hardboiledfrog/smt-zvs-driver/images/P1020684.JPG

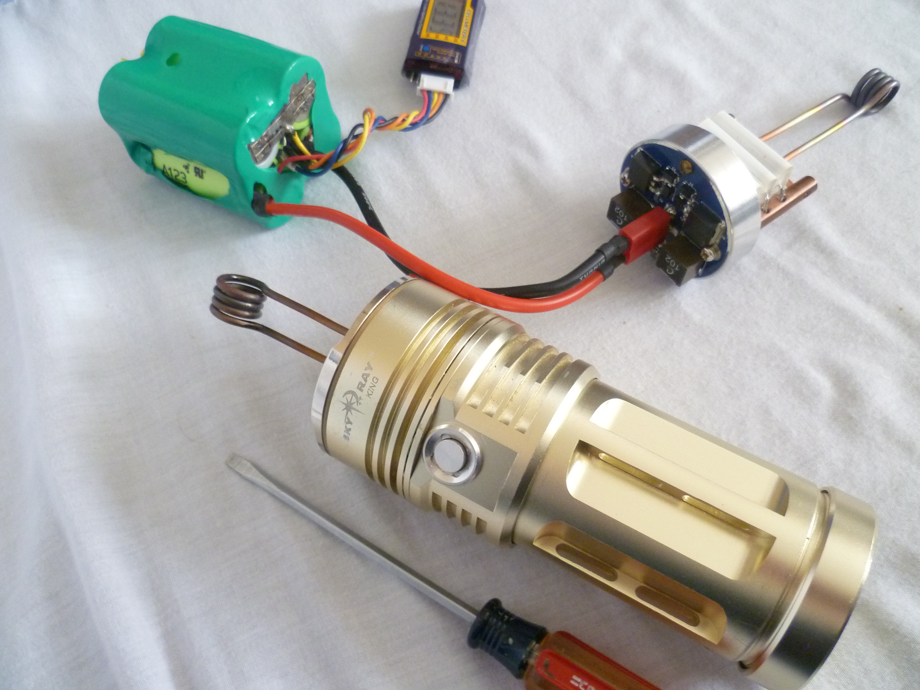
images/P1020684.JPG
