hardboiledfrog/smt-zvs-driver/images/IMG_20150707_065902.jpg

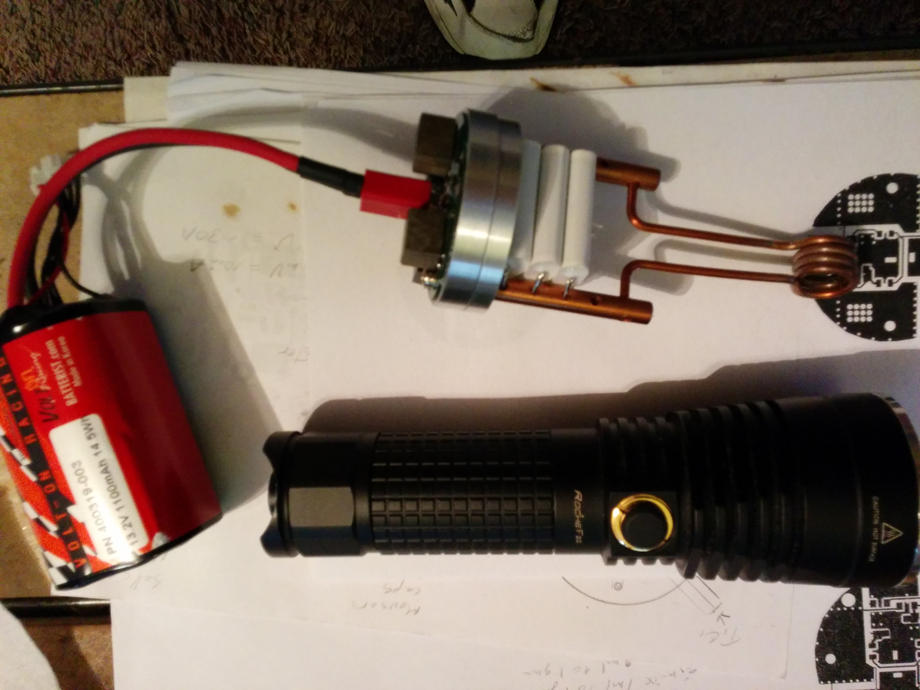
images/IMG_20150707_065902.jpg
