hardboiledfrog/smt-zvs-driver/images/ih-VA.png

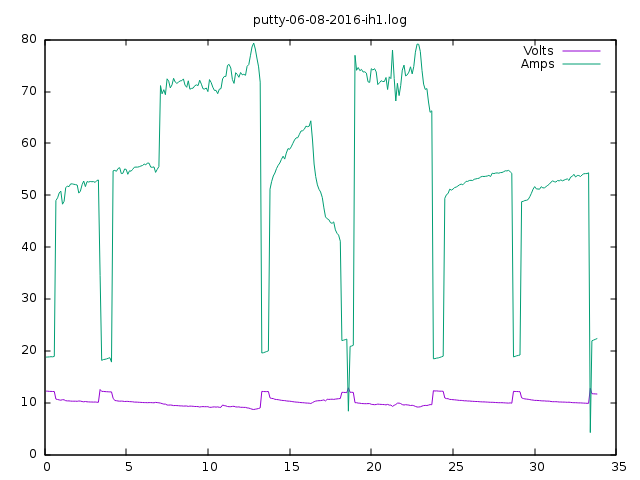
images/ih-VA.png
