hardboiledfrog/smt-zvs-driver/images/ih-VAW.png

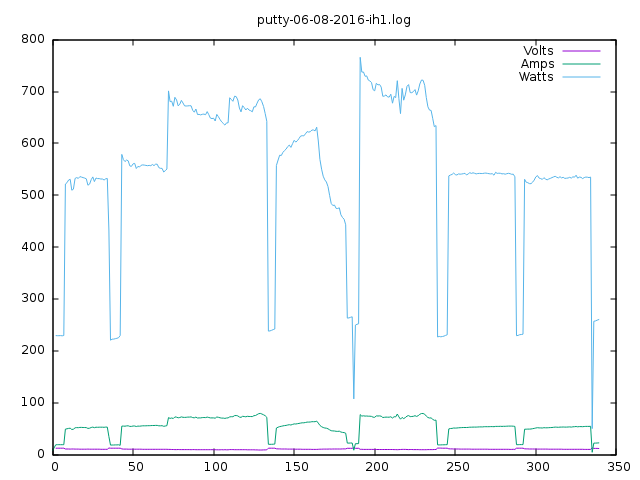
images/ih-VAW.png
