hardboiledfrog/smt-zvs-driver/images/IMG_20150707_065633.jpg

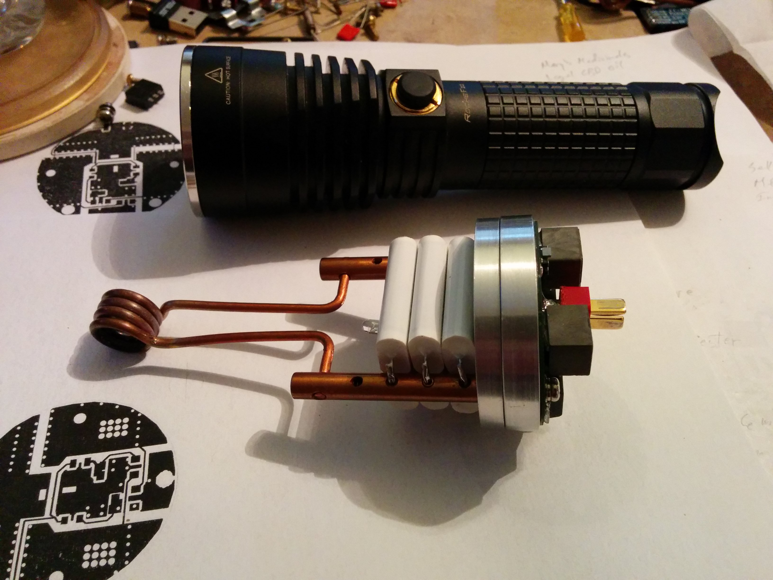
images/IMG_20150707_065633.jpg
