hardboiledfrog/smt-zvs-driver/images/IMG_20150707_065652.jpg

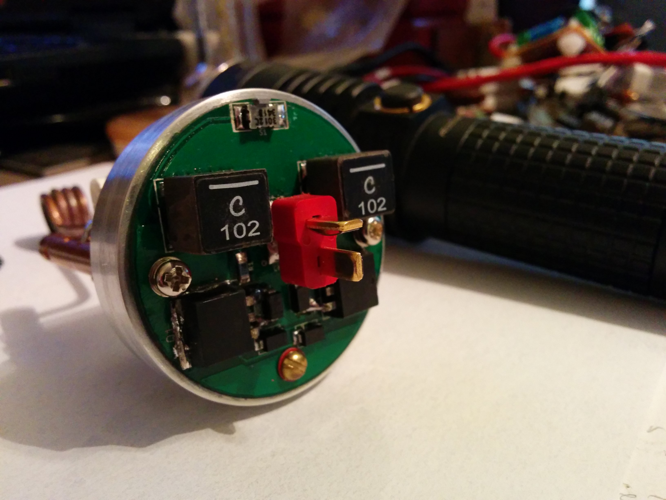
images/IMG_20150707_065652.jpg
