hardboiledfrog/smt-zvs-driver/images/IMG_20150707_065724.jpg

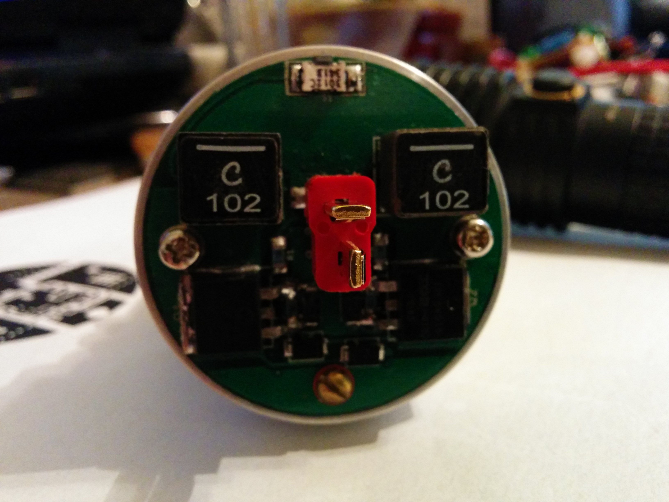
images/IMG_20150707_065724.jpg
