hardboiledfrog/smt-zvs-driver/images/IMG_20160604_112423.jpg

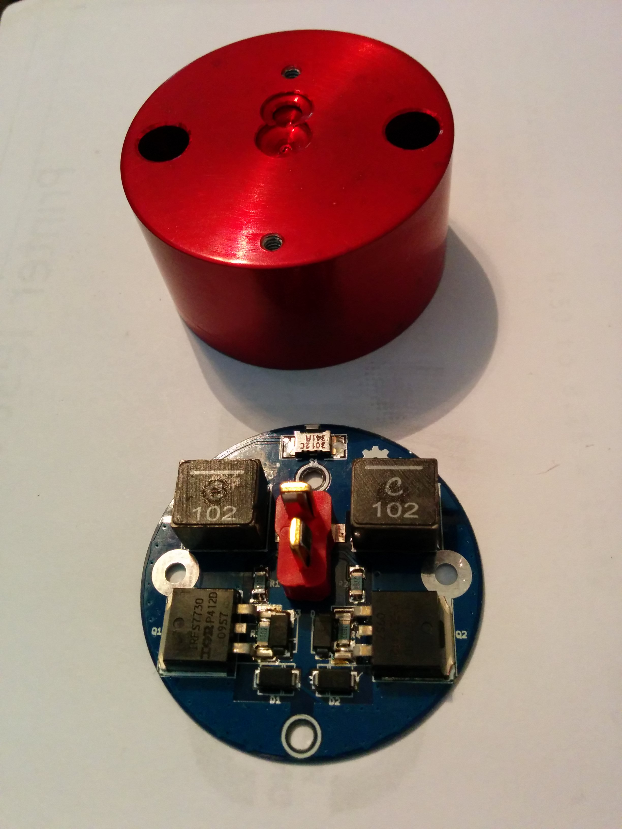
images/IMG_20160604_112423.jpg
