hardboiledfrog/smt-zvs-driver/images/IMG_20160604_112811.jpg

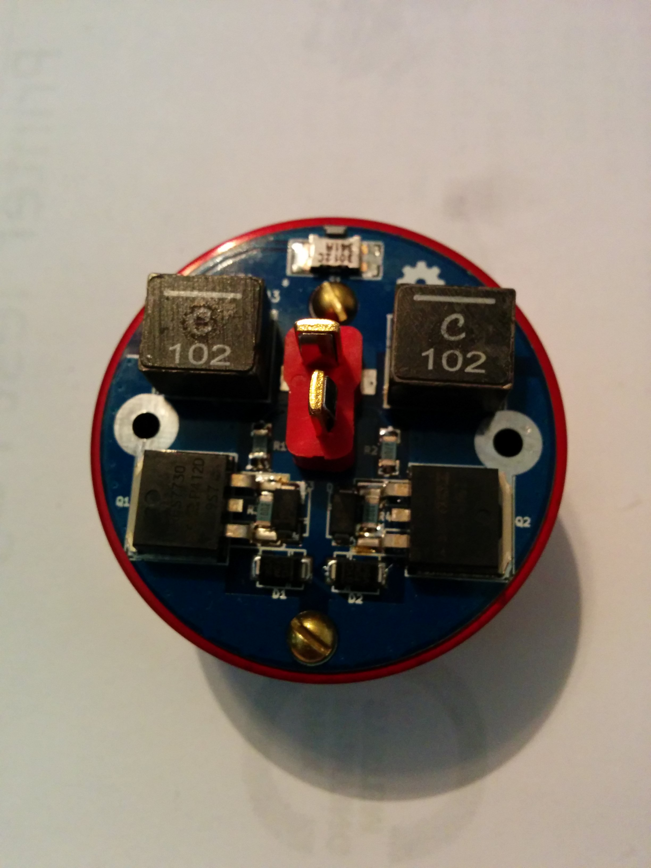
images/IMG_20160604_112811.jpg
