hardboiledfrog/smt-zvs-driver/images/IMG_20160604_112840.jpg

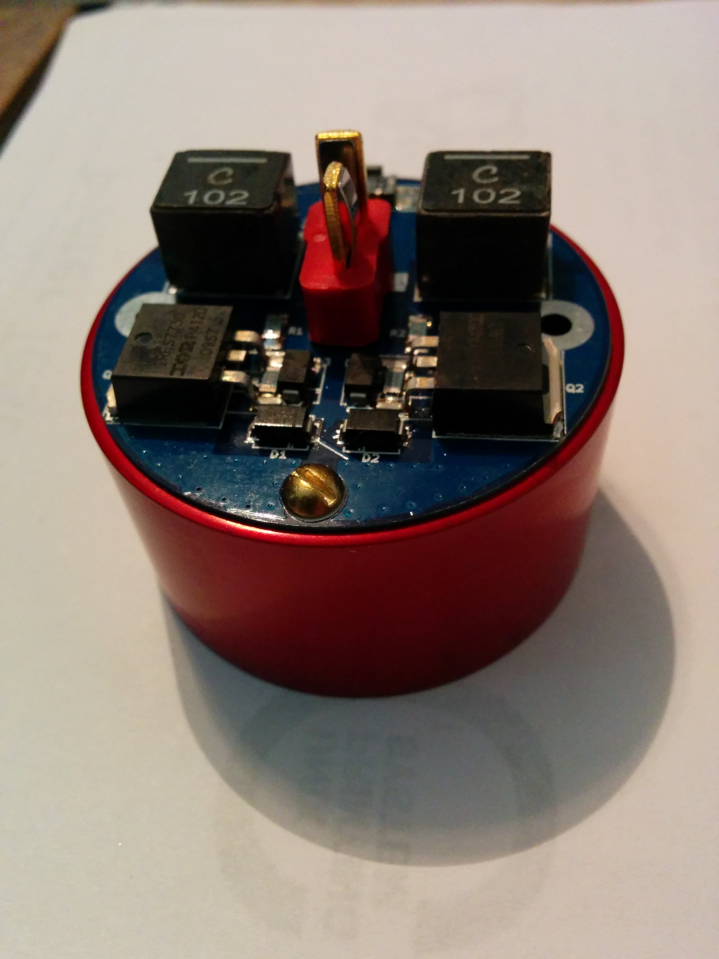
images/IMG_20160604_112840.jpg
