hardboiledfrog/smt-zvs-driver/images/IMG_20160604_114358.jpg

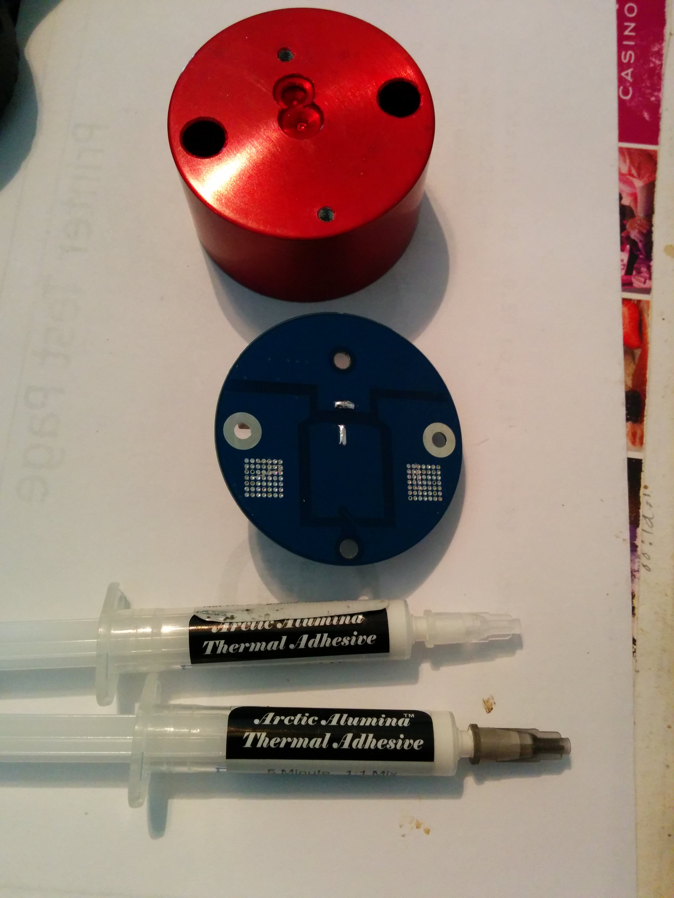
images/IMG_20160604_114358.jpg
