hardboiledfrog/smt-zvs-driver/images/IMG_20160604_115838.jpg

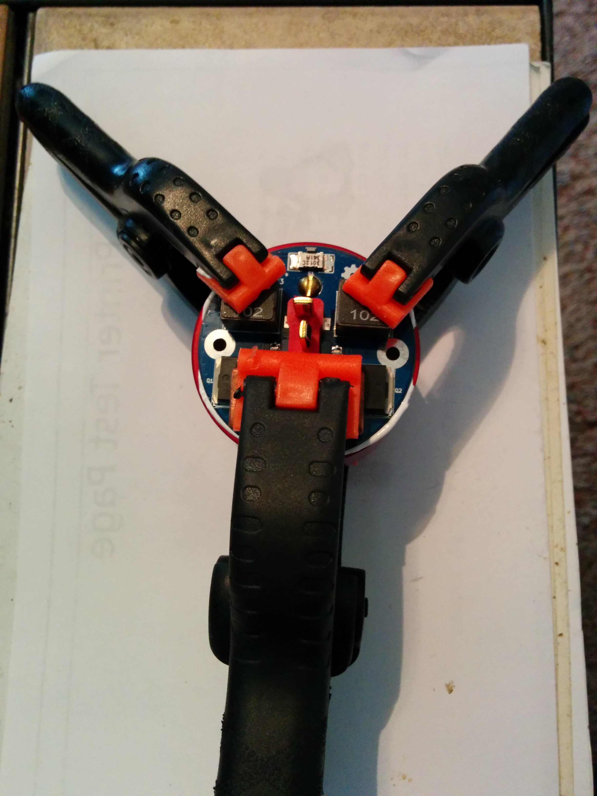
images/IMG_20160604_115838.jpg
