hardboiledfrog/smt-zvs-driver/images/IMG_20160604_115855.jpg

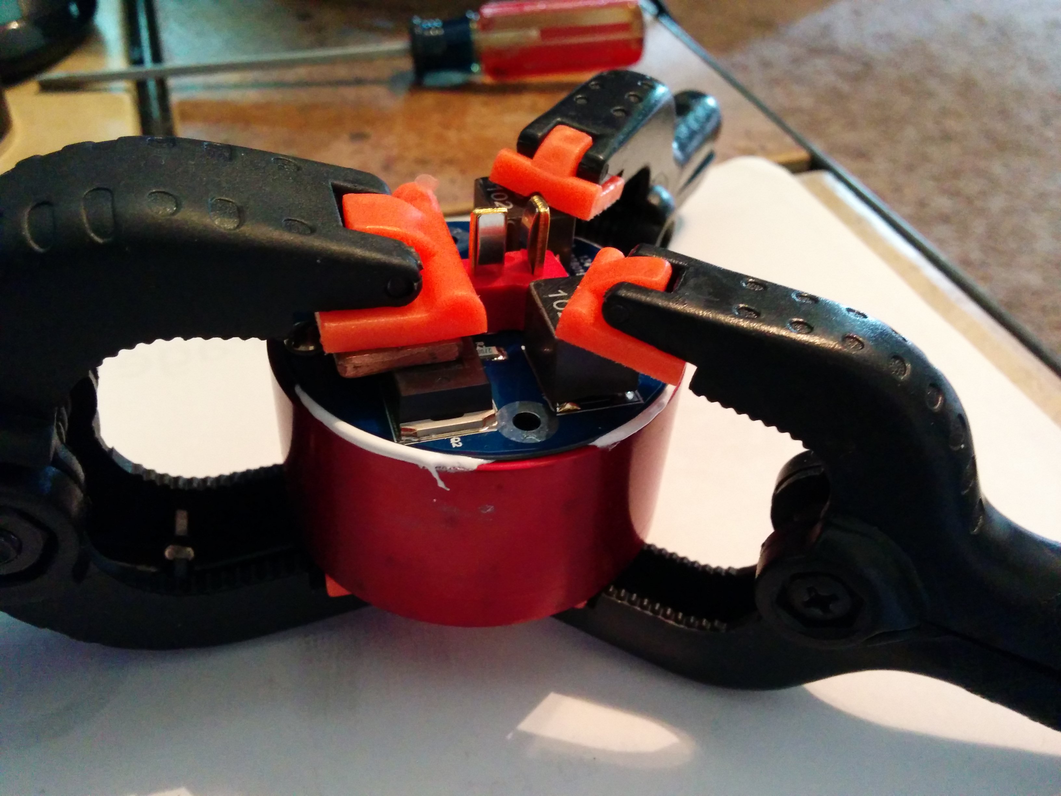
images/IMG_20160604_115855.jpg
