hardboiledfrog/smt-zvs-driver/images/IMG_20160604_143417.jpg

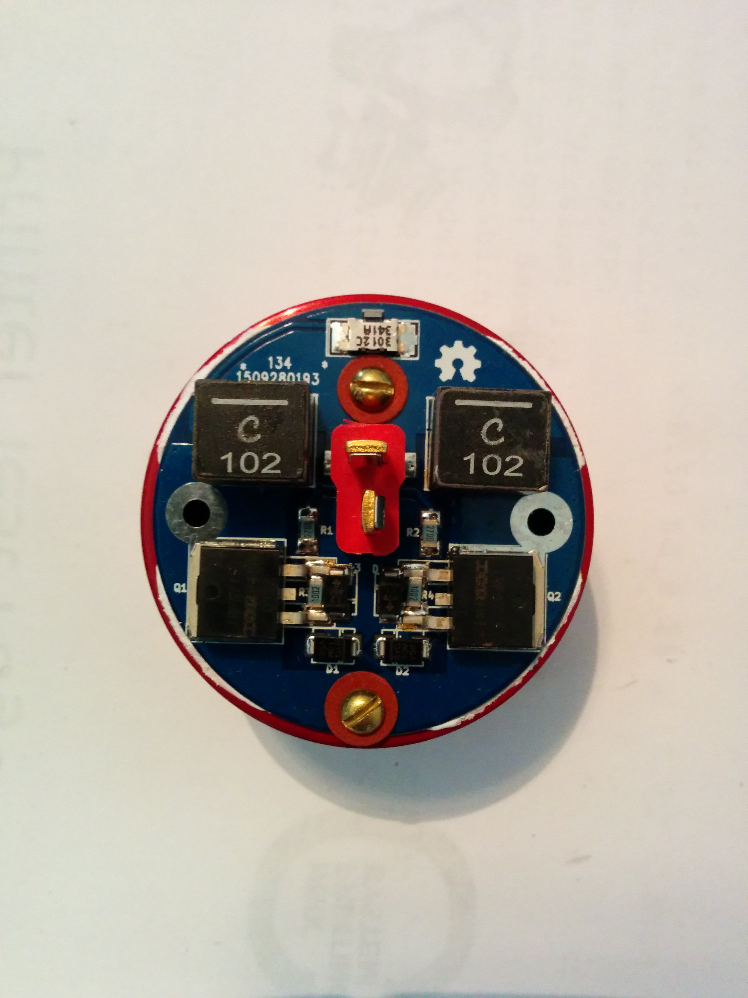
images/IMG_20160604_143417.jpg
