hardboiledfrog/smt-zvs-driver/images/IMG_20160604_143437.jpg

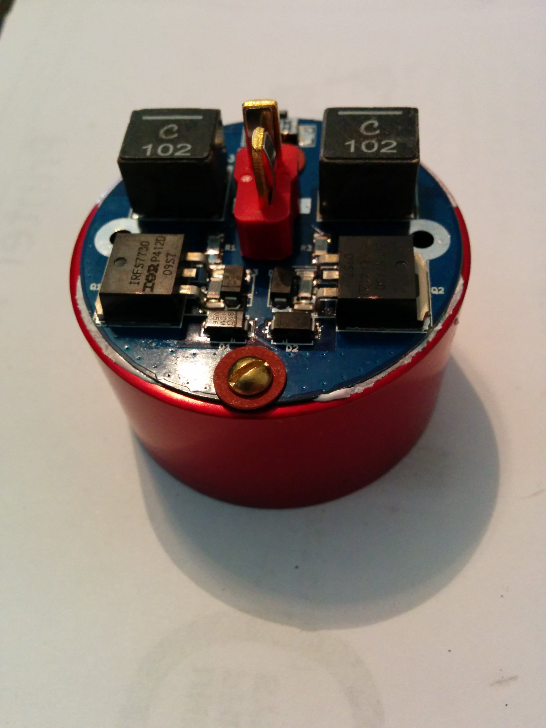
images/IMG_20160604_143437.jpg
