hardboiledfrog/smt-zvs-driver/images/IMG_20160604_143456.jpg

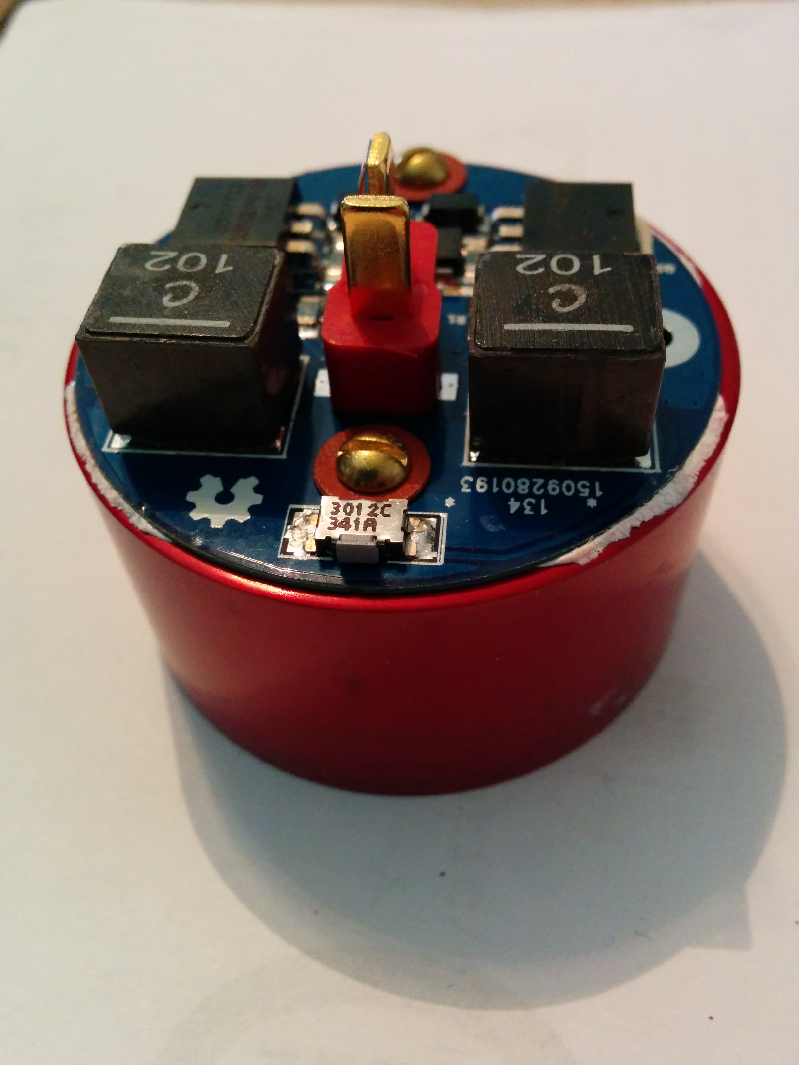
images/IMG_20160604_143456.jpg
