hardboiledfrog/smt-zvs-driver/images/IMG_20160604_174850.jpg

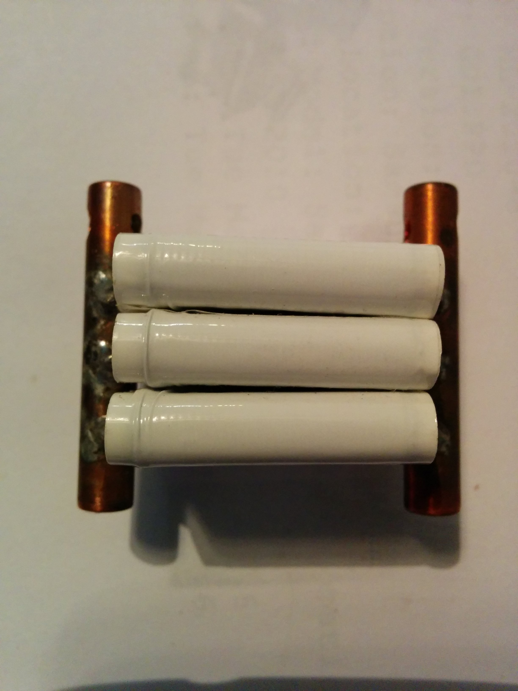
images/IMG_20160604_174850.jpg
