hardboiledfrog/smt-zvs-driver/images/IMG_20160604_174921.jpg

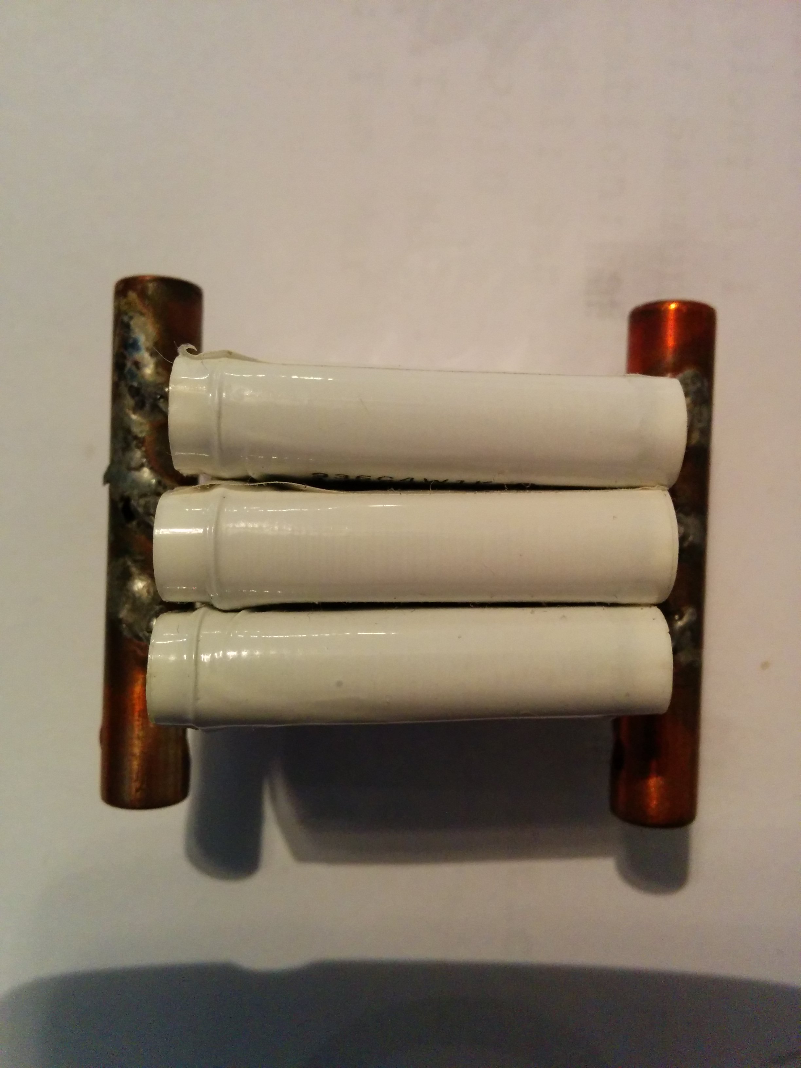
images/IMG_20160604_174921.jpg
