hardboiledfrog/smt-zvs-driver/images/IMG_20160604_174946.jpg

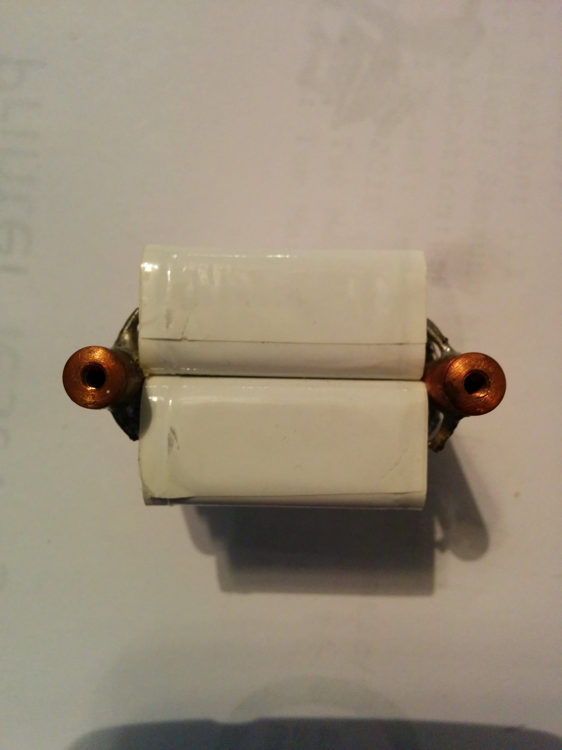
images/IMG_20160604_174946.jpg
