hardboiledfrog/smt-zvs-driver/images/IMG_20160604_175032.jpg

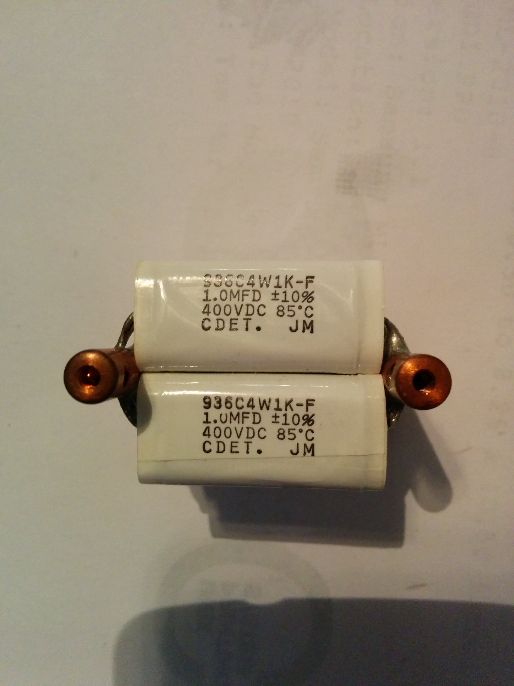
images/IMG_20160604_175032.jpg
