hardboiledfrog/smt-zvs-driver/images/IMG_20160608_041023.jpg

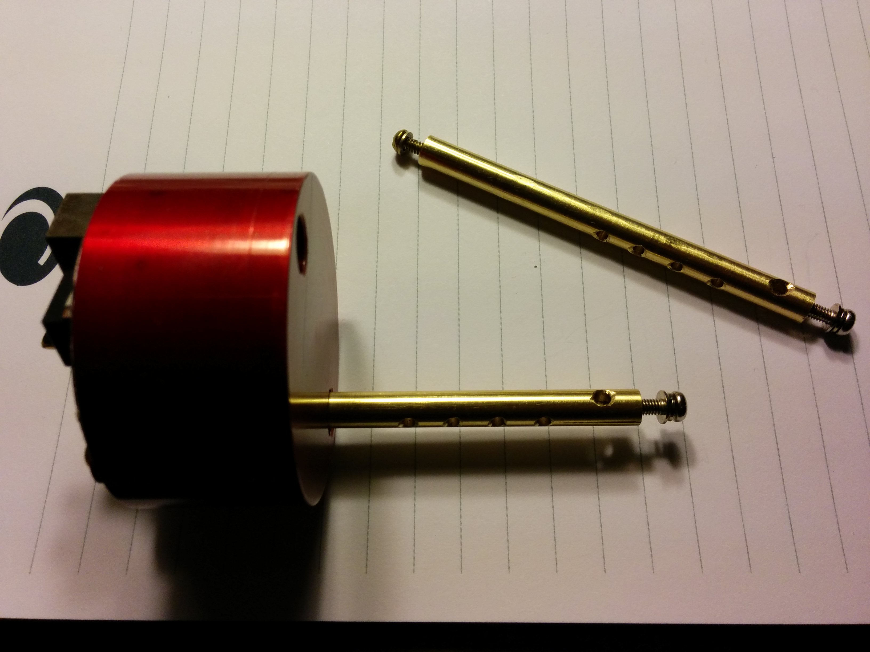
images/IMG_20160608_041023.jpg
