hardboiledfrog/smt-zvs-driver/images/IMG_20160608_041058.jpg

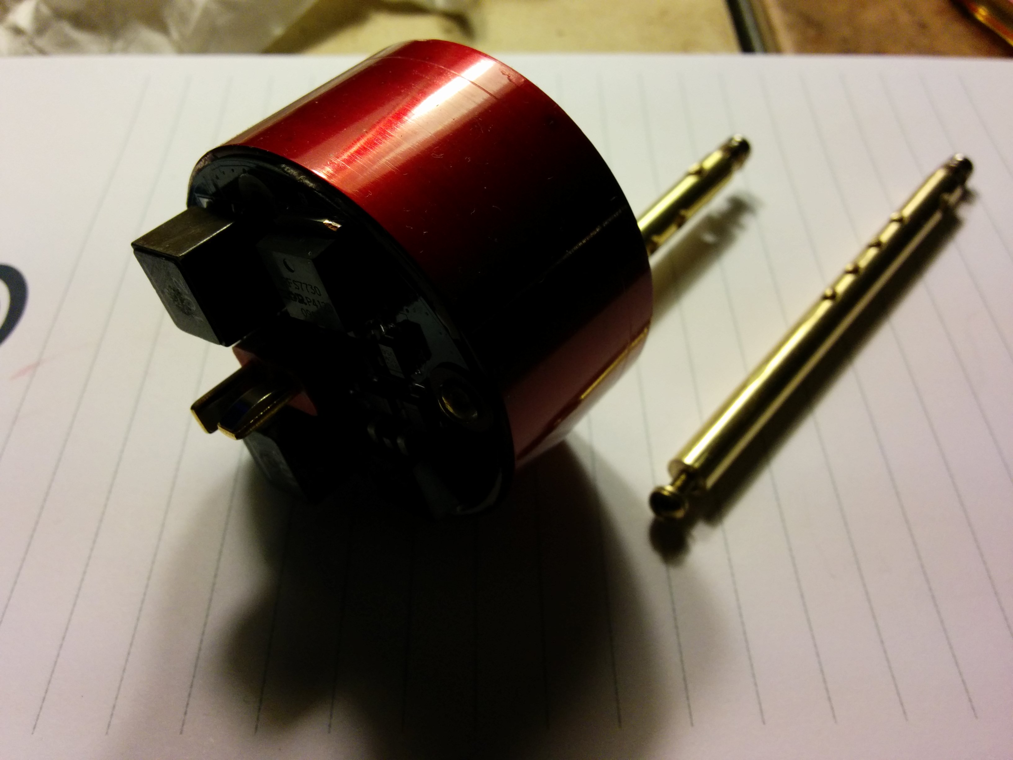
images/IMG_20160608_041058.jpg
