hardboiledfrog/smt-zvs-driver/images/IMG_20160608_041148.jpg

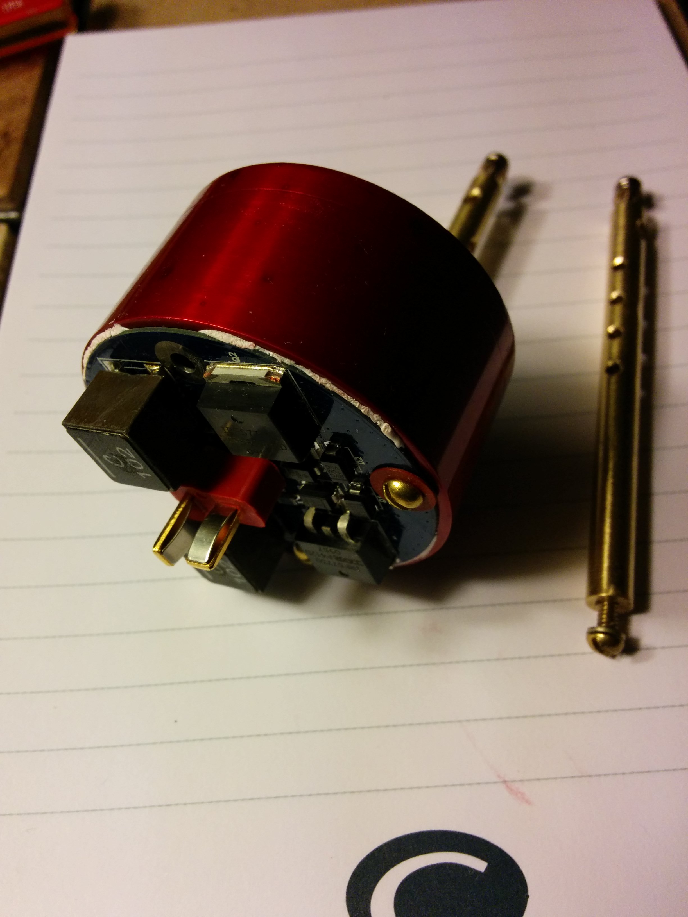
images/IMG_20160608_041148.jpg
