hardboiledfrog/smt-zvs-driver/images/IMG_20160608_041308.jpg

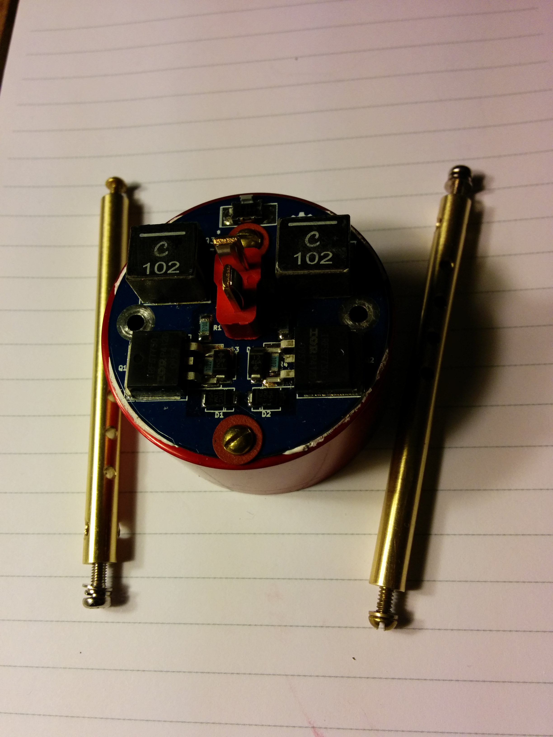
images/IMG_20160608_041308.jpg
