hardboiledfrog/smt-zvs-driver/images/IMG_20160608_041708.jpg

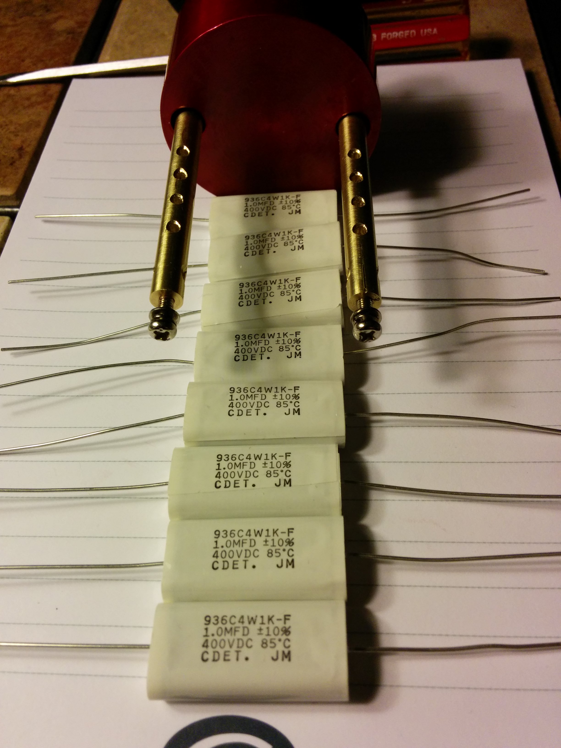
images/IMG_20160608_041708.jpg
