hardboiledfrog/smt-zvs-driver/images/IMG_20160608_041847.jpg

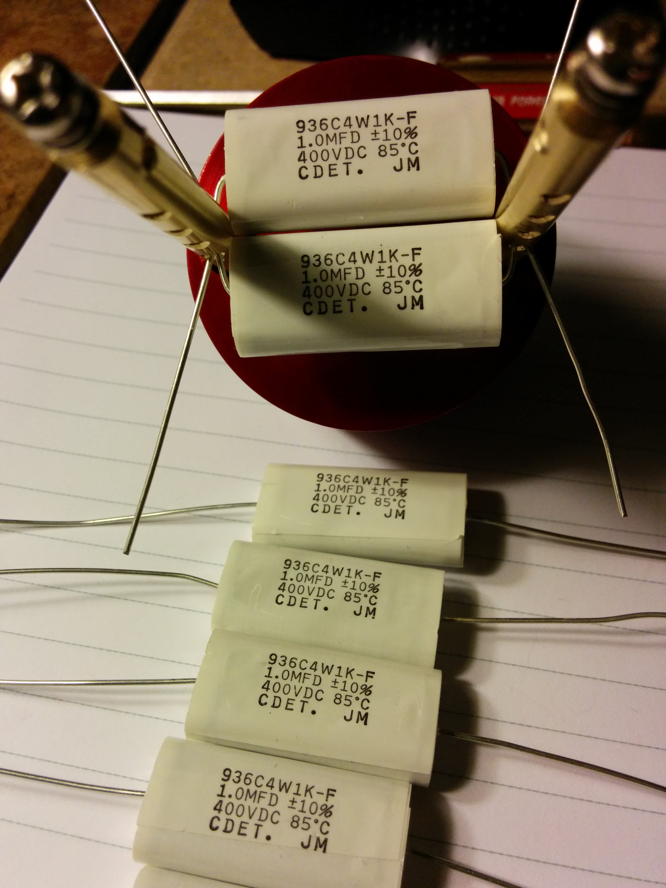
images/IMG_20160608_041847.jpg
