hardboiledfrog/smt-zvs-driver/images/IMG_20160608_041959.jpg

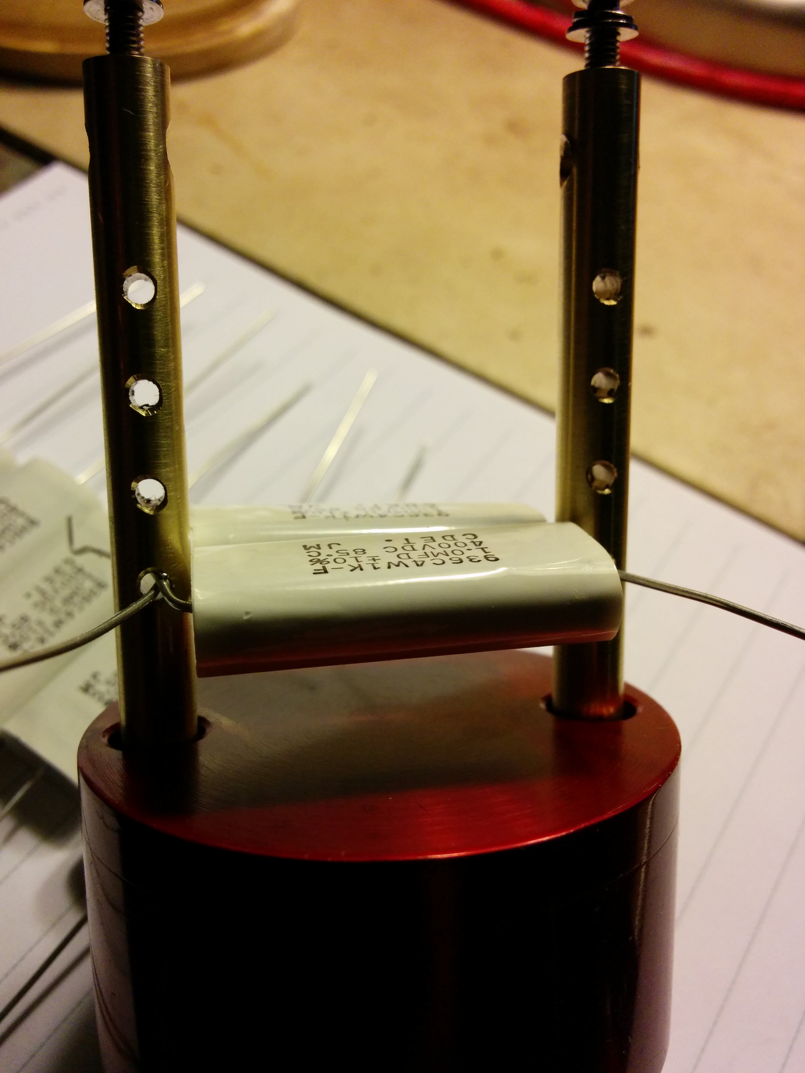
images/IMG_20160608_041959.jpg
