hardboiledfrog/smt-zvs-driver/images/IMG_20160608_042007.jpg

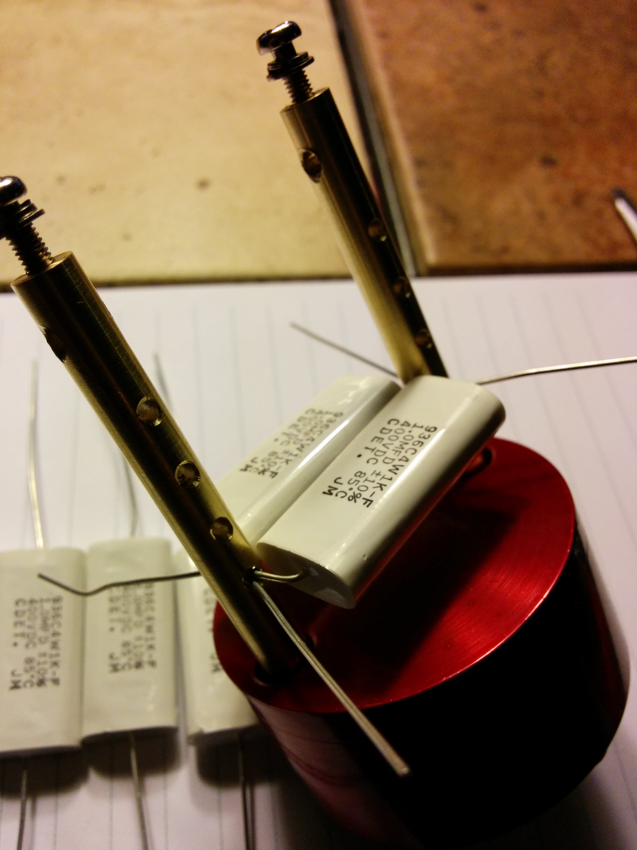
images/IMG_20160608_042007.jpg
