hardboiledfrog/smt-zvs-driver/images/IMG_20160608_043600.jpg

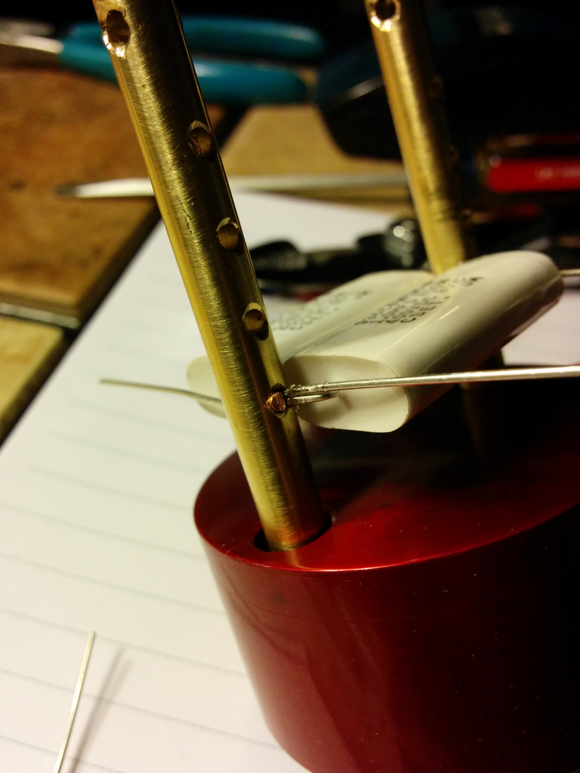
images/IMG_20160608_043600.jpg
