hardboiledfrog/smt-zvs-driver/images/IMG_20160608_043638.jpg

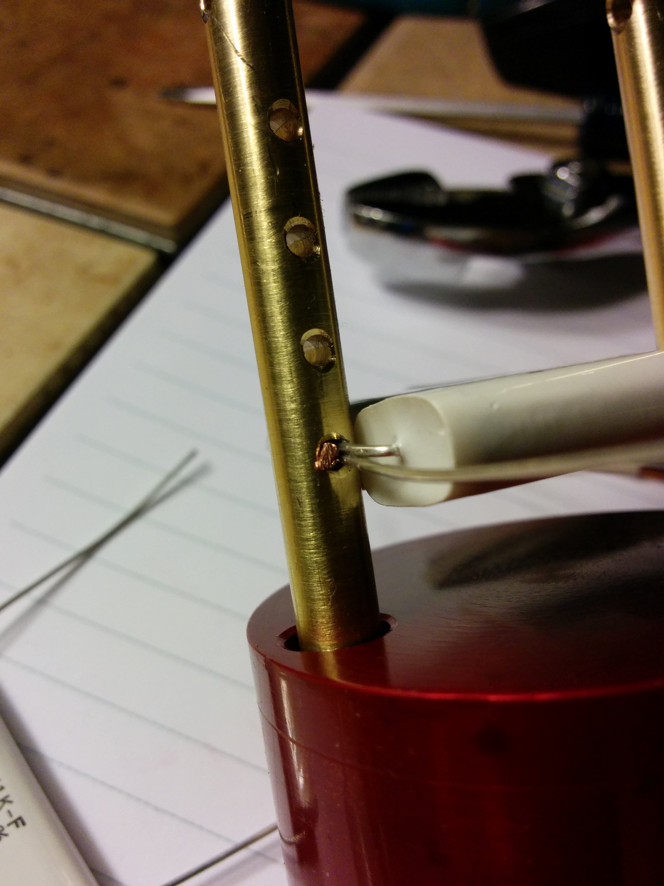
images/IMG_20160608_043638.jpg
