hardboiledfrog/smt-zvs-driver/images/IMG_20160608_043737.jpg

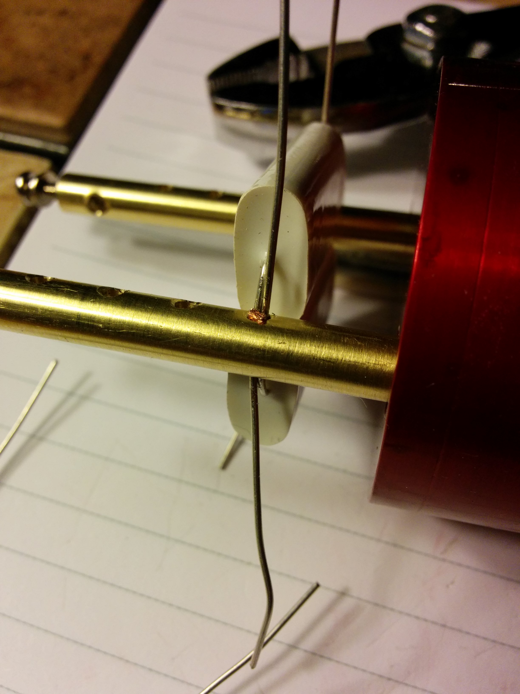
images/IMG_20160608_043737.jpg
