hardboiledfrog/smt-zvs-driver/images/IMG_20160608_044013.jpg

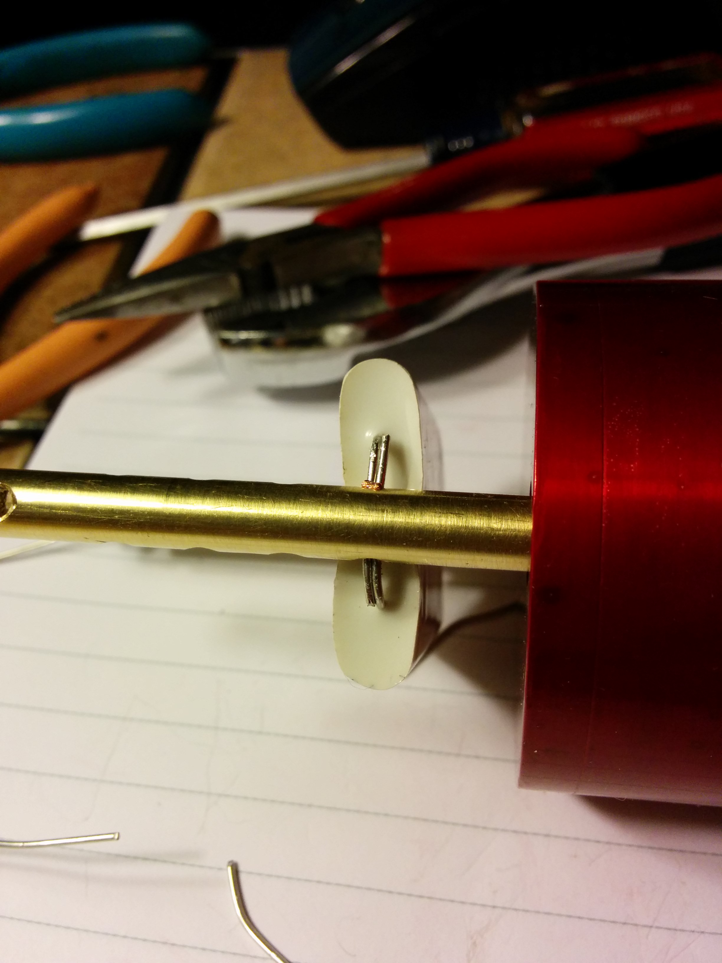
images/IMG_20160608_044013.jpg
