hardboiledfrog/smt-zvs-driver/images/IMG_20160608_044214.jpg

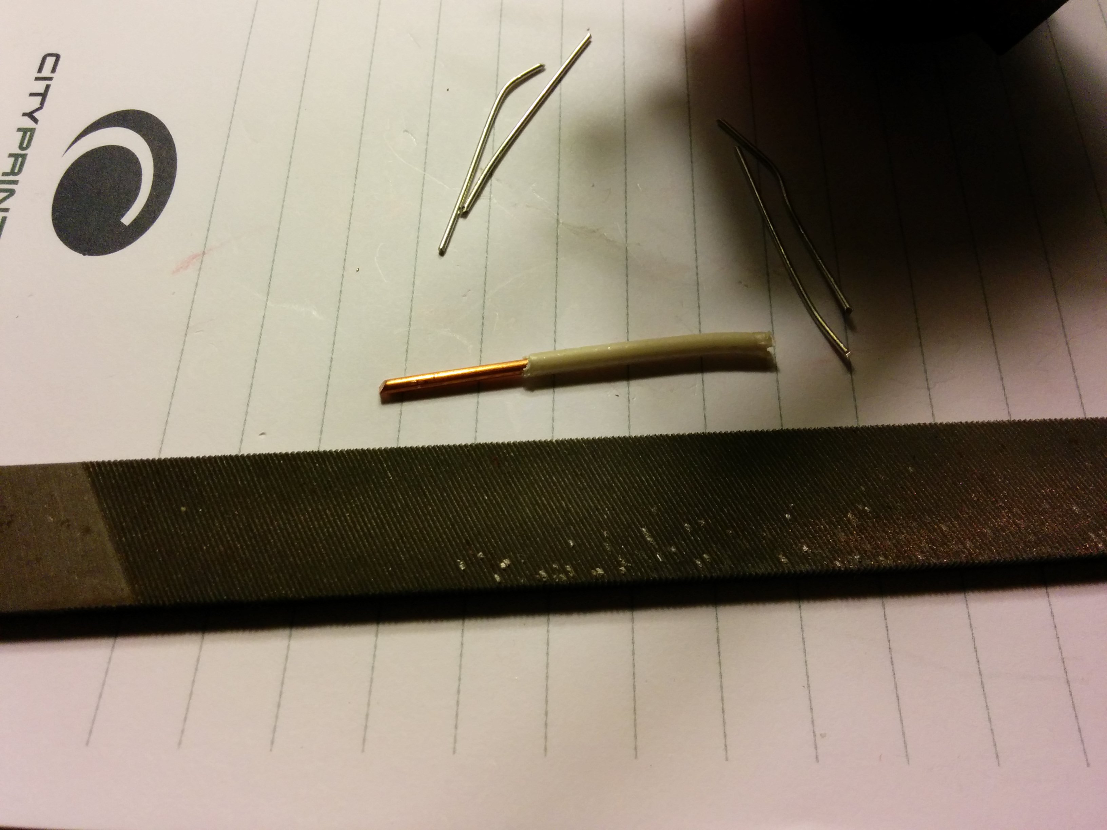
images/IMG_20160608_044214.jpg
