hardboiledfrog/smt-zvs-driver/images/IMG_20160608_044324.jpg

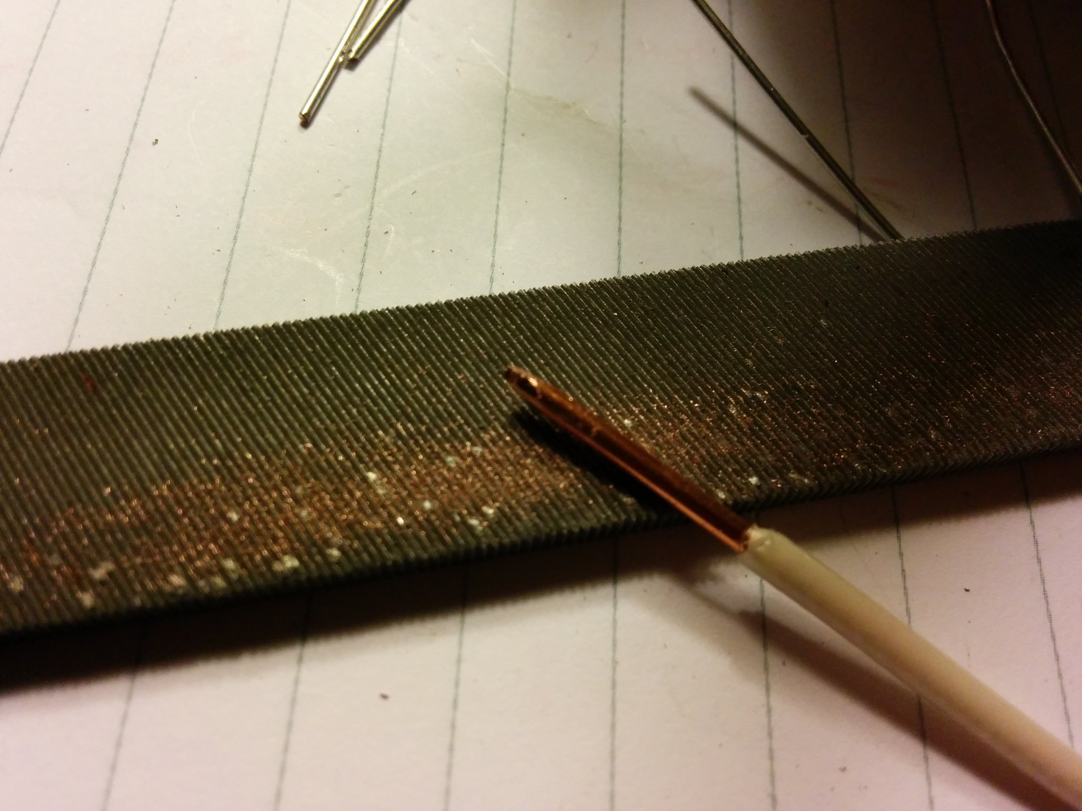
images/IMG_20160608_044324.jpg
