hardboiledfrog/smt-zvs-driver/images/IMG_20160608_044334.jpg

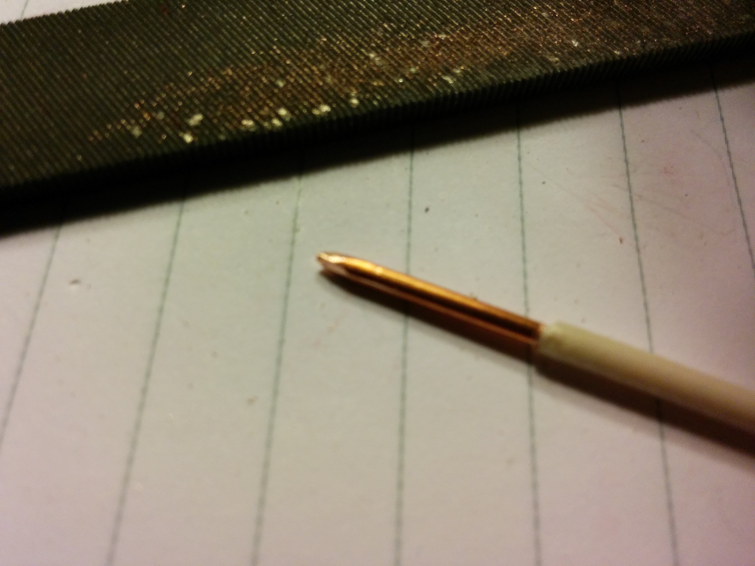
images/IMG_20160608_044334.jpg
