hardboiledfrog/smt-zvs-driver/images/IMG_20160608_044416.jpg

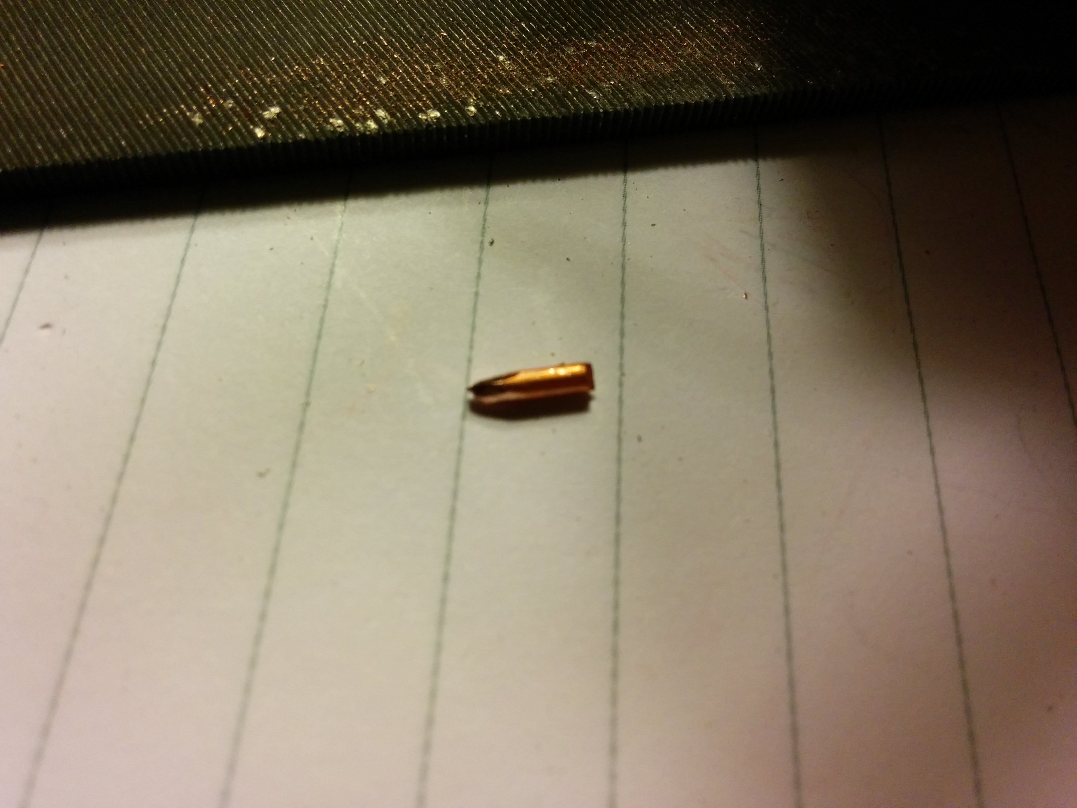
images/IMG_20160608_044416.jpg
