hardboiledfrog/smt-zvs-driver/images/IMG_20160608_044534.jpg

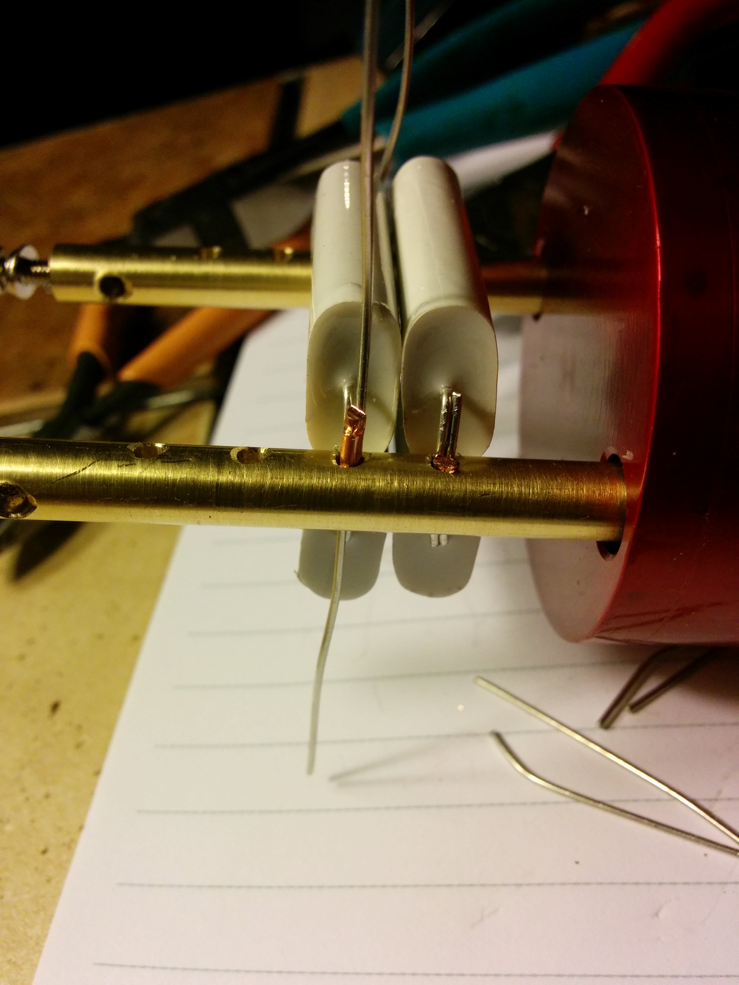
images/IMG_20160608_044534.jpg
