hardboiledfrog/smt-zvs-driver/images/IMG_20160608_044605.jpg

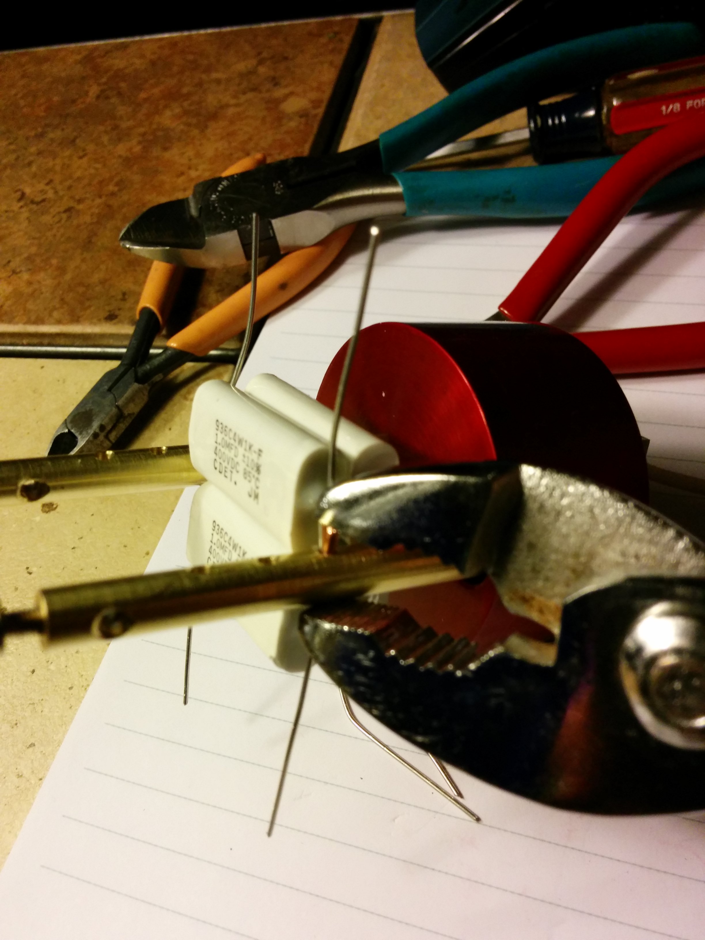
images/IMG_20160608_044605.jpg
