hardboiledfrog/smt-zvs-driver/images/IMG_20160608_044642.jpg

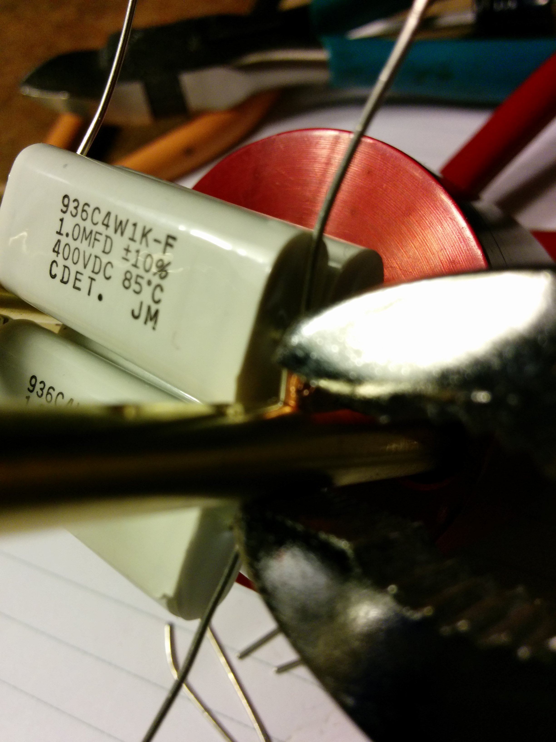
images/IMG_20160608_044642.jpg
