hardboiledfrog/smt-zvs-driver/images/IMG_20160608_044652.jpg

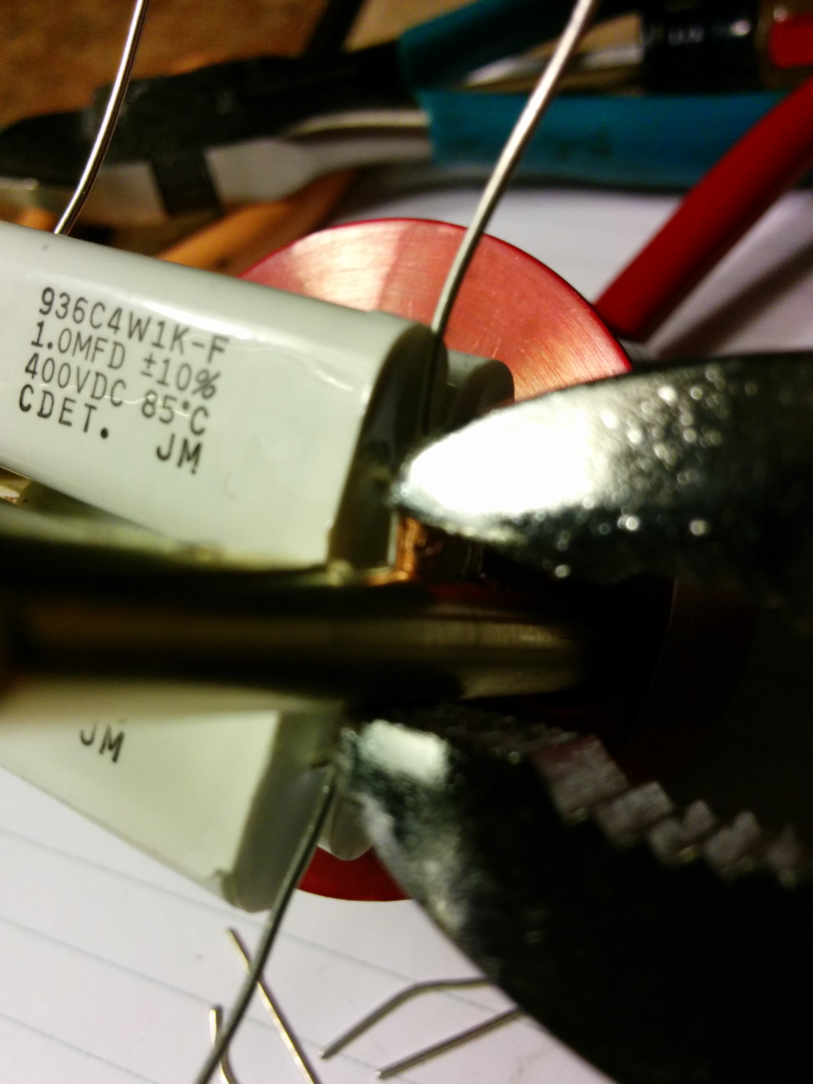
images/IMG_20160608_044652.jpg
