hardboiledfrog/smt-zvs-driver/images/IMG_20160608_044722.jpg

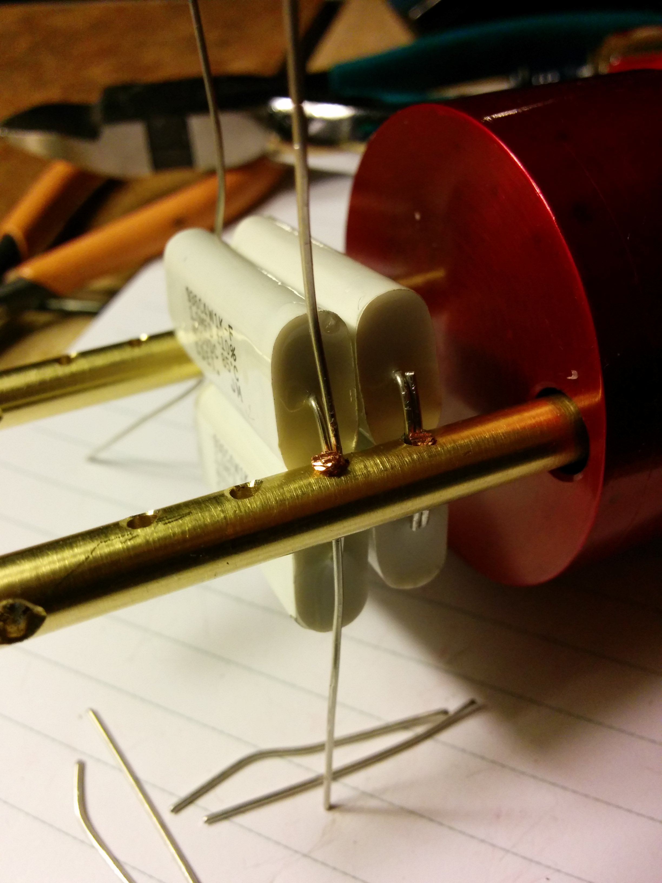
images/IMG_20160608_044722.jpg
