hardboiledfrog/smt-zvs-driver/images/IMG_20160608_044838.jpg

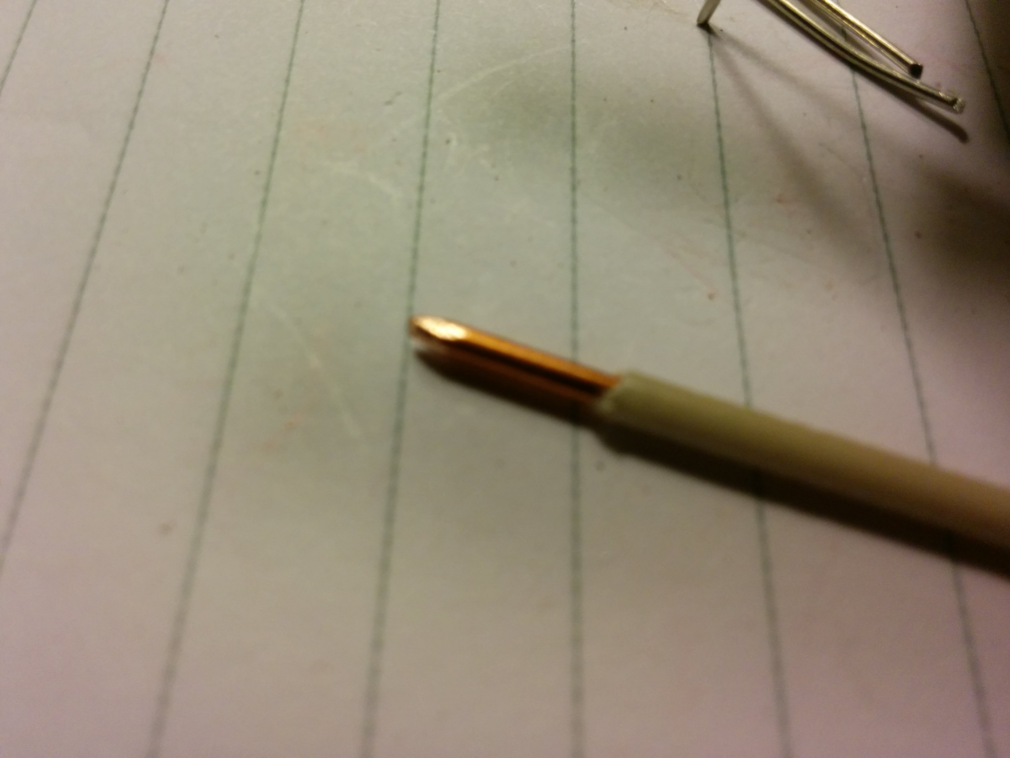
images/IMG_20160608_044838.jpg
