hardboiledfrog/smt-zvs-driver/images/IMG_20160608_044942.jpg

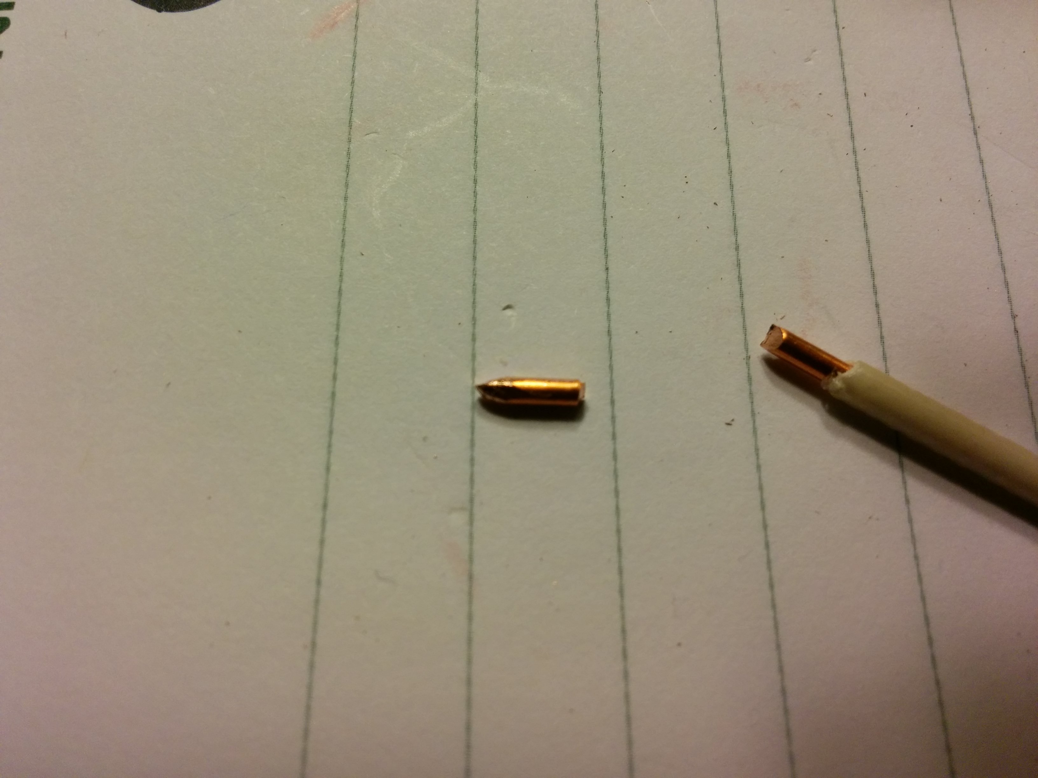
images/IMG_20160608_044942.jpg
