hardboiledfrog/smt-zvs-driver/images/IMG_20160608_045026.jpg

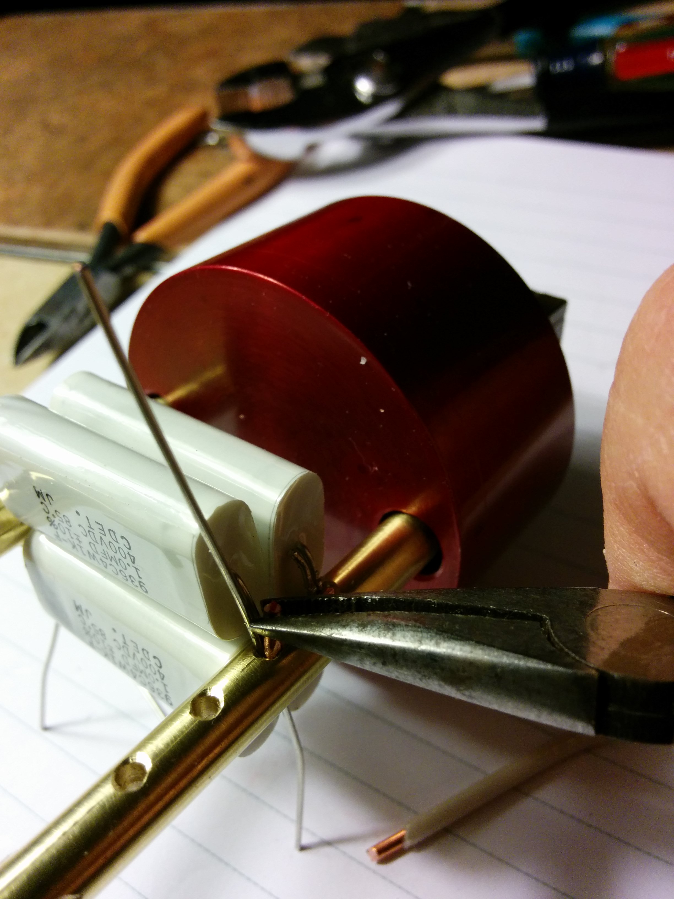
images/IMG_20160608_045026.jpg
