hardboiledfrog/smt-zvs-driver/images/IMG_20160608_045140.jpg

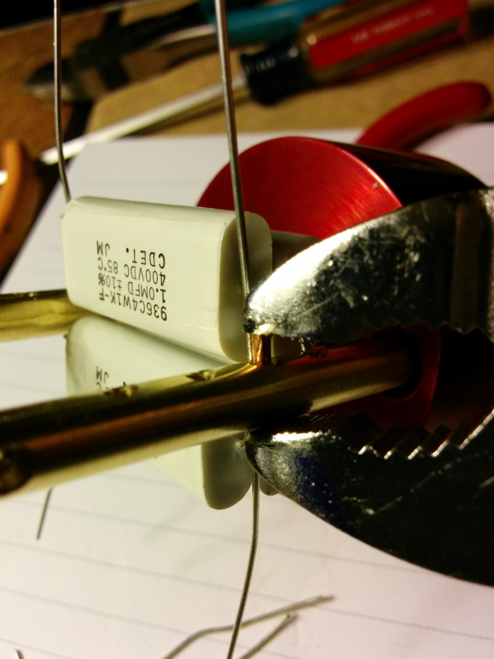
images/IMG_20160608_045140.jpg
