hardboiledfrog/smt-zvs-driver/images/IMG_20160608_045707.jpg

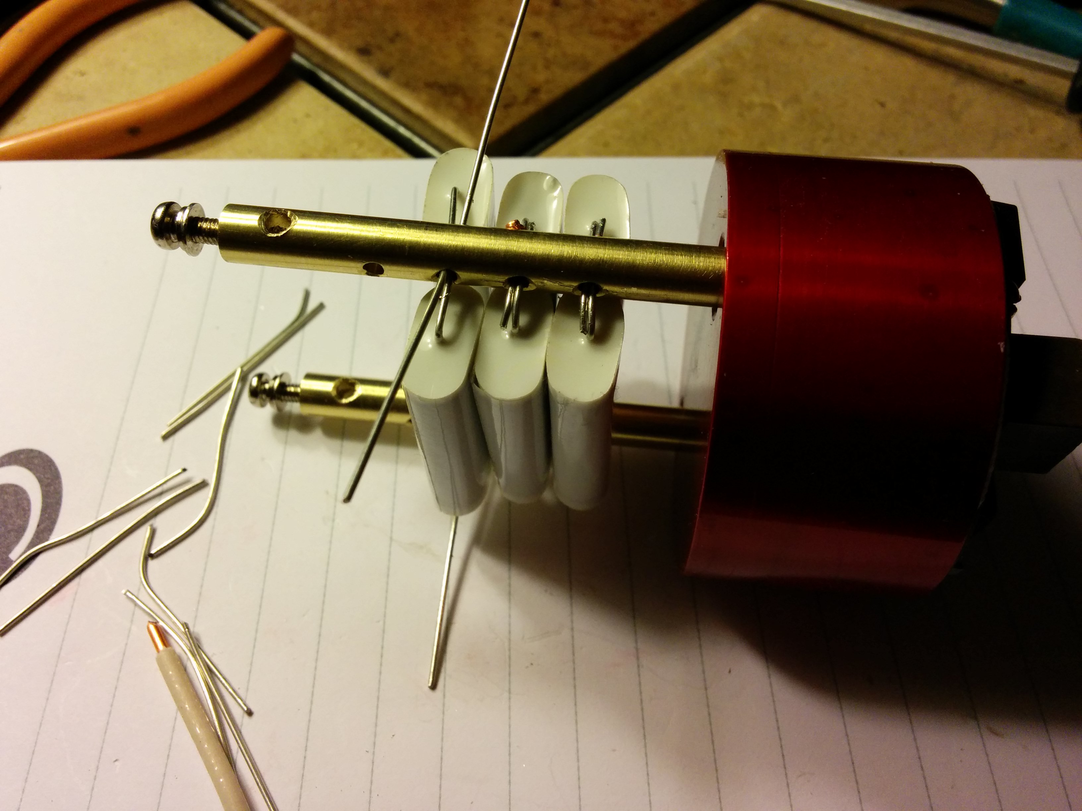
images/IMG_20160608_045707.jpg
