hardboiledfrog/smt-zvs-driver/images/IMG_20160608_053028.jpg

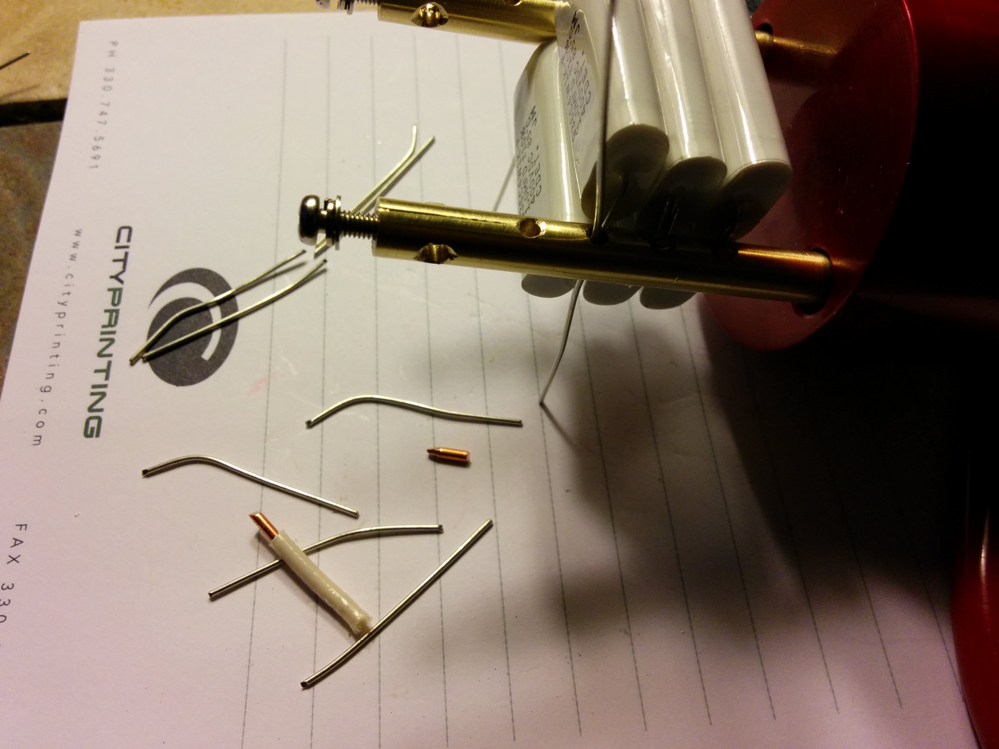
images/IMG_20160608_053028.jpg
