hardboiledfrog/smt-zvs-driver/images/IMG_20160608_054439.jpg

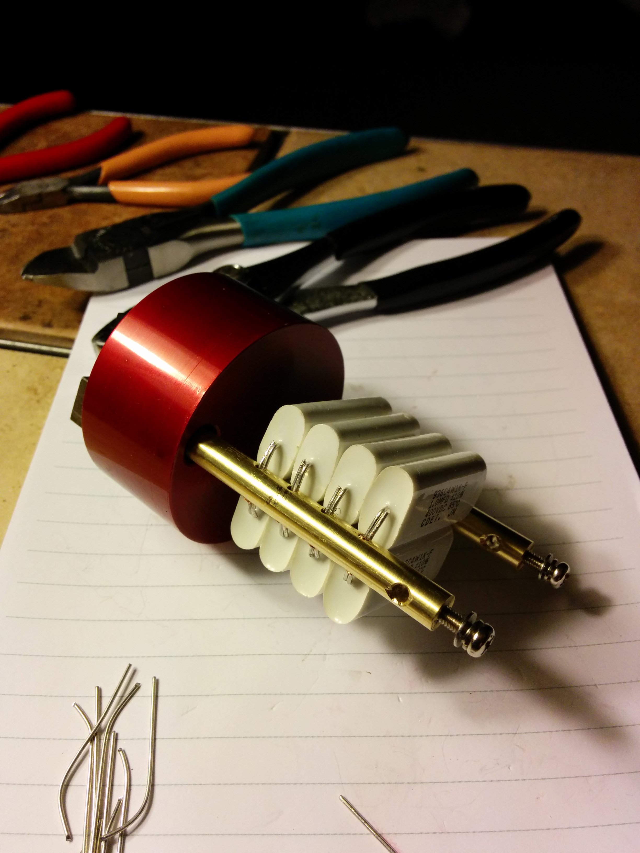
images/IMG_20160608_054439.jpg
