hardboiledfrog/smt-zvs-driver/images/IMG_20160608_054636.jpg

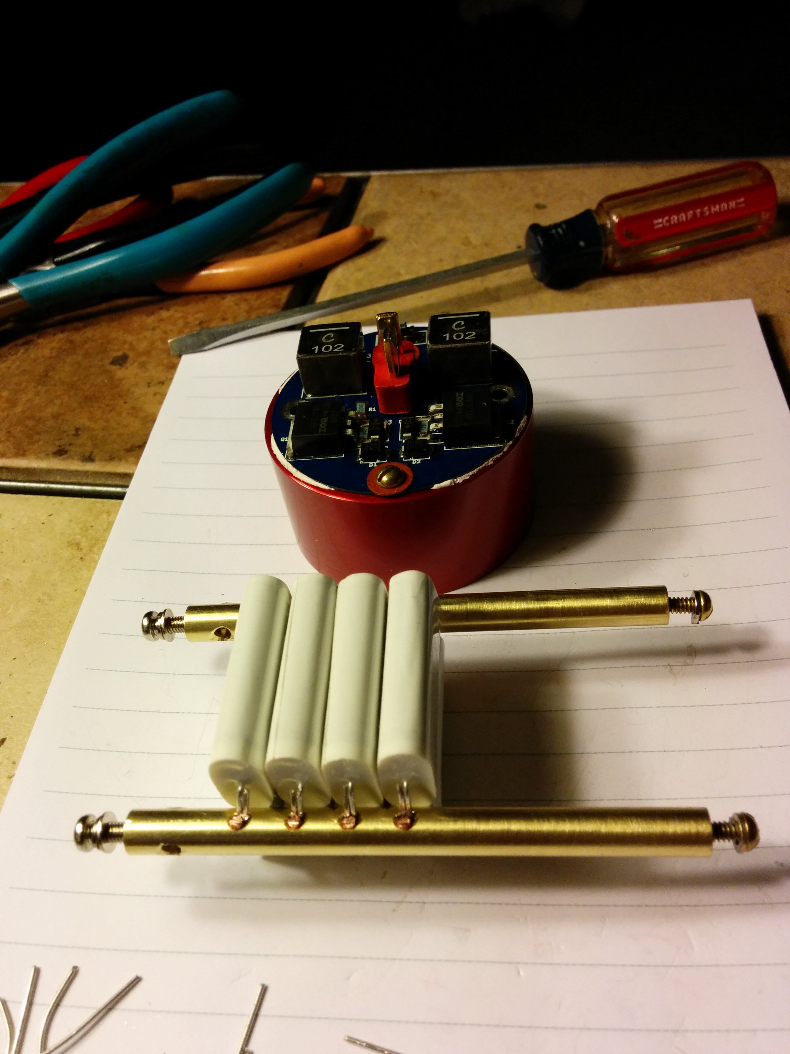
images/IMG_20160608_054636.jpg
