hardboiledfrog/smt-zvs-driver/images/IMG_20160608_054732.jpg

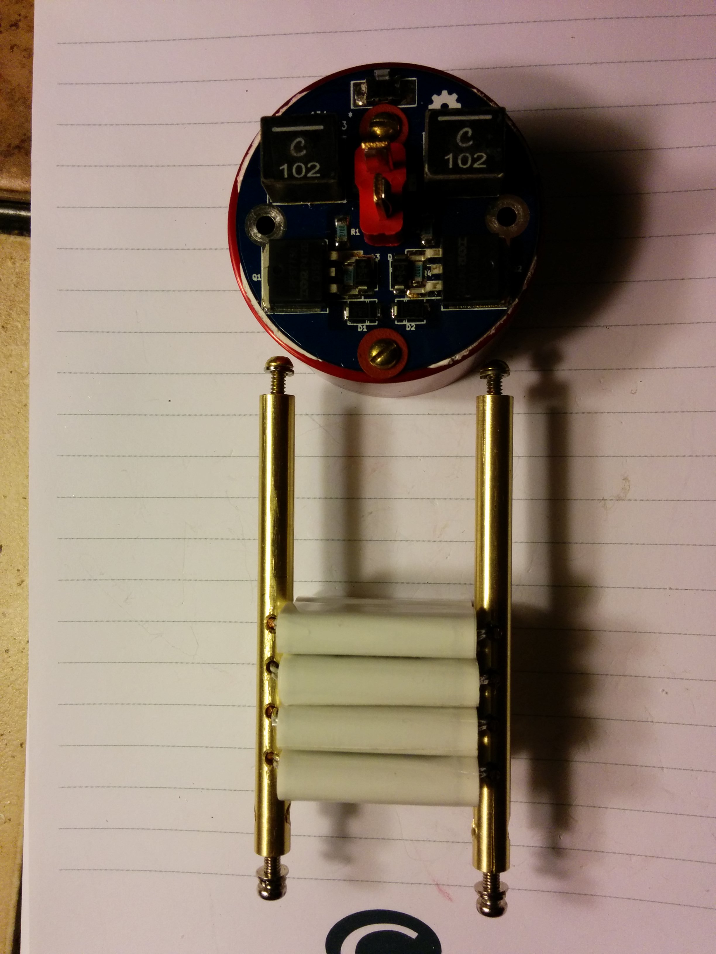
images/IMG_20160608_054732.jpg
