hardboiledfrog/smt-zvs-driver/images/IMG_20160608_055737.jpg

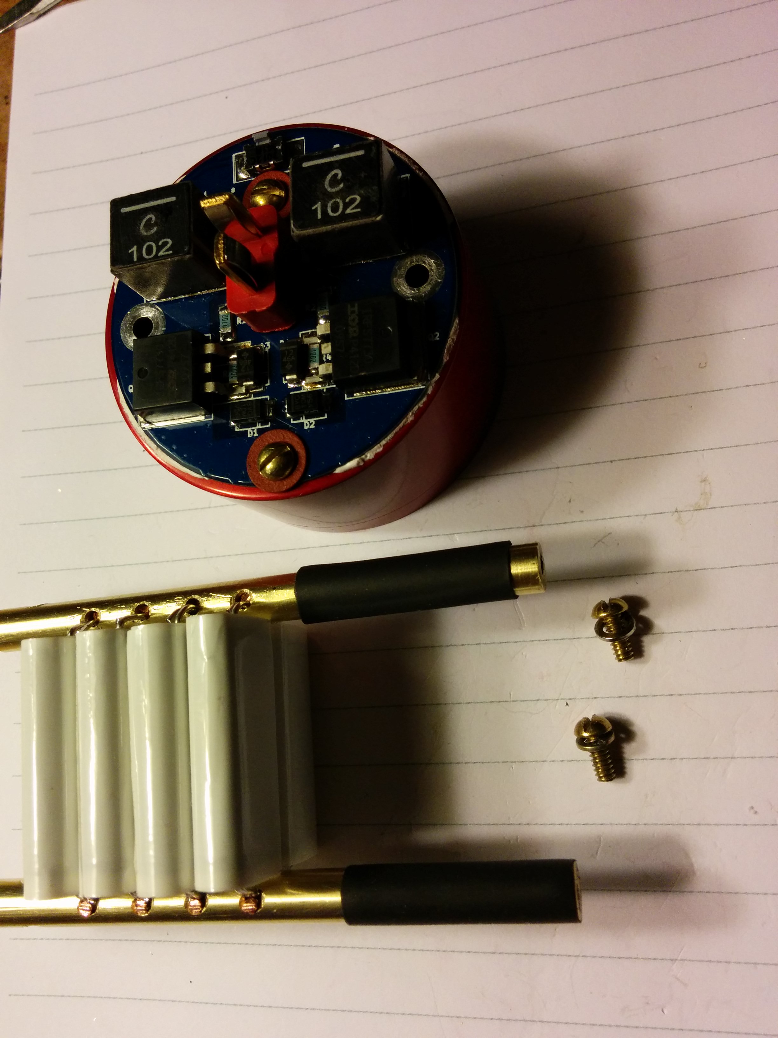
images/IMG_20160608_055737.jpg
