hardboiledfrog/smt-zvs-driver/images/IMG_20160608_063457.jpg

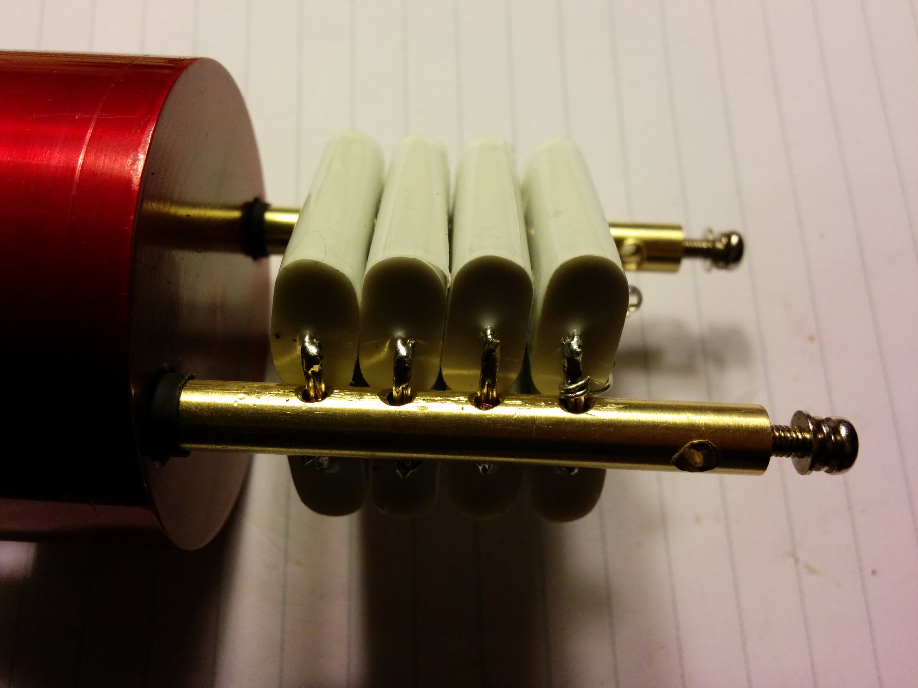
images/IMG_20160608_063457.jpg
