hardboiledfrog/smt-zvs-driver/images/IMG_20160608_063544.jpg

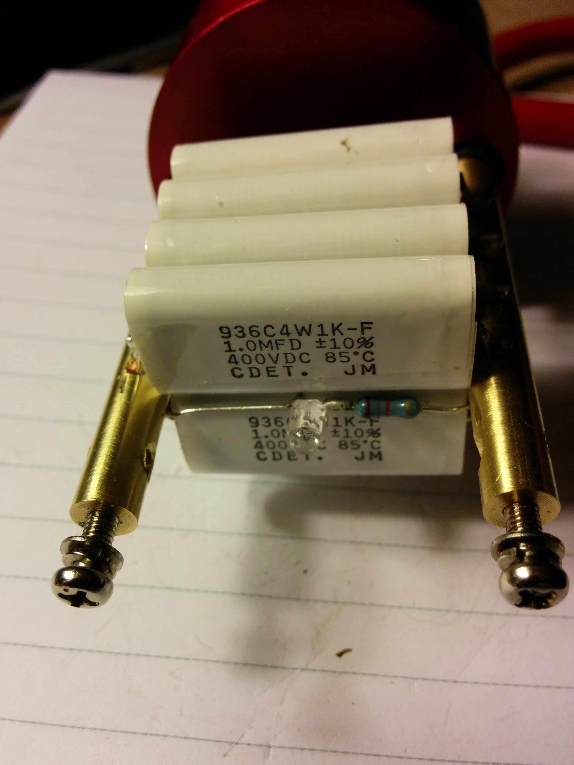
images/IMG_20160608_063544.jpg
