hardboiledfrog/smt-zvs-driver/images/IMG_20160608_063653.jpg

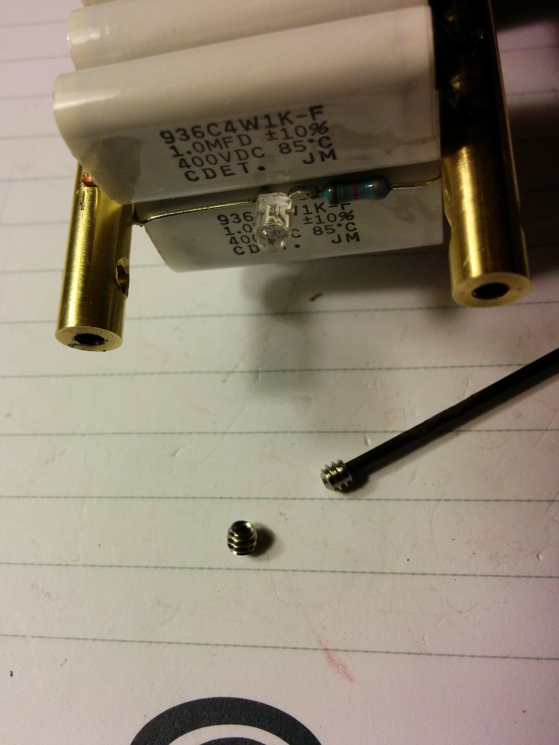
images/IMG_20160608_063653.jpg
