hardboiledfrog/smt-zvs-driver/images/IMG_20160608_071115.jpg

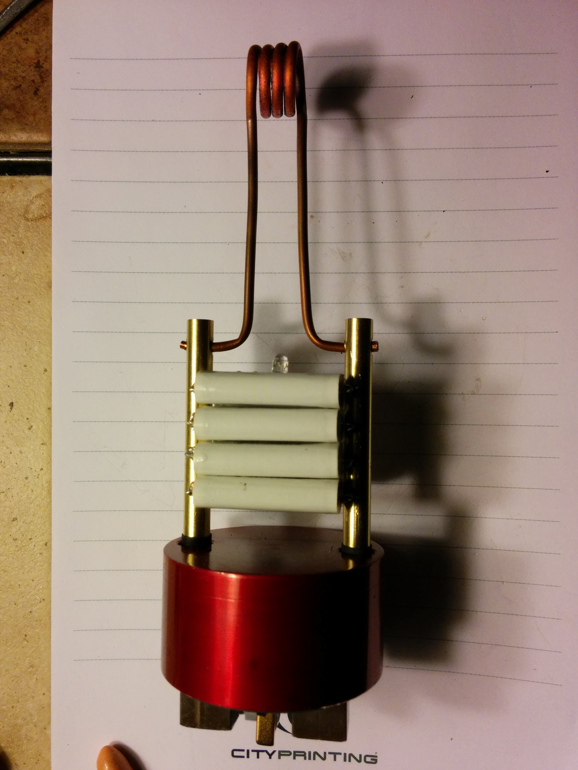
images/IMG_20160608_071115.jpg
