hardboiledfrog/smt-zvs-driver/images/IMG_20160608_071130.jpg

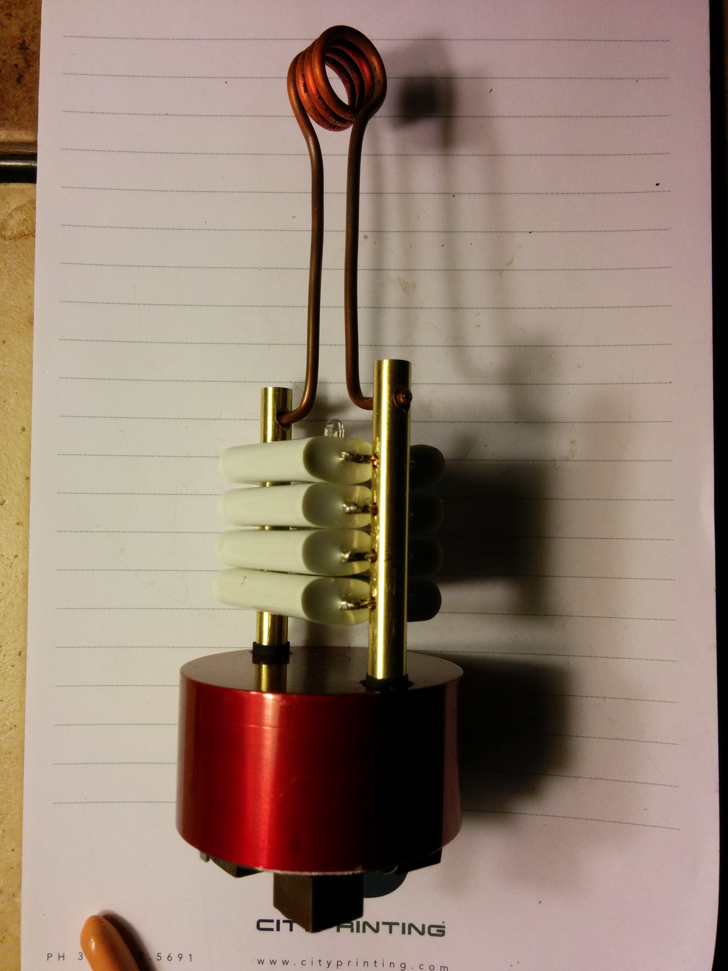
images/IMG_20160608_071130.jpg
