hardboiledfrog/smt-zvs-driver/images/IMG_20160608_071202.jpg

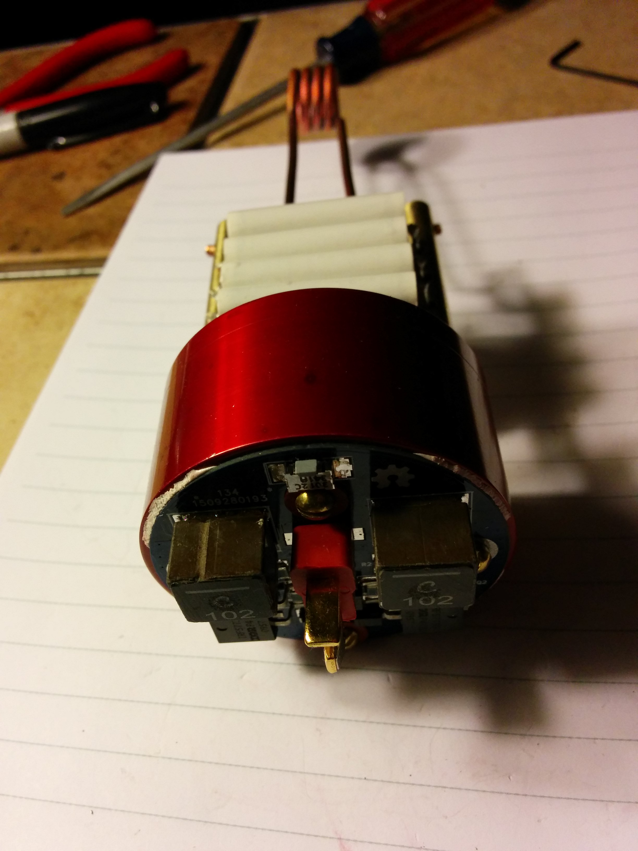
images/IMG_20160608_071202.jpg
