hardboiledfrog/smt-zvs-driver/images/IMG_20160608_071309.jpg

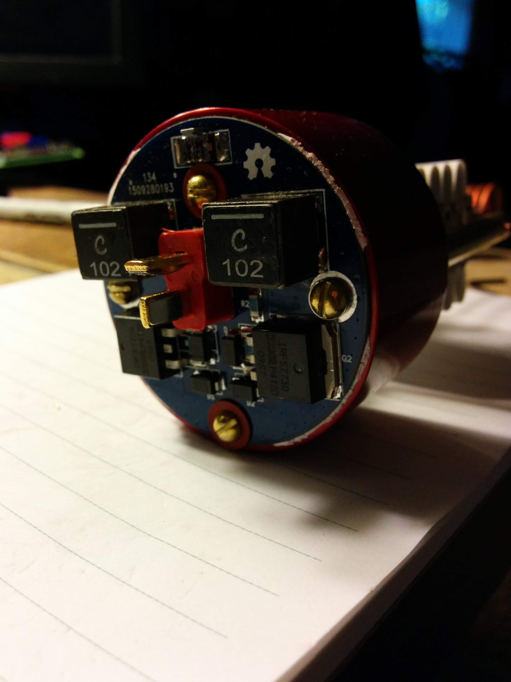
images/IMG_20160608_071309.jpg
