hardboiledfrog/smt-zvs-driver/images/IMG_20160608_071329.jpg

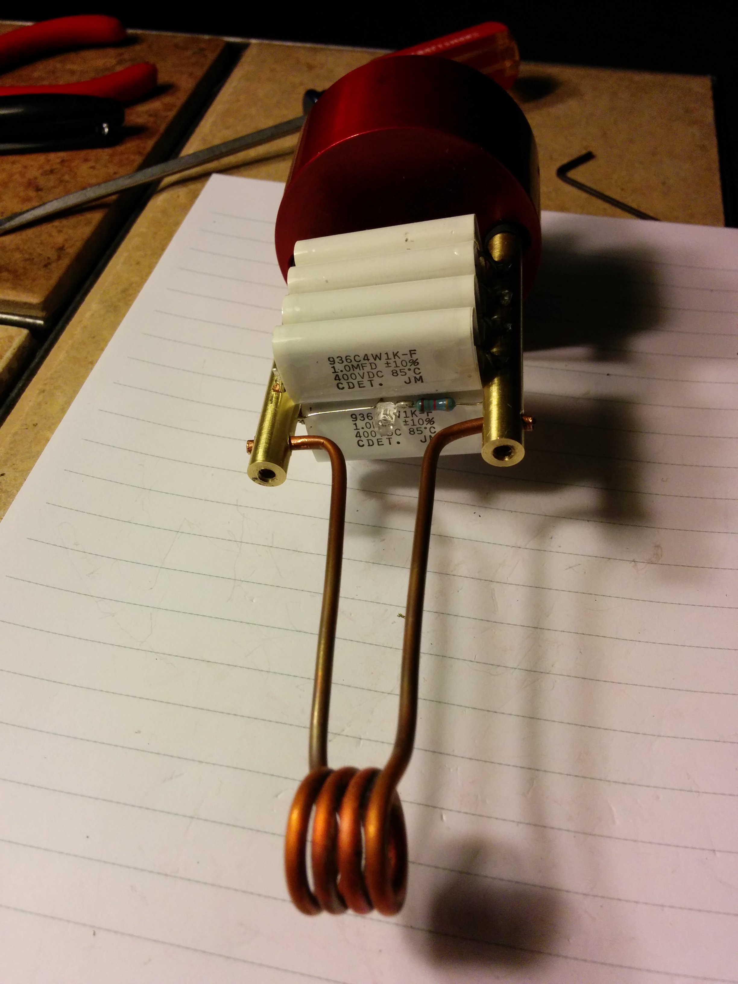
images/IMG_20160608_071329.jpg
