hardboiledfrog/smt-zvs-driver/images/IMG_20160608_071341.jpg

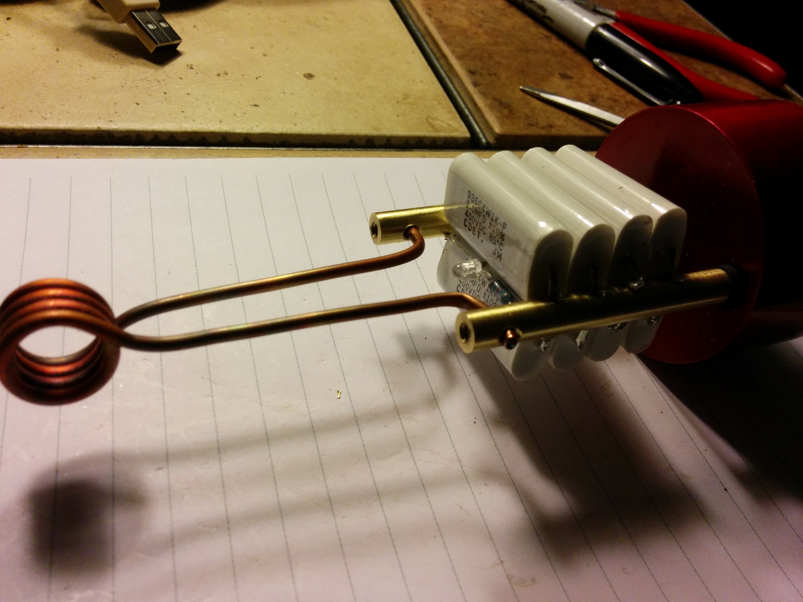
images/IMG_20160608_071341.jpg
