hardboiledfrog/smt-zvs-driver/images/IMG_20160608_114203.jpg

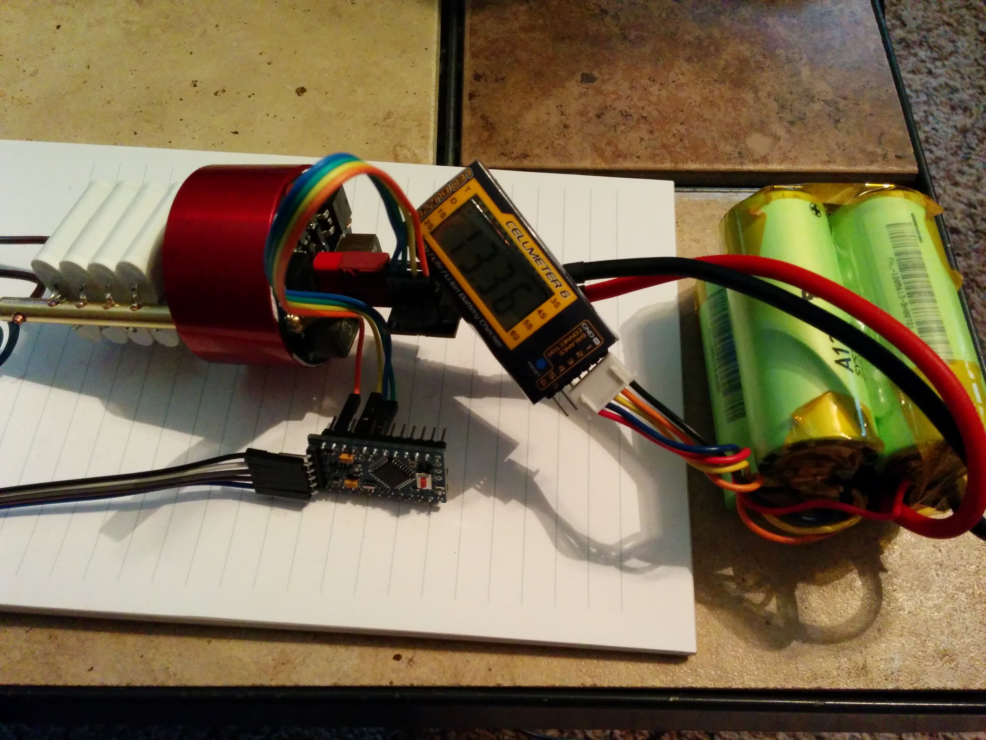
images/IMG_20160608_114203.jpg
