hardboiledfrog/smt-zvs-driver/images/IMG_20160608_114217.jpg

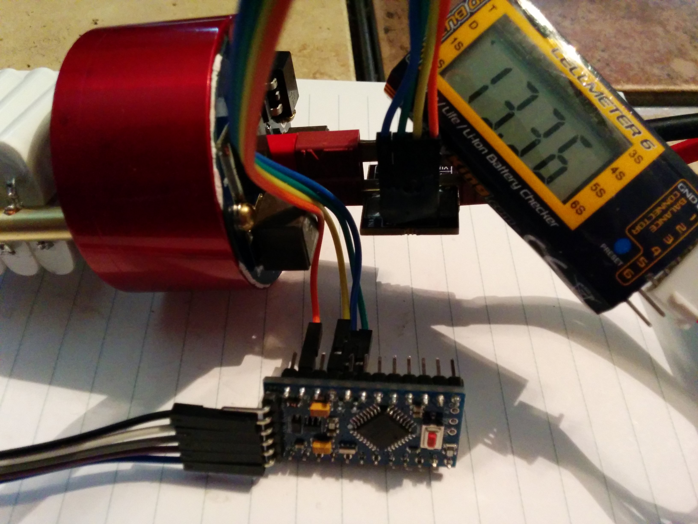
images/IMG_20160608_114217.jpg
