hardboiledfrog/smt-zvs-driver/images/IMG_20160608_114258.jpg

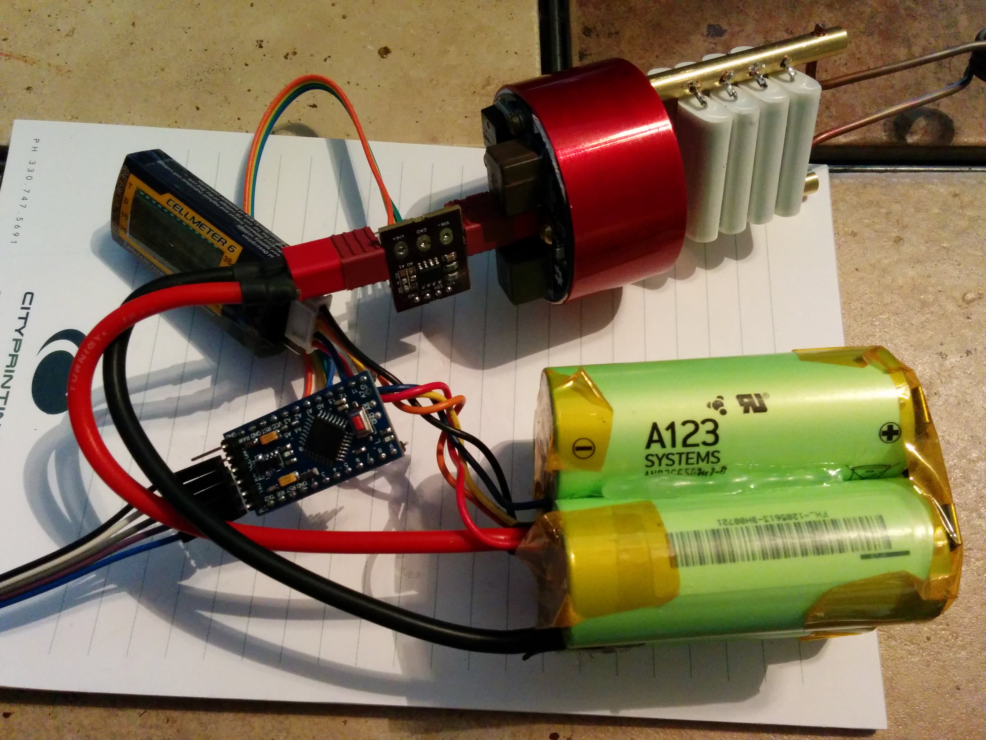
images/IMG_20160608_114258.jpg
