hardboiledfrog/smt-zvs-driver/images/IMG_20160608_134835.jpg

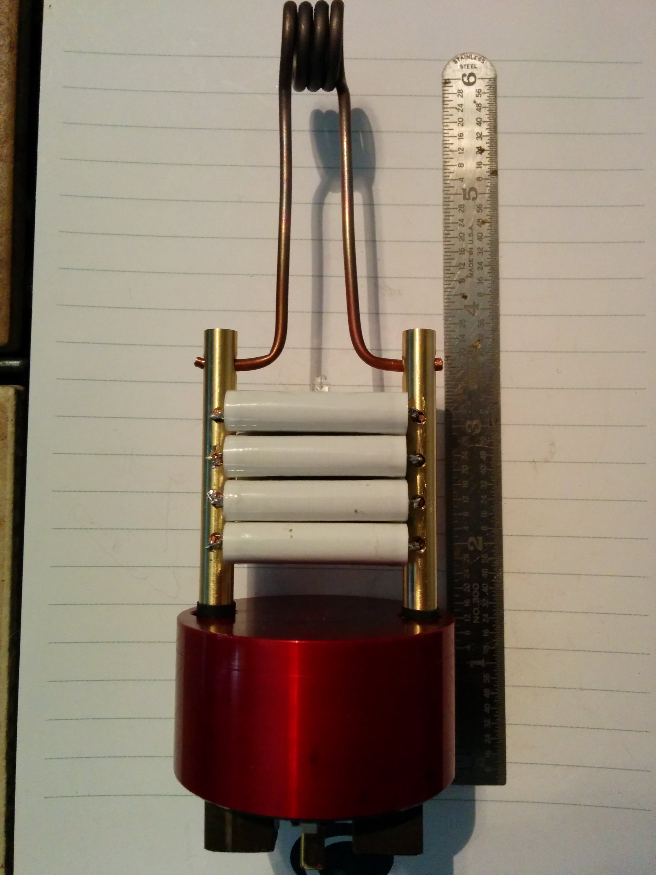
images/IMG_20160608_134835.jpg
