hardboiledfrog/smt-zvs-driver/images/IMG_20160608_134850.jpg

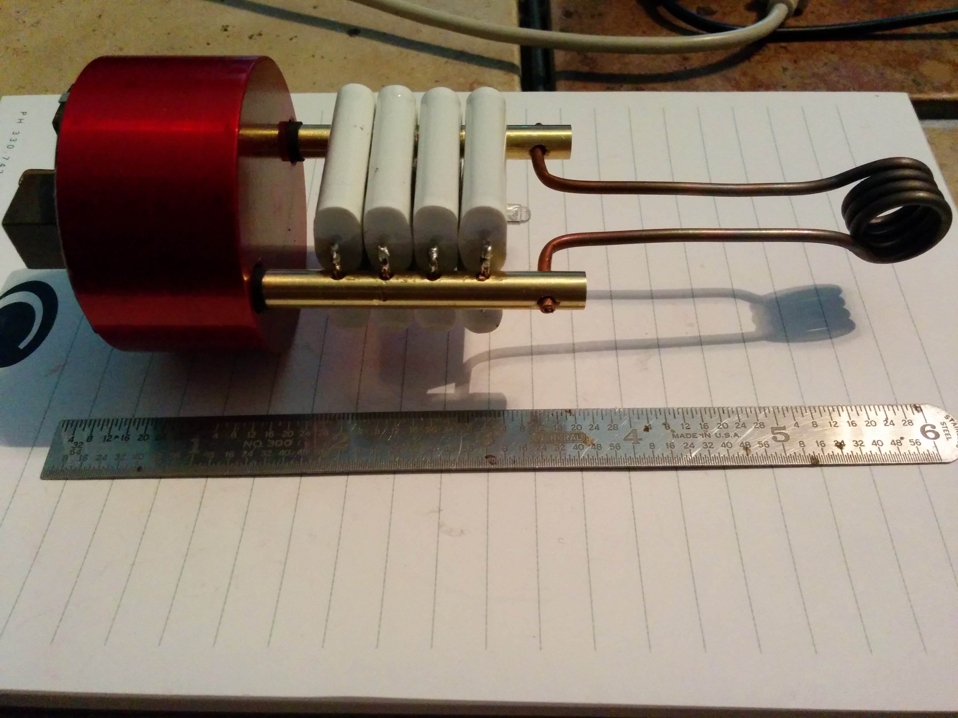
images/IMG_20160608_134850.jpg
