hardboiledfrog/smt-zvs-driver/images/IMG_20160611_121806.jpg

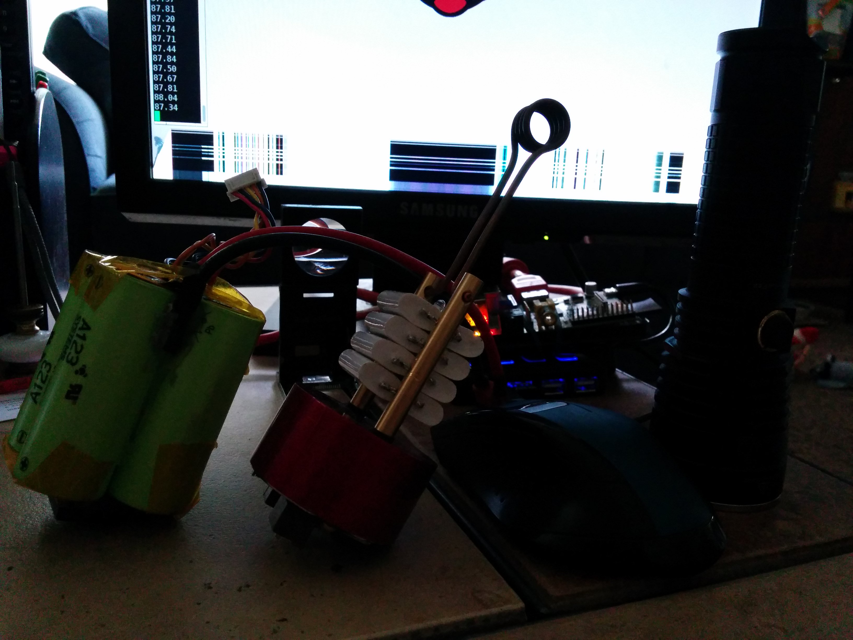
images/IMG_20160611_121806.jpg
