hardboiledfrog/smt-zvs-driver/images/IMG_20160611_121838.jpg

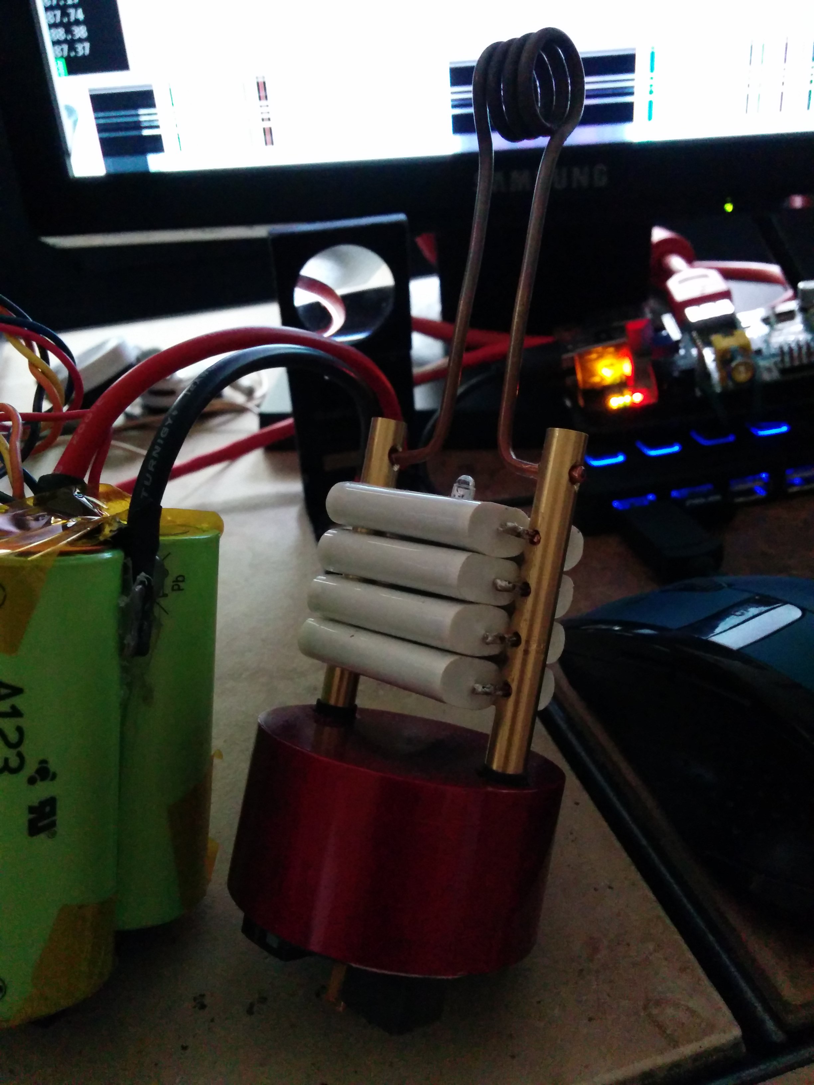
images/IMG_20160611_121838.jpg
