hardboiledfrog/smt-zvs-driver/images/IMG_20160611_121919.jpg

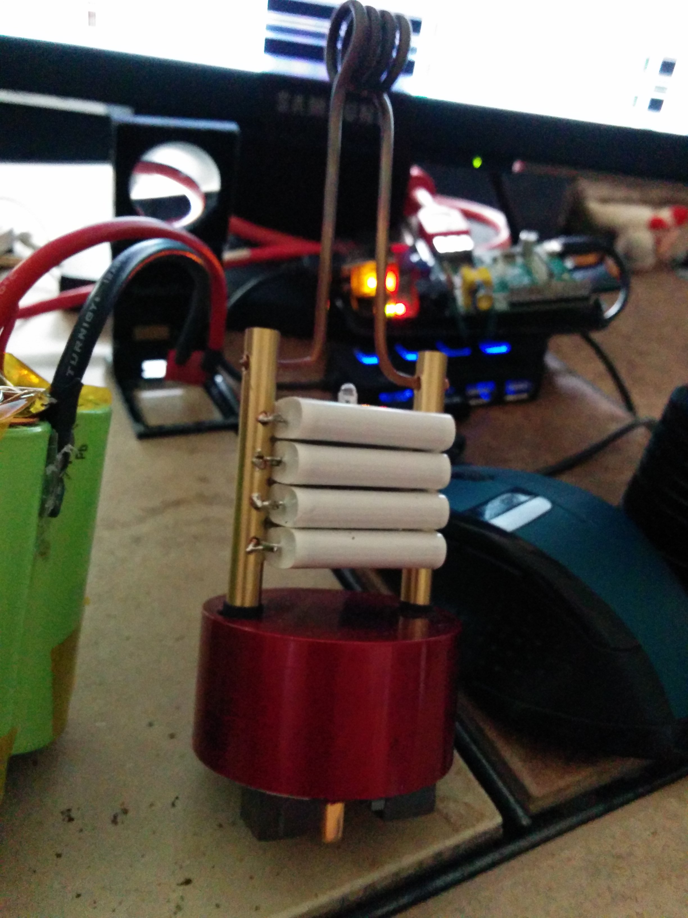
images/IMG_20160611_121919.jpg
