hardboiledfrog/smt-zvs-driver/images/IMG_20160611_121940.jpg

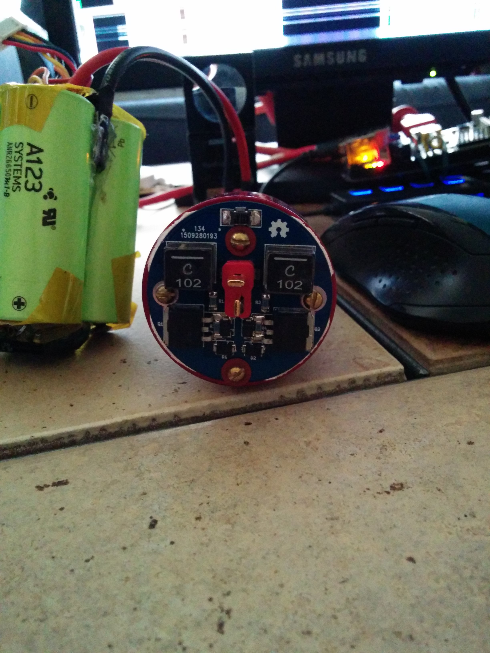
images/IMG_20160611_121940.jpg
