hardboiledfrog/smt-zvs-driver/images/IMG_20160611_121948.jpg

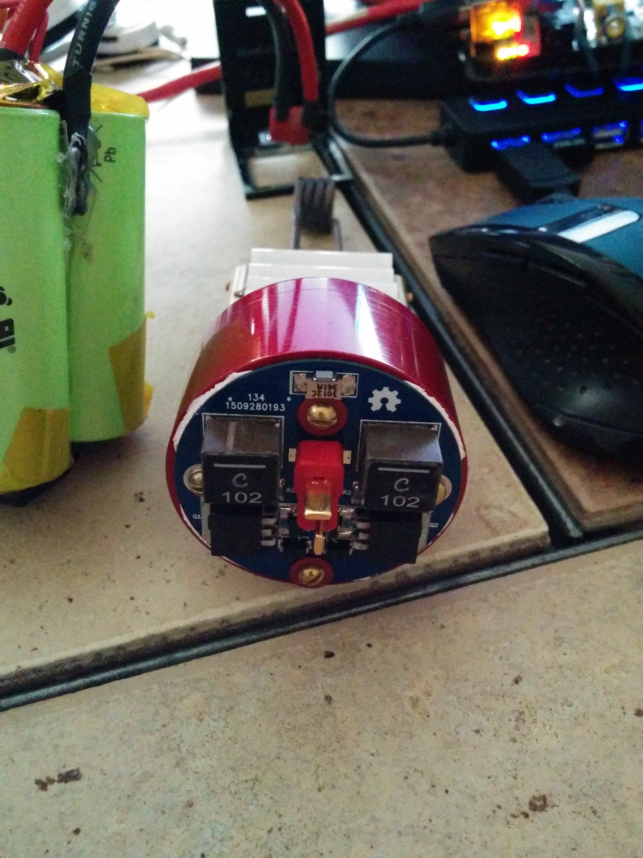
images/IMG_20160611_121948.jpg
