hardboiledfrog/smt-zvs-driver/images/P1020117.JPG

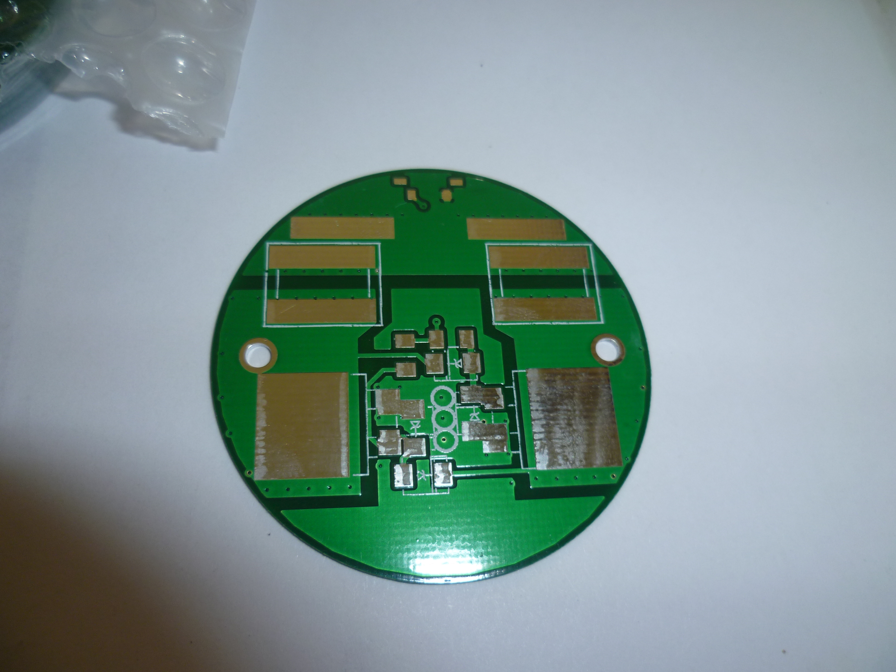
images/P1020117.JPG
