hardboiledfrog/smt-zvs-driver/images/P1020118.JPG

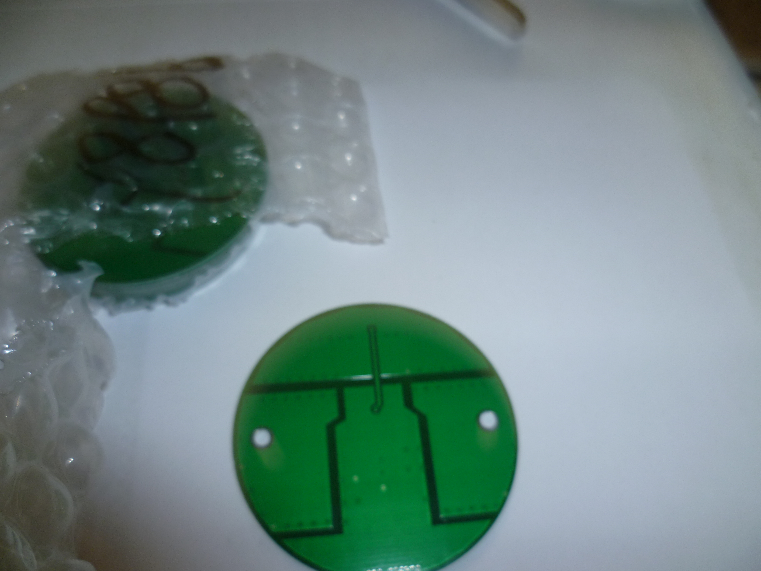
images/P1020118.JPG
