hardboiledfrog/smt-zvs-driver/images/P1020119.JPG

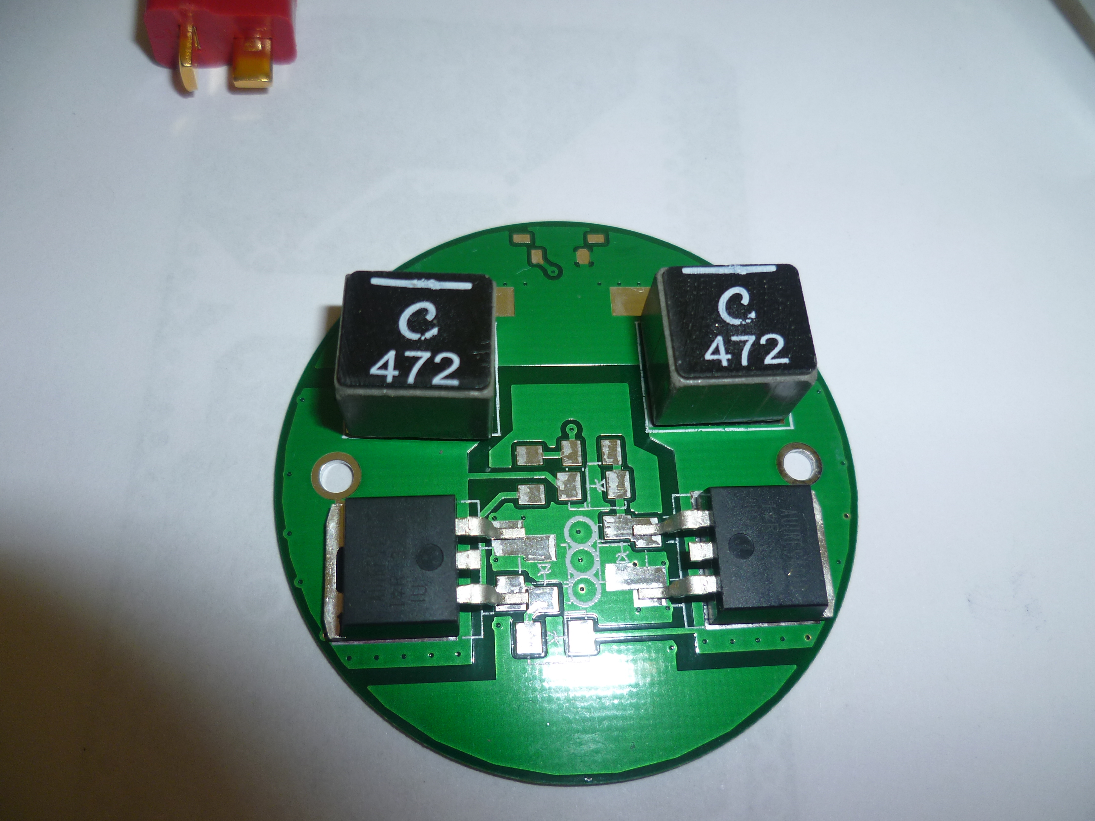
images/P1020119.JPG
