hardboiledfrog/smt-zvs-driver/images/P1020120.JPG

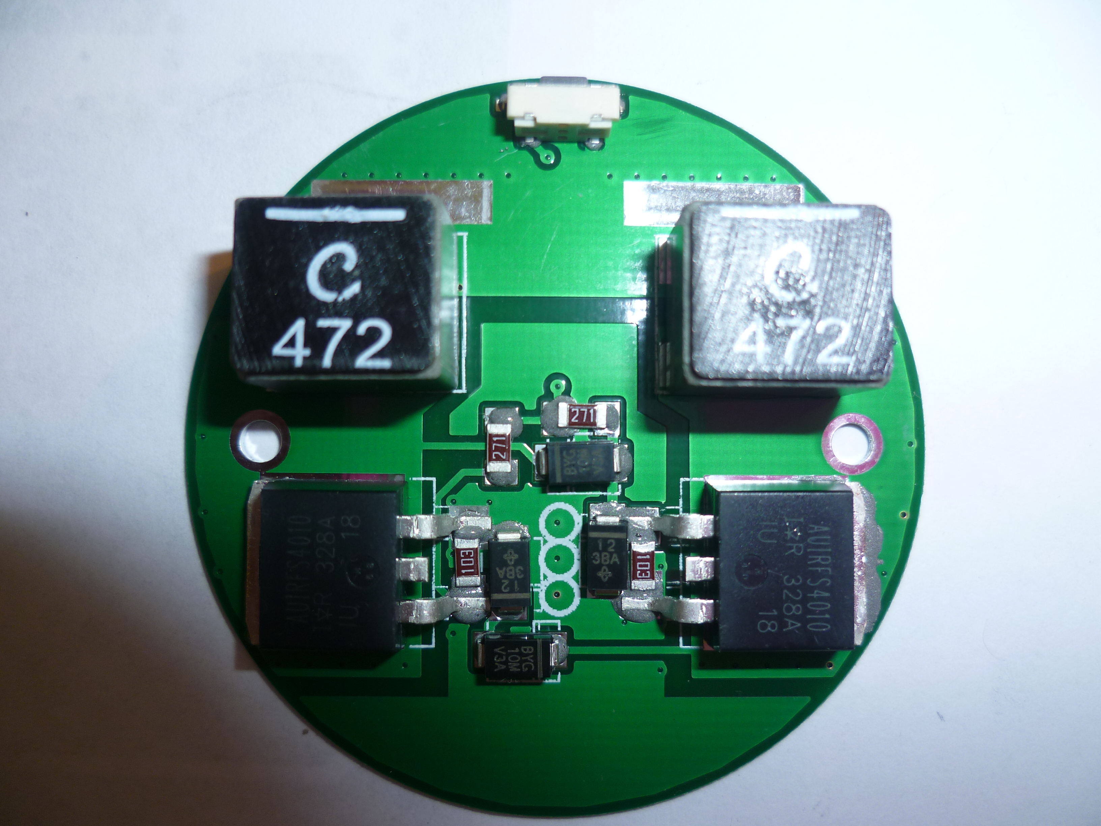
images/P1020120.JPG
