hardboiledfrog/smt-zvs-driver/images/P1020121.JPG

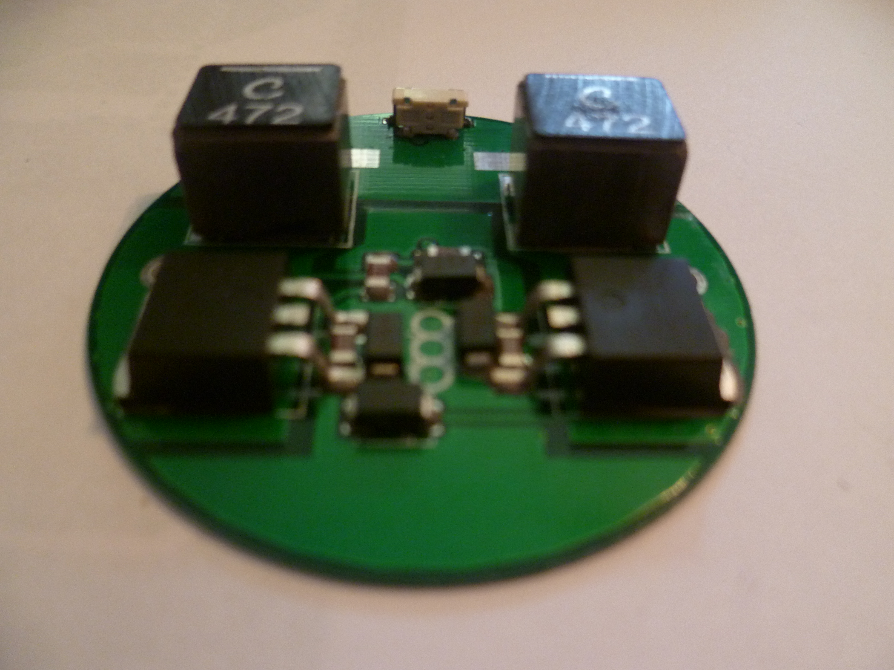
images/P1020121.JPG
