hardboiledfrog/smt-zvs-driver/images/P1020122.JPG

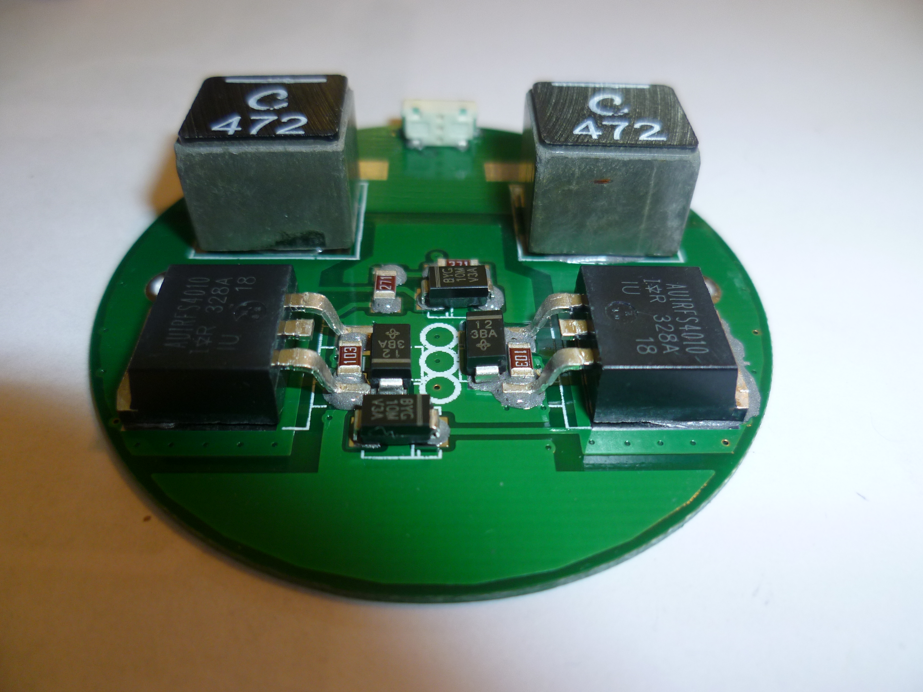
images/P1020122.JPG
