hardboiledfrog/smt-zvs-driver/images/P1020123.JPG

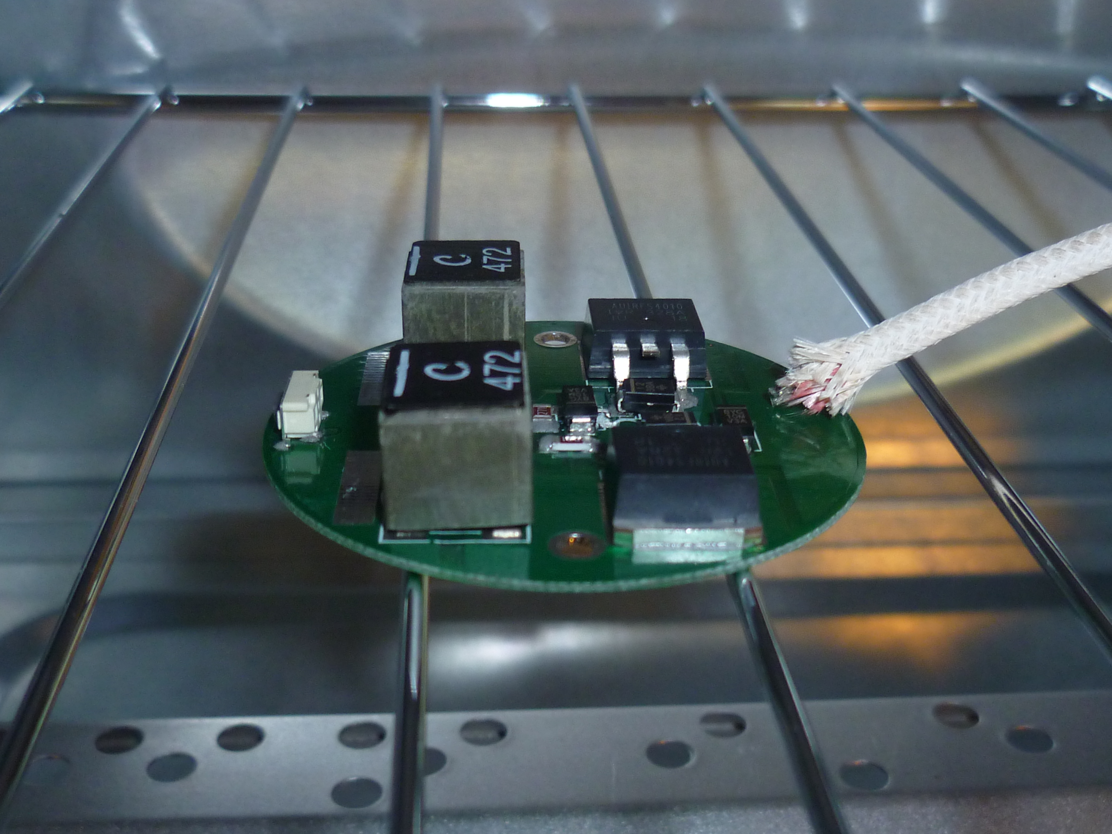
images/P1020123.JPG
