hardboiledfrog/smt-zvs-driver/images/P1020124.JPG

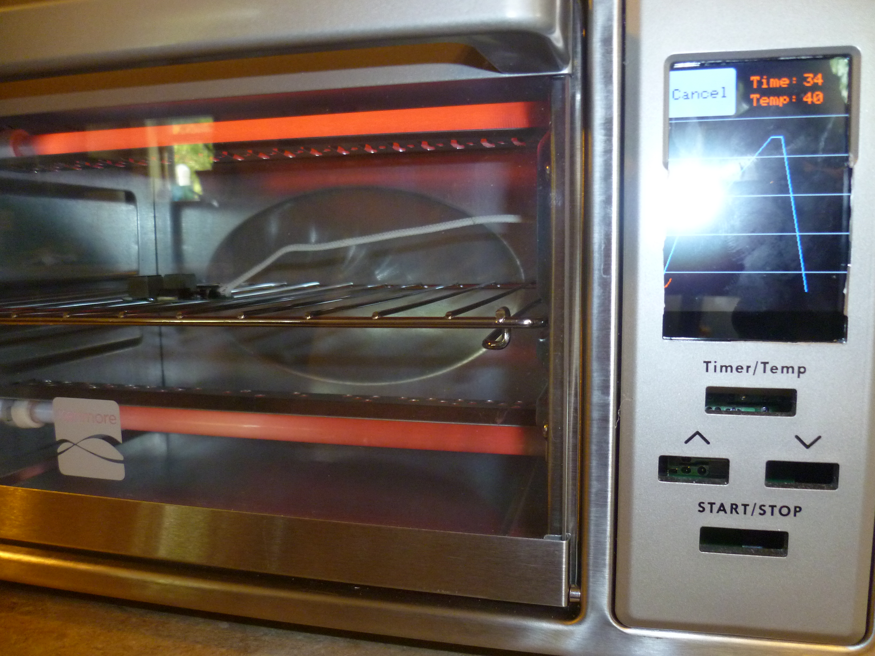
images/P1020124.JPG
