hardboiledfrog/smt-zvs-driver/images/P1020125.JPG

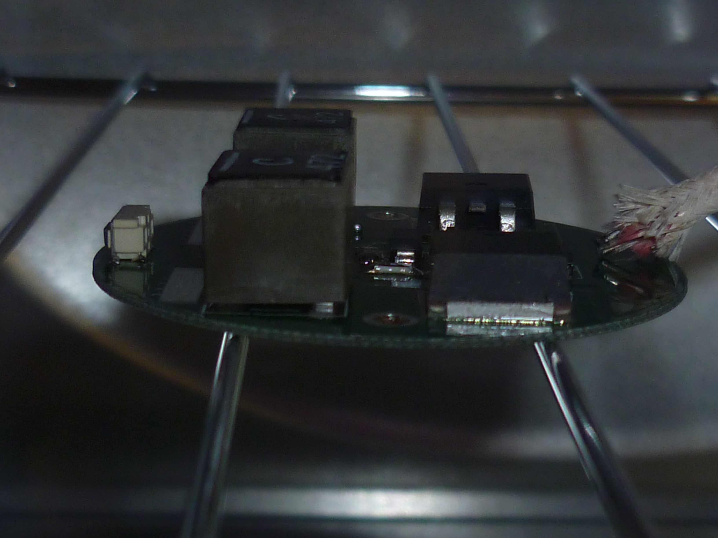
images/P1020125.JPG
