hardboiledfrog/smt-zvs-driver/images/P1020126.JPG

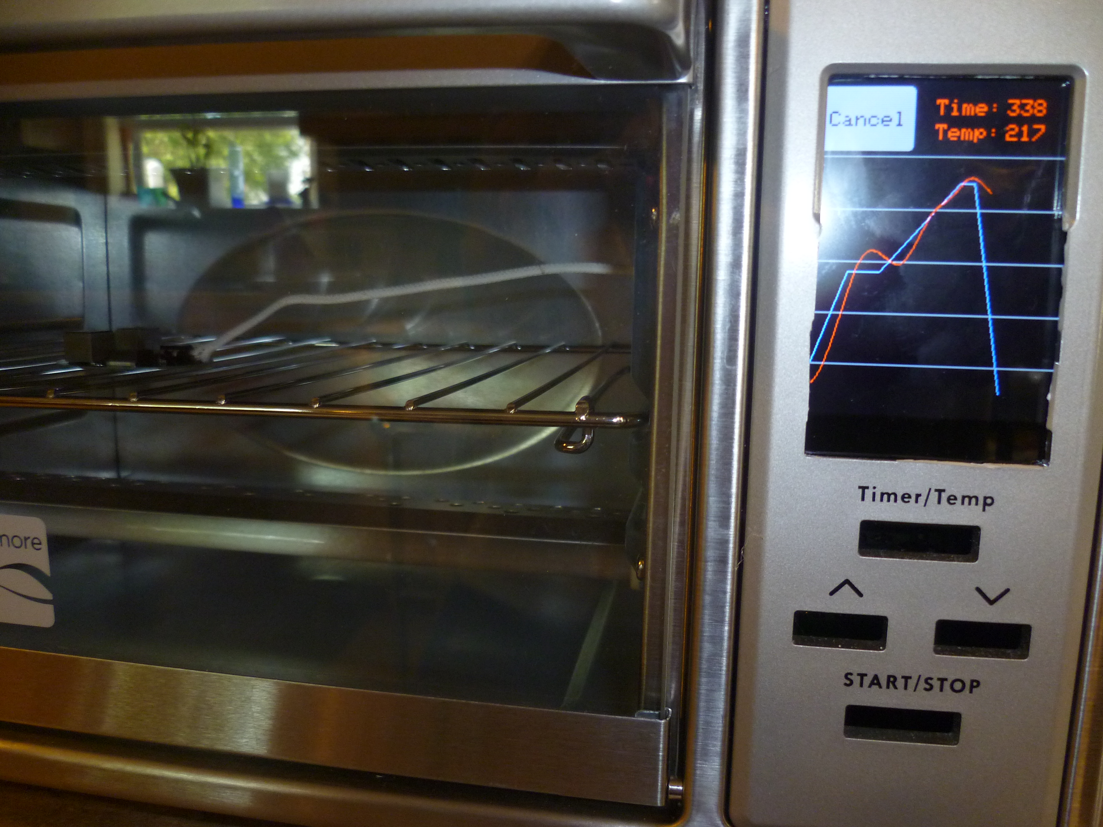
images/P1020126.JPG
