hardboiledfrog/smt-zvs-driver/images/P1020127.JPG

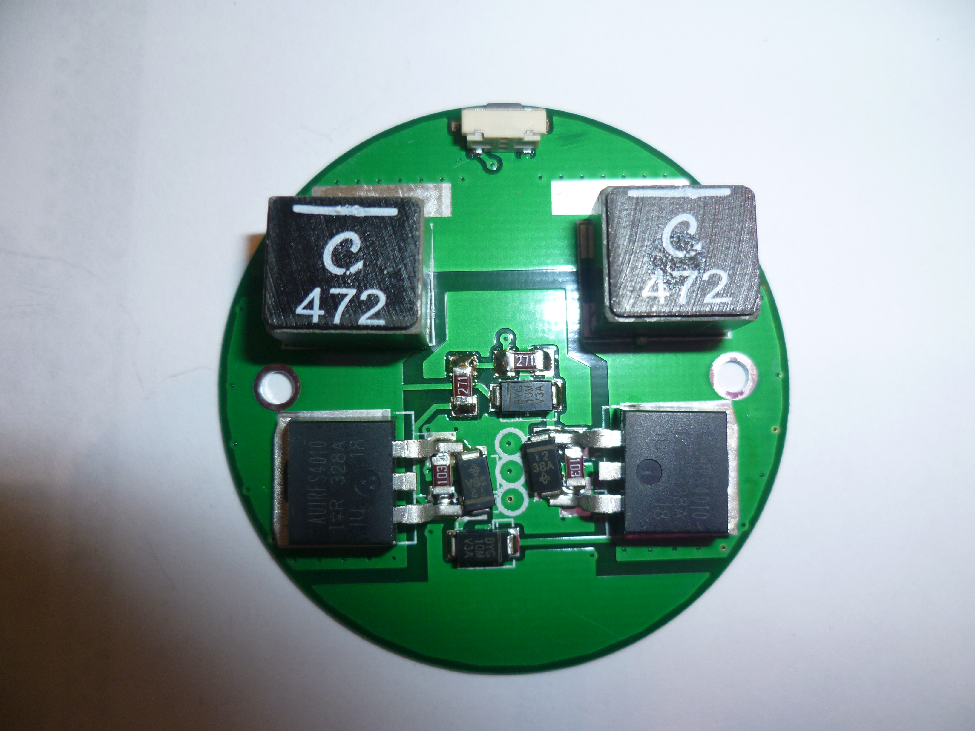
images/P1020127.JPG
