hardboiledfrog/smt-zvs-driver/images/P1020128.JPG

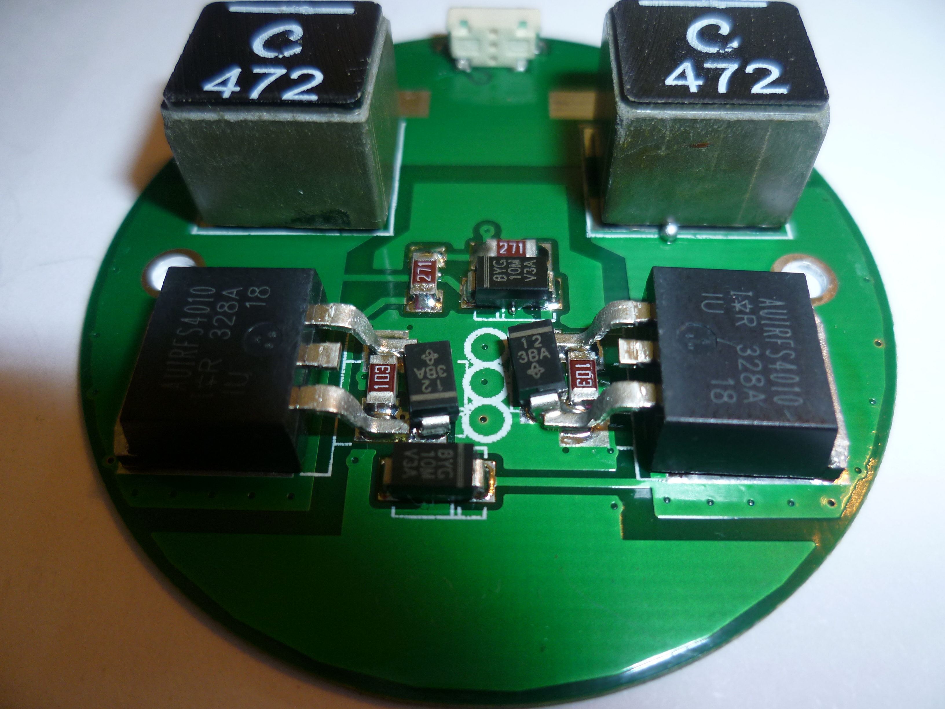
images/P1020128.JPG
