hardboiledfrog/smt-zvs-driver/images/P1020129.JPG

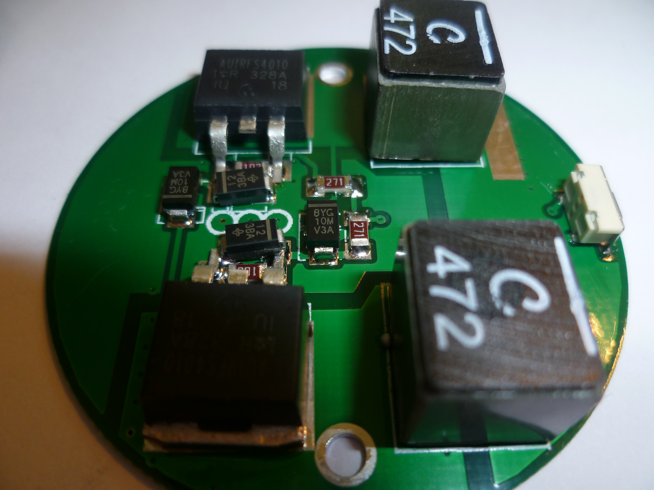
images/P1020129.JPG
