hardboiledfrog/smt-zvs-driver/images/P1020130.JPG

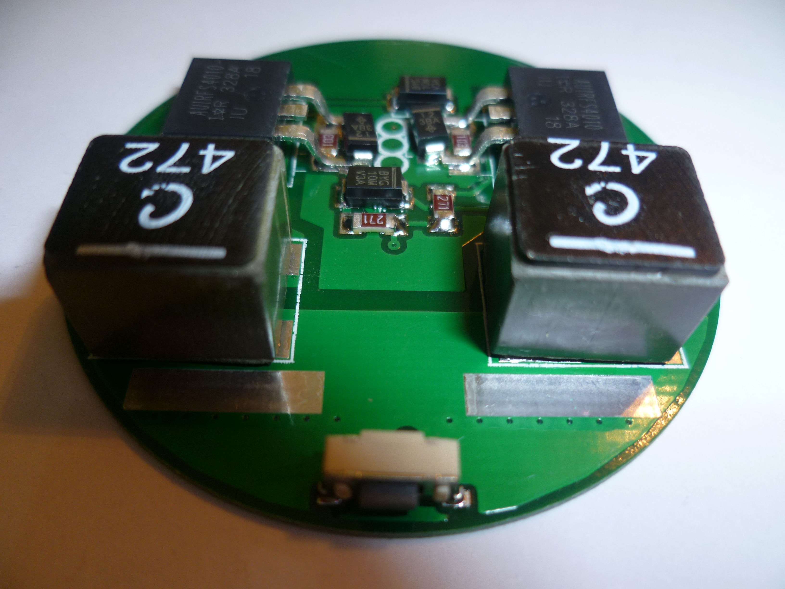
images/P1020130.JPG
