hardboiledfrog/smt-zvs-driver/images/P1020131.JPG

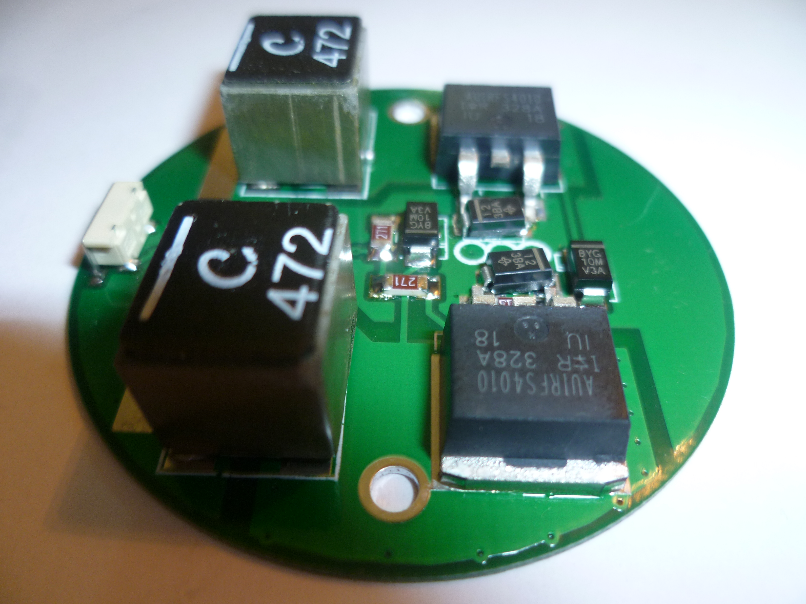
images/P1020131.JPG
