hardboiledfrog/smt-zvs-driver/images/P1020132.JPG

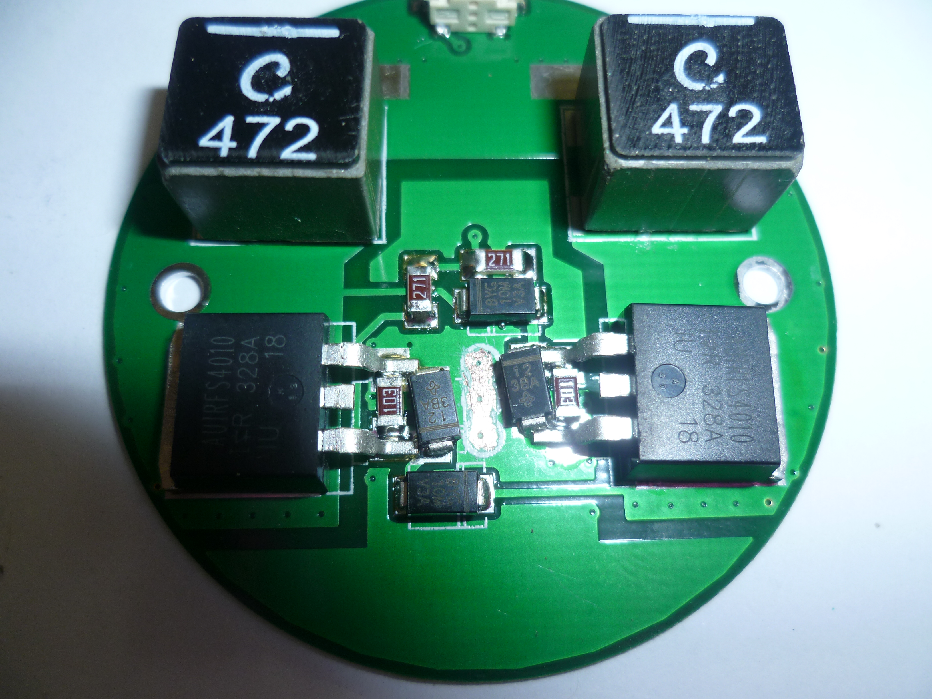
images/P1020132.JPG
