hardboiledfrog/smt-zvs-driver/images/P1020133.JPG

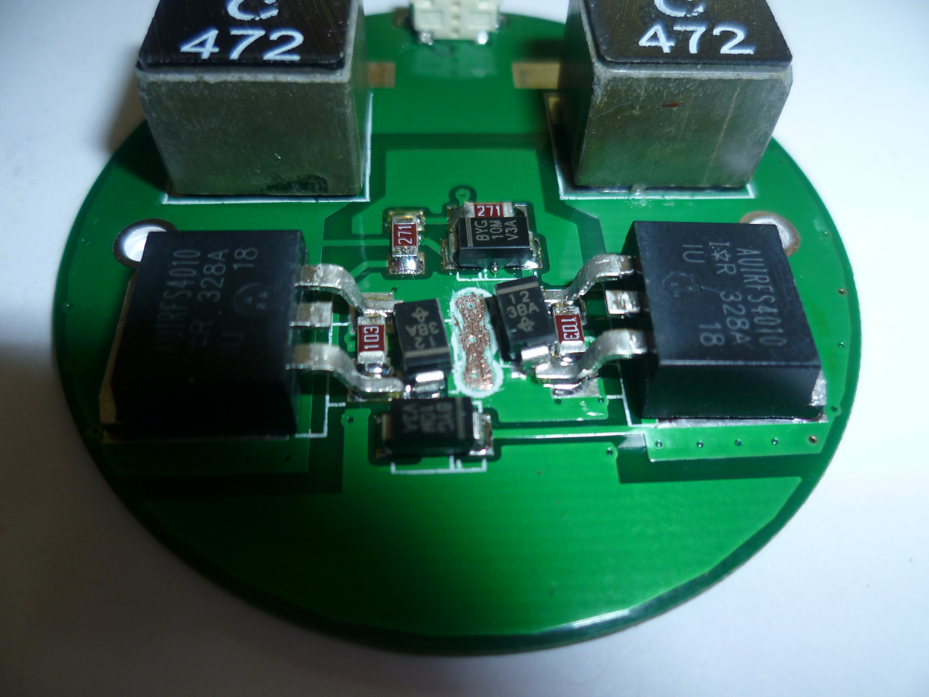
images/P1020133.JPG
