hardboiledfrog/smt-zvs-driver/images/P1020662.JPG

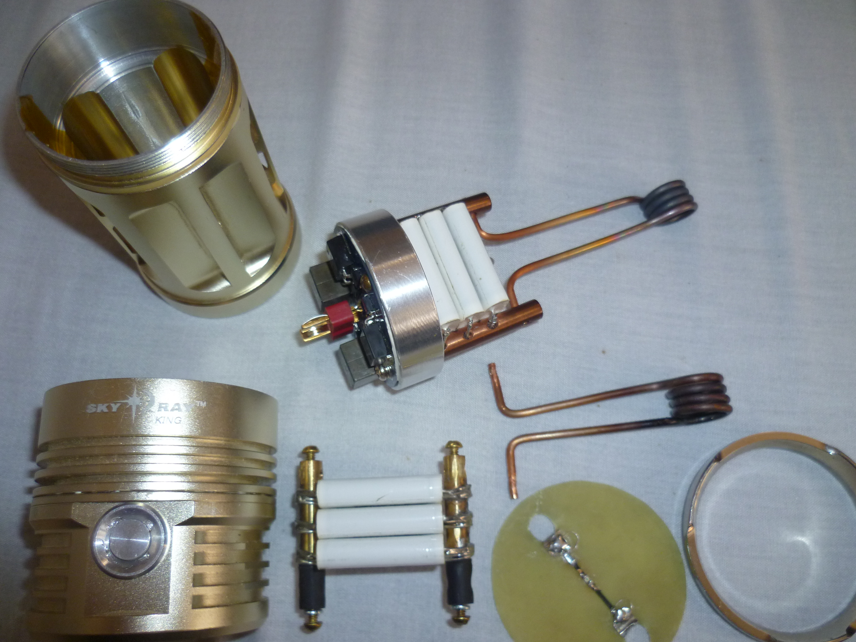
images/P1020662.JPG
