hardboiledfrog/smt-zvs-driver/images/P1020663.JPG

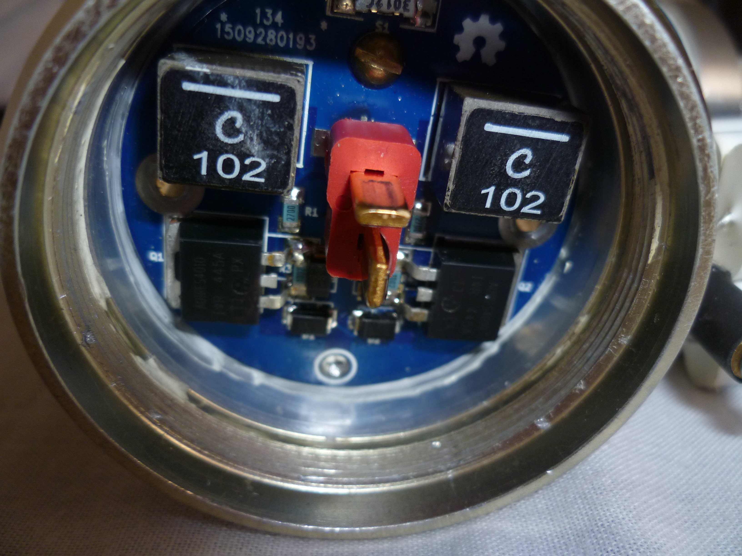
images/P1020663.JPG
