hardboiledfrog/smt-zvs-driver/images/P1020664.JPG

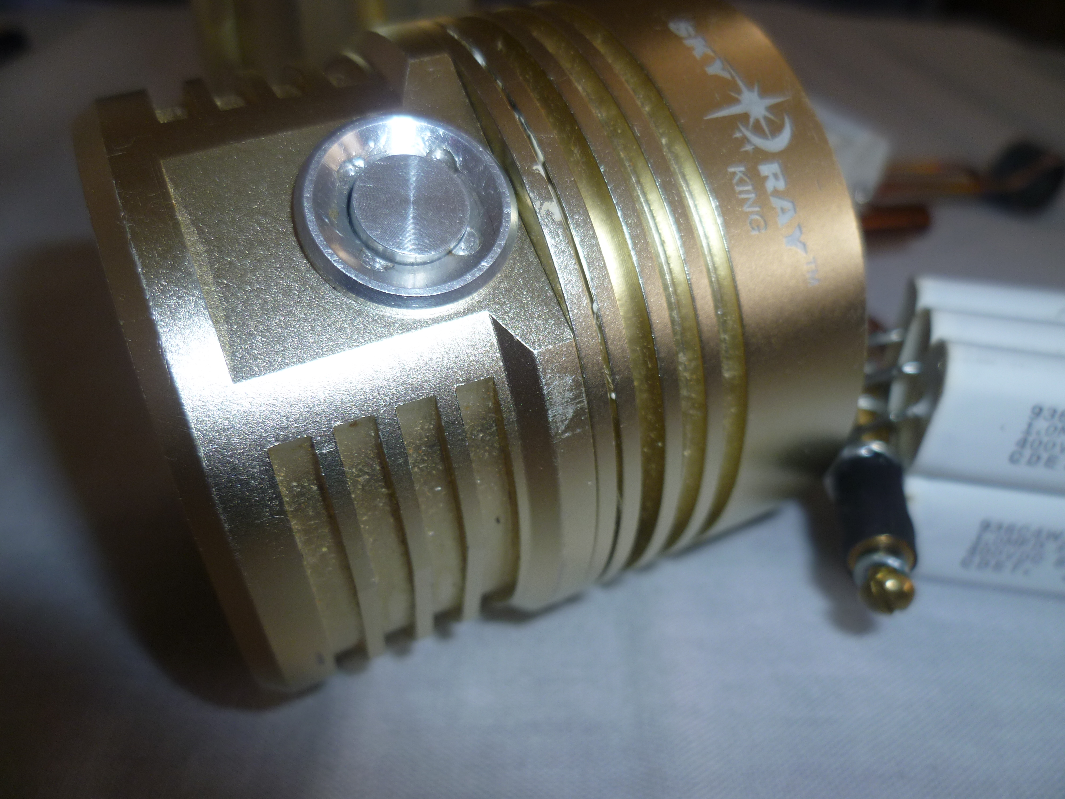
images/P1020664.JPG
