hardboiledfrog/smt-zvs-driver/images/P1020665.JPG

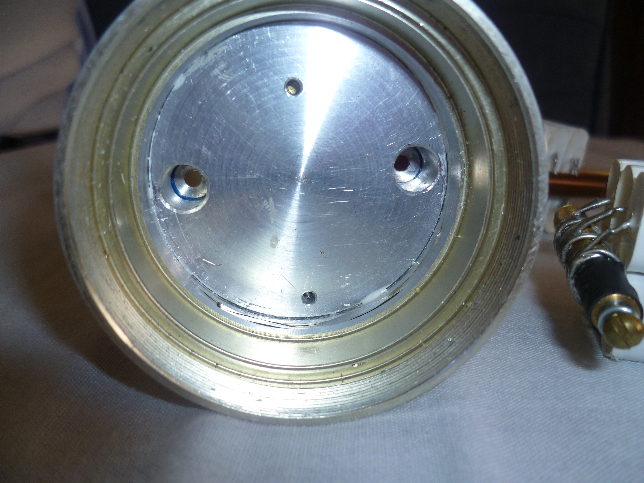
images/P1020665.JPG
