hardboiledfrog/smt-zvs-driver/images/P1020666.JPG

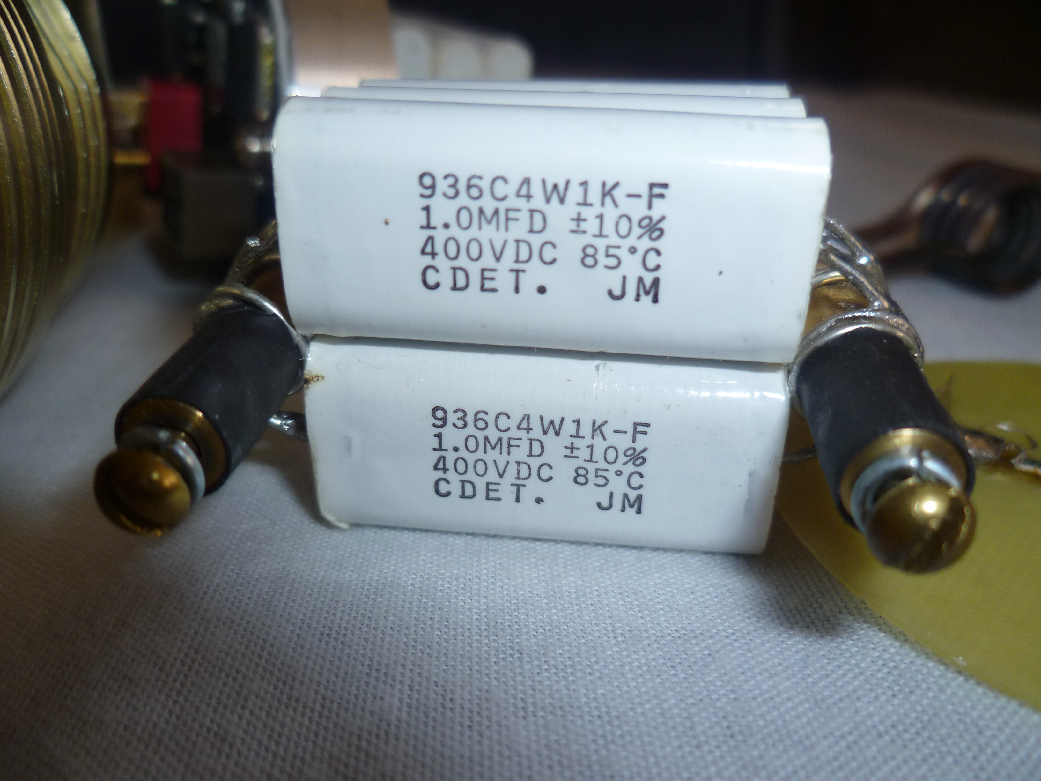
images/P1020666.JPG
