hardboiledfrog/smt-zvs-driver/images/P1020667.JPG

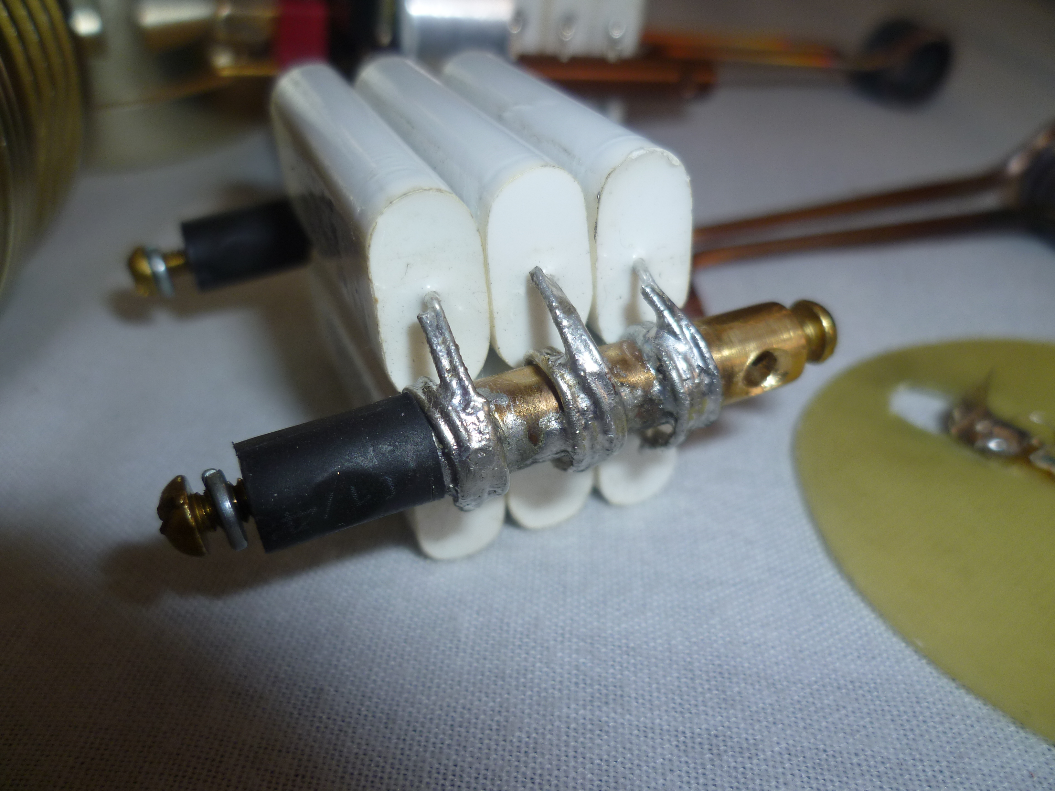
images/P1020667.JPG
