hardboiledfrog/smt-zvs-driver/images/P1020668.JPG

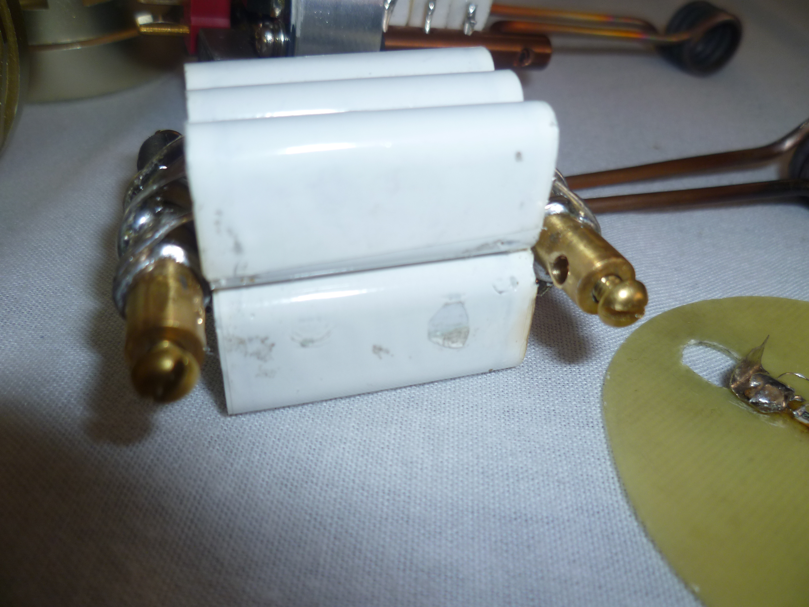
images/P1020668.JPG
