hardboiledfrog/smt-zvs-driver/images/P1020669.JPG

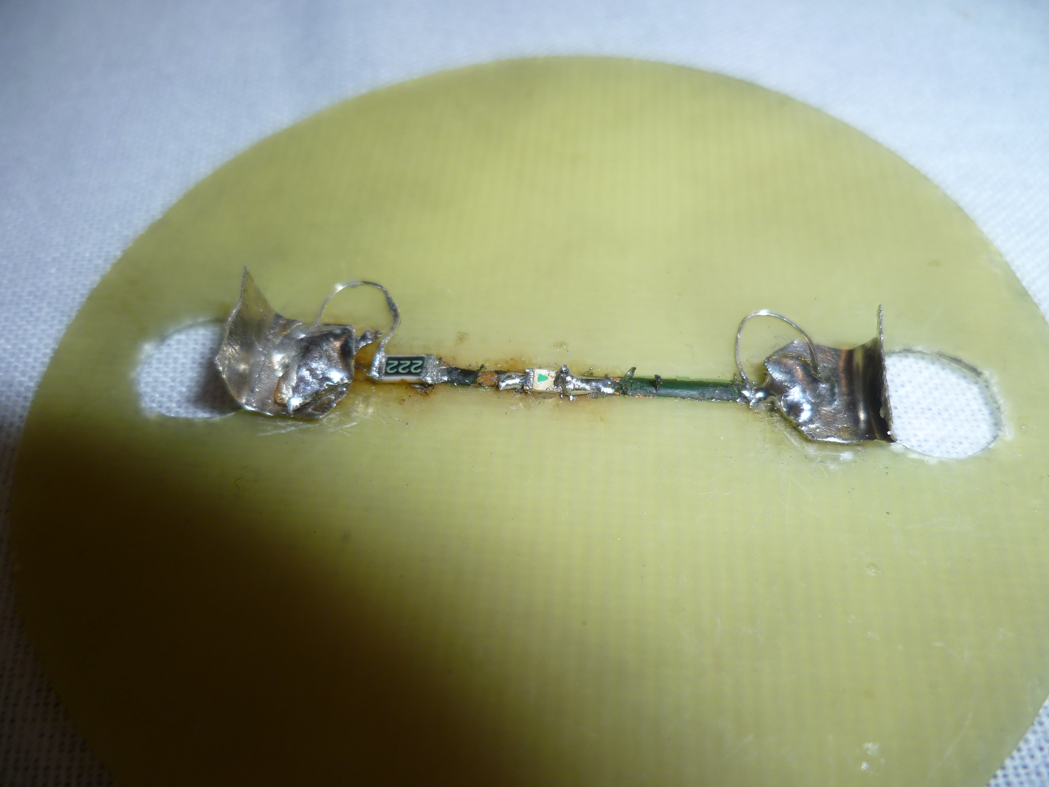
images/P1020669.JPG
