hardboiledfrog/smt-zvs-driver/images/P1020670.JPG

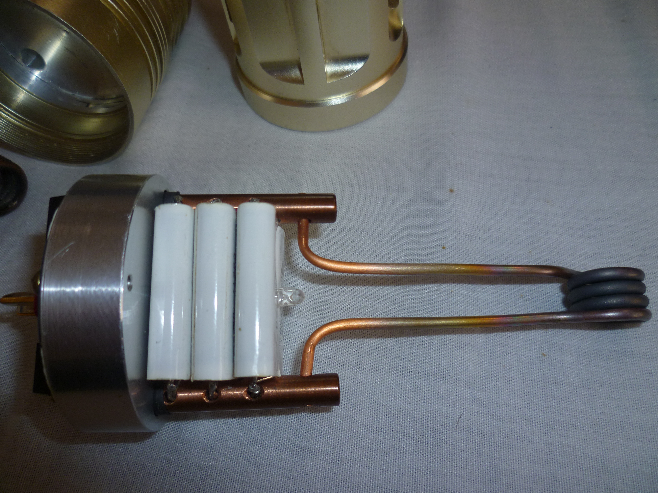
images/P1020670.JPG
