hardboiledfrog/smt-zvs-driver/images/P1020671.JPG

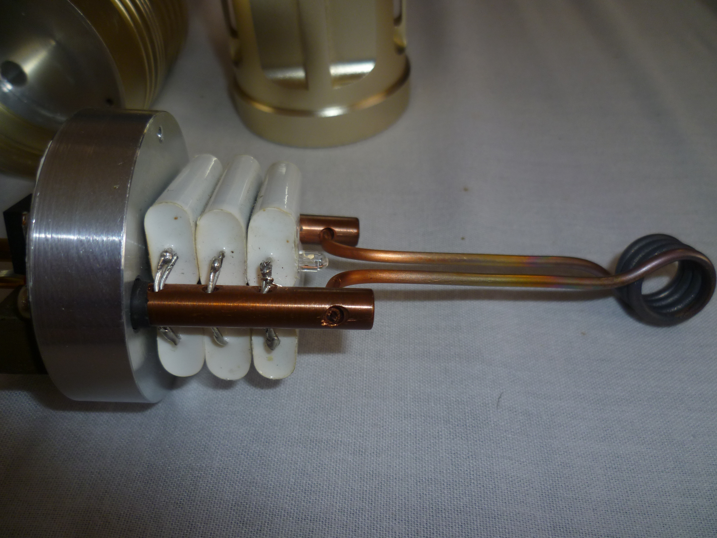
images/P1020671.JPG
