hardboiledfrog/smt-zvs-driver/images/P1020672.JPG

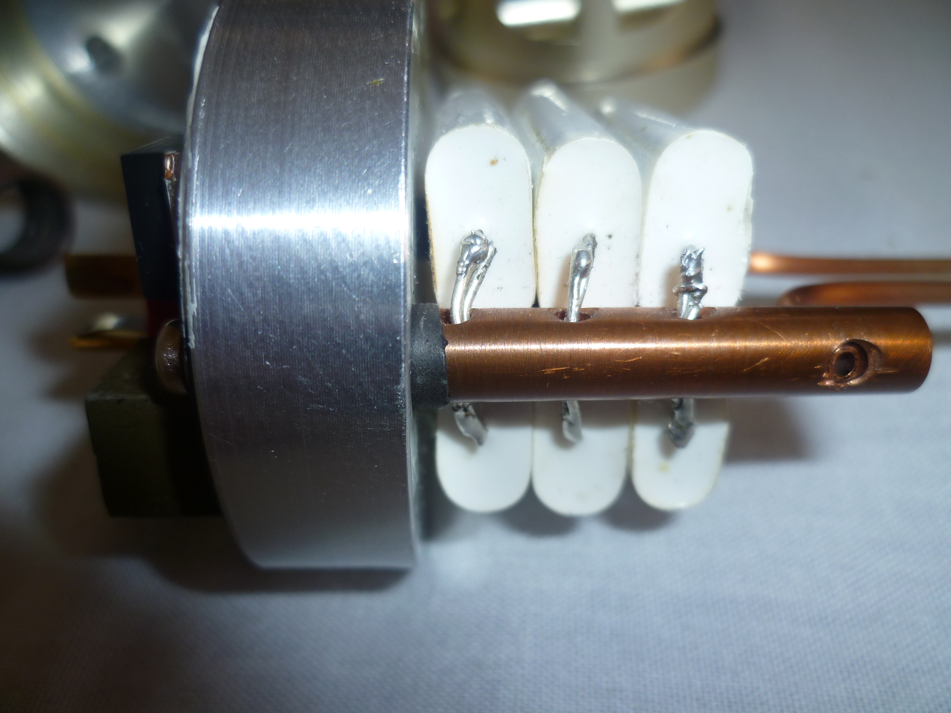
images/P1020672.JPG
