hardboiledfrog/smt-zvs-driver/images/P1020673.JPG

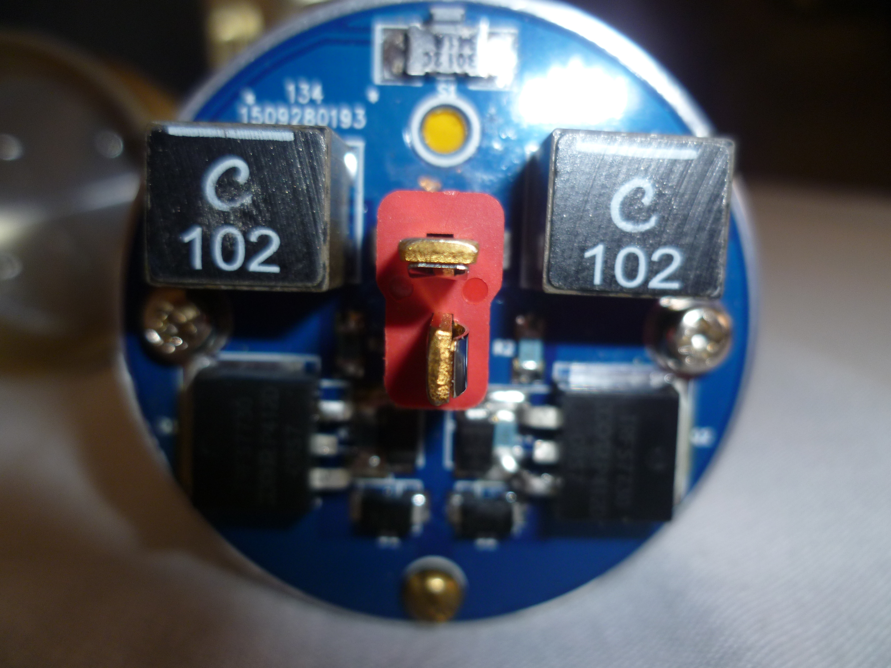
images/P1020673.JPG
