hardboiledfrog/smt-zvs-driver/images/P1020674.JPG

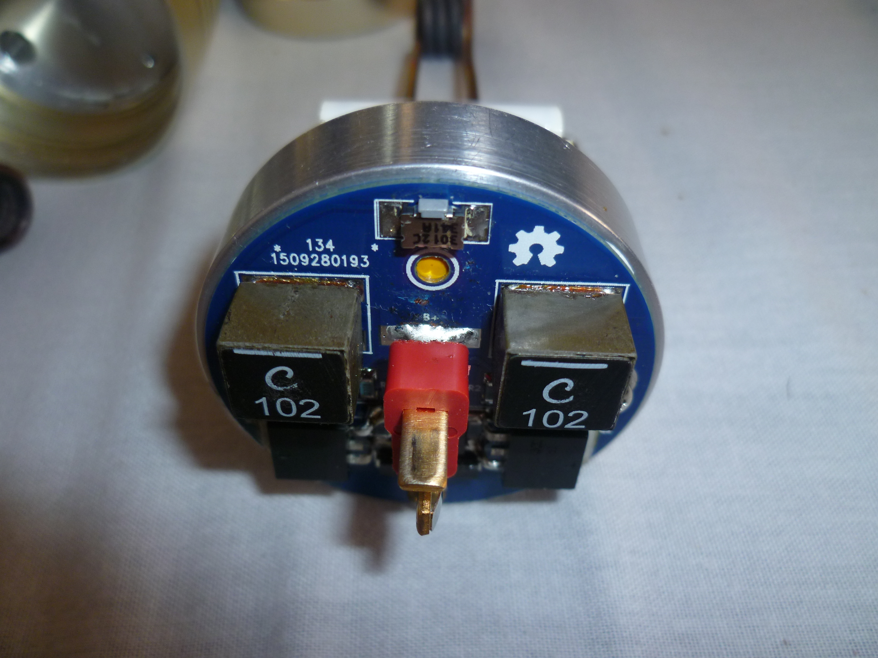
images/P1020674.JPG
