hardboiledfrog/smt-zvs-driver/images/P1020675.JPG

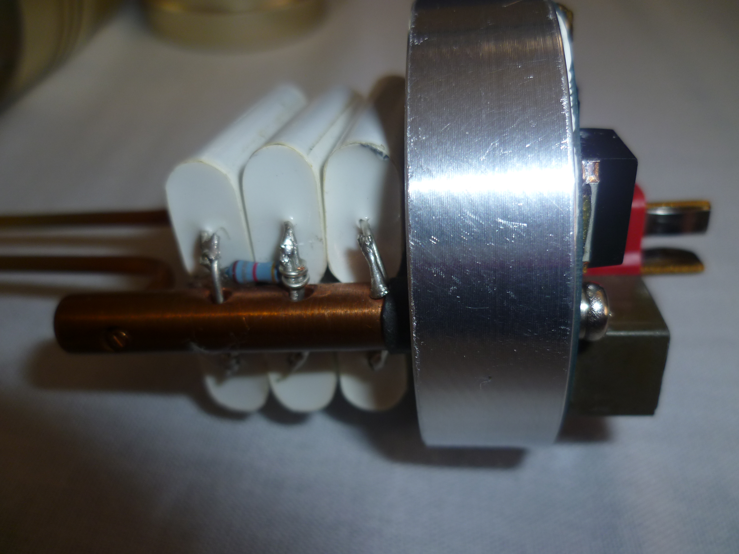
images/P1020675.JPG
