hardboiledfrog/smt-zvs-driver/images/P1020676.JPG

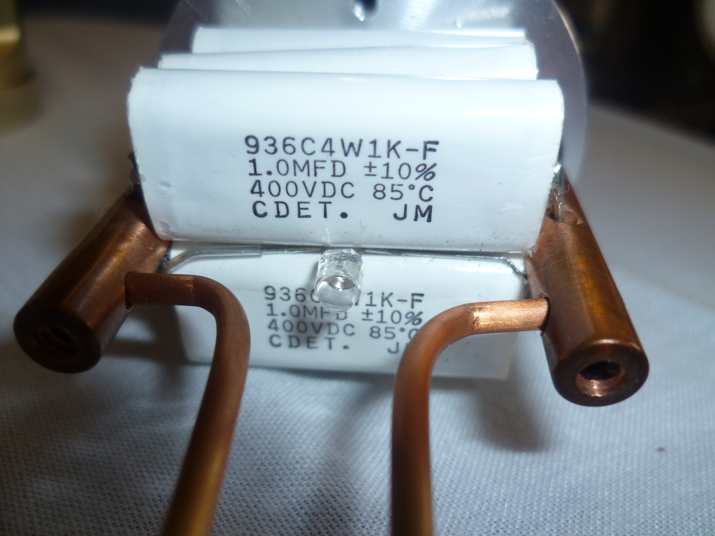
images/P1020676.JPG
