hardboiledfrog/smt-zvs-driver/images/P1020677.JPG

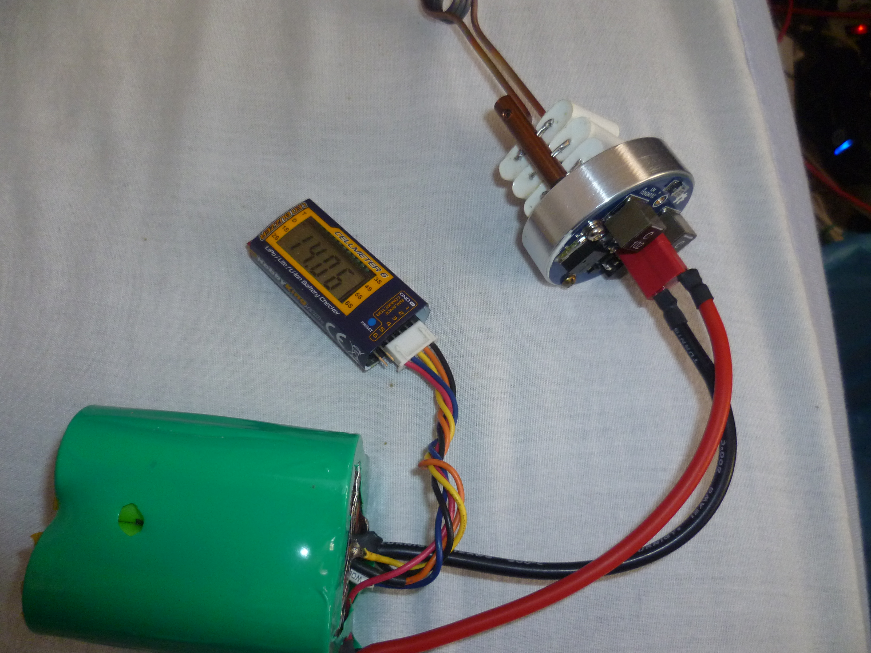
images/P1020677.JPG
