hardboiledfrog/smt-zvs-driver/images/P1020678.JPG

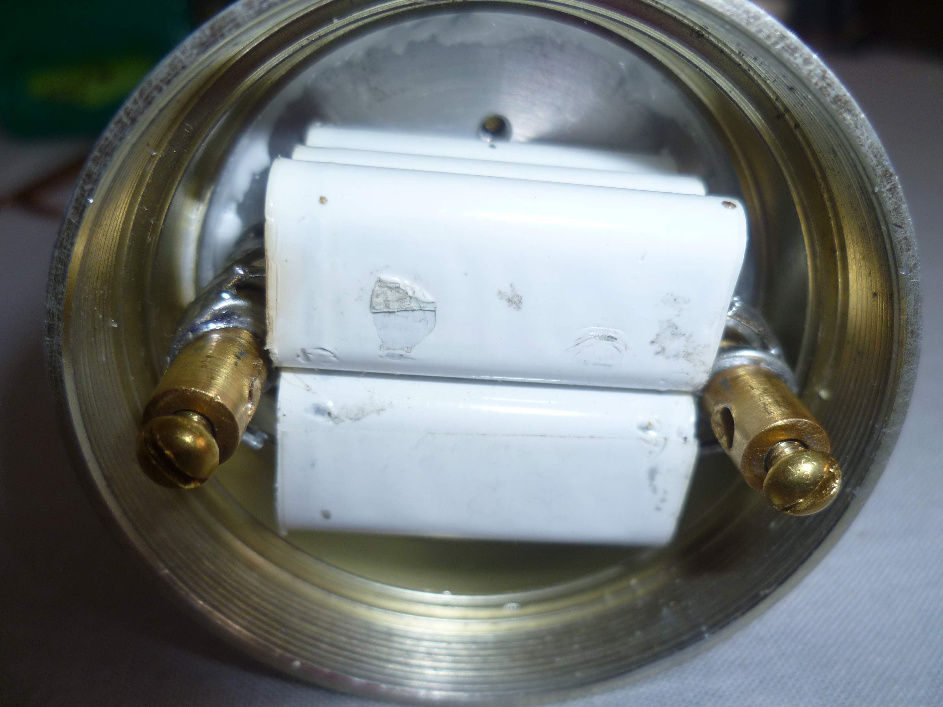
images/P1020678.JPG
