hardboiledfrog/smt-zvs-driver/images/P1020679.JPG

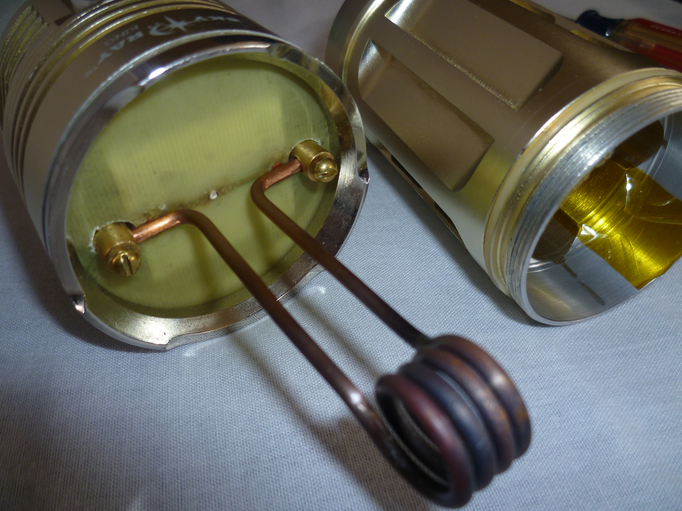
images/P1020679.JPG
