hardboiledfrog/smt-zvs-driver/images/P1020680.JPG

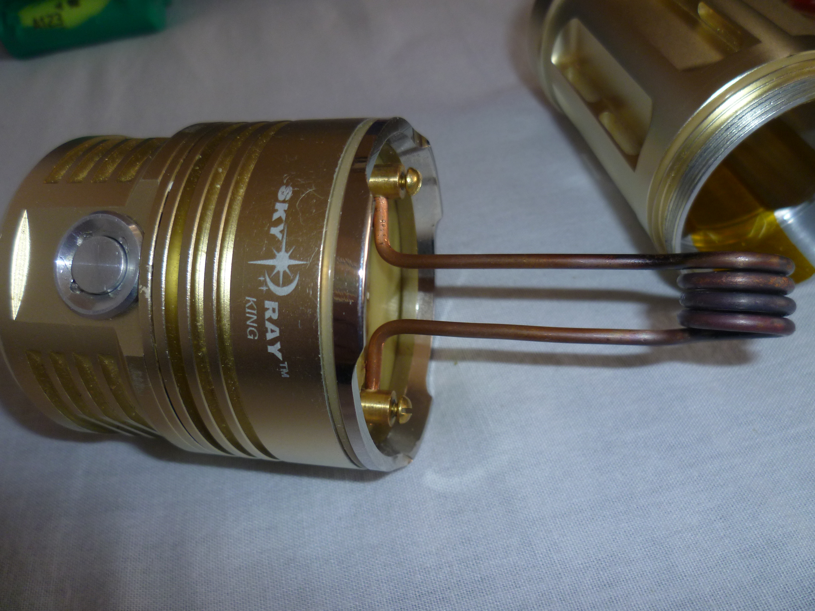
images/P1020680.JPG
