hardboiledfrog/smt-zvs-driver/images/P1020681.JPG

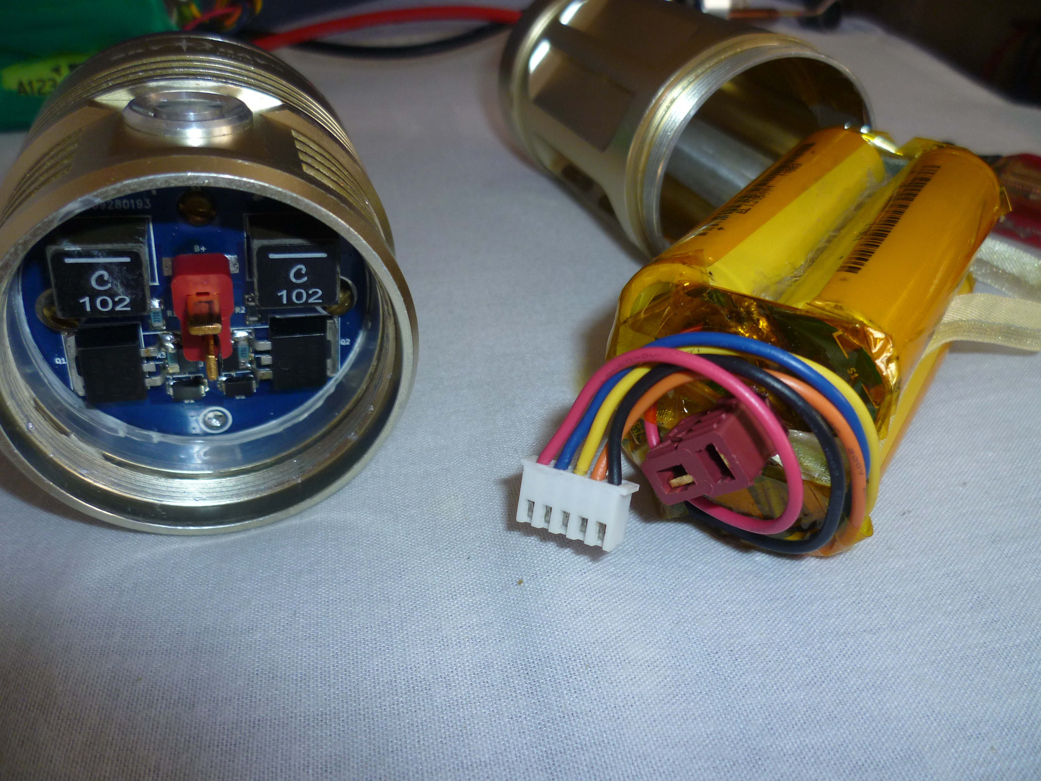
images/P1020681.JPG
