hardboiledfrog/smt-zvs-driver/images/P1020682.JPG

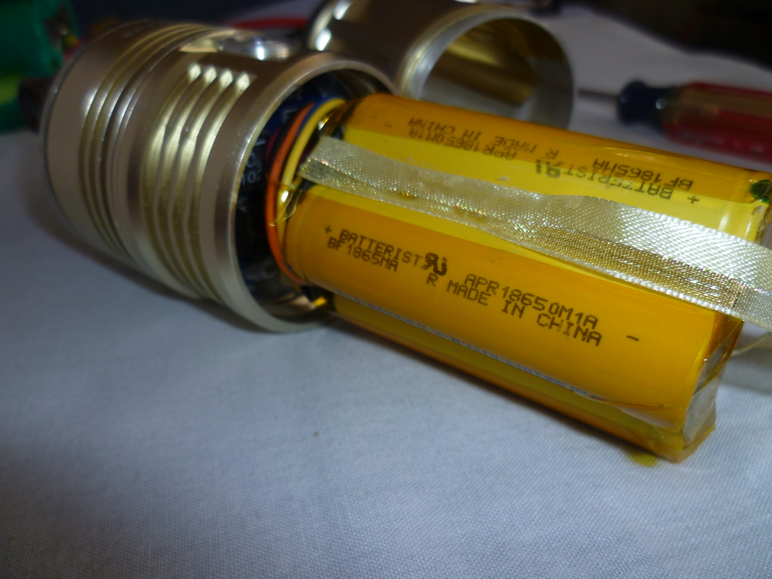
images/P1020682.JPG
