hardboiledfrog/smt-zvs-driver/images/P1020683.JPG

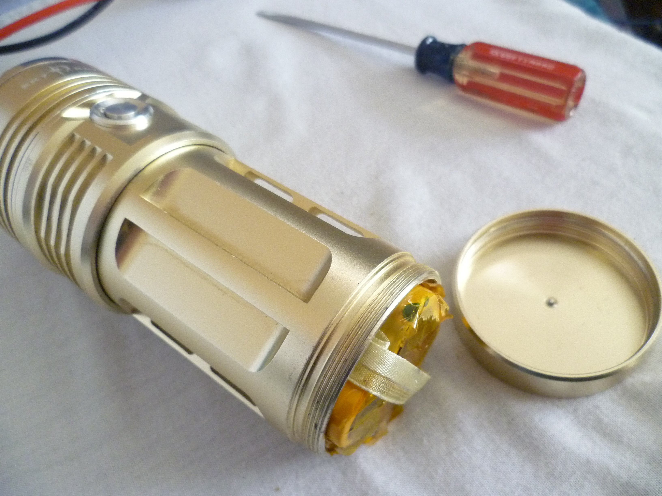
images/P1020683.JPG
