hardboiledfrog/smt-zvs-driver/images/P1020685.JPG

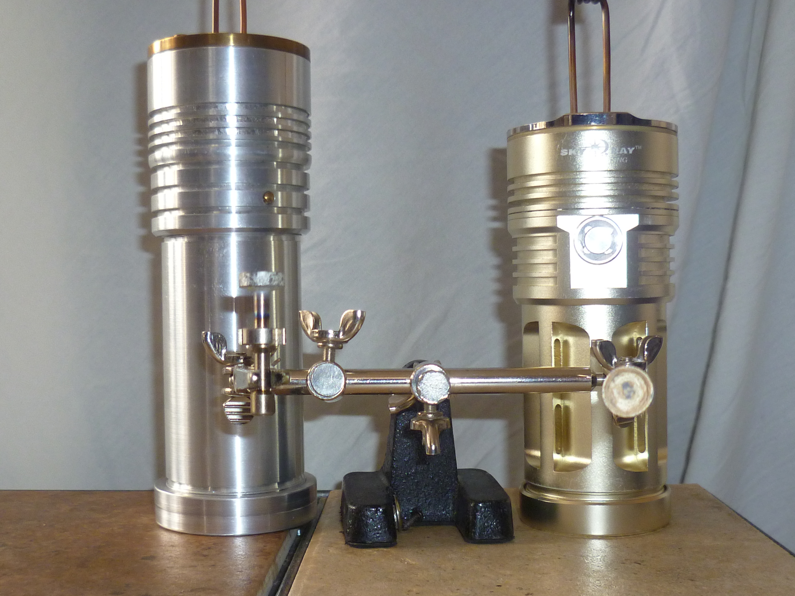
images/P1020685.JPG
