hardboiledfrog/smt-zvs-driver/images/P1020686.JPG

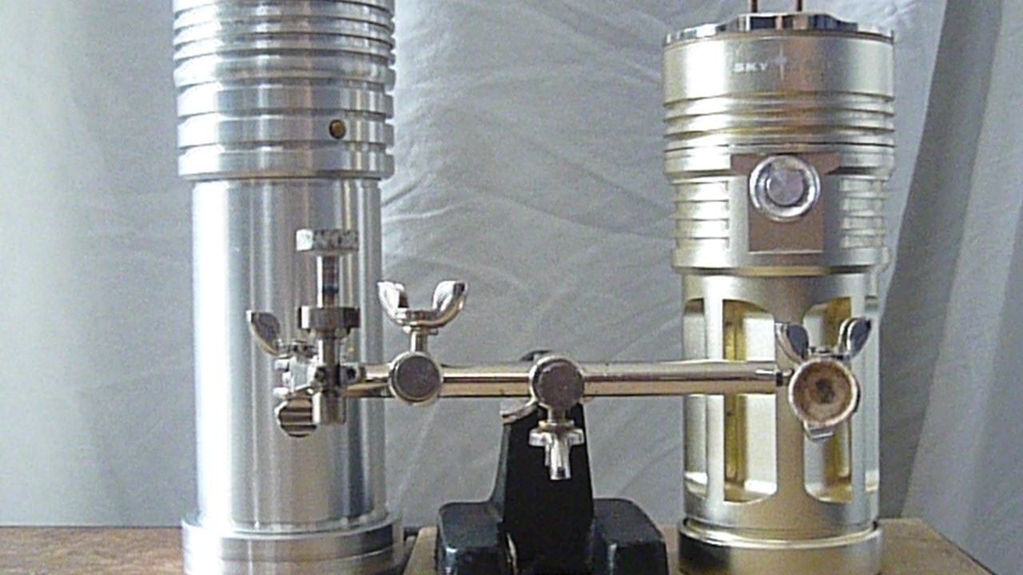
images/P1020686.JPG
