hardboiledfrog/smt-zvs-driver/images/P1020687.JPG

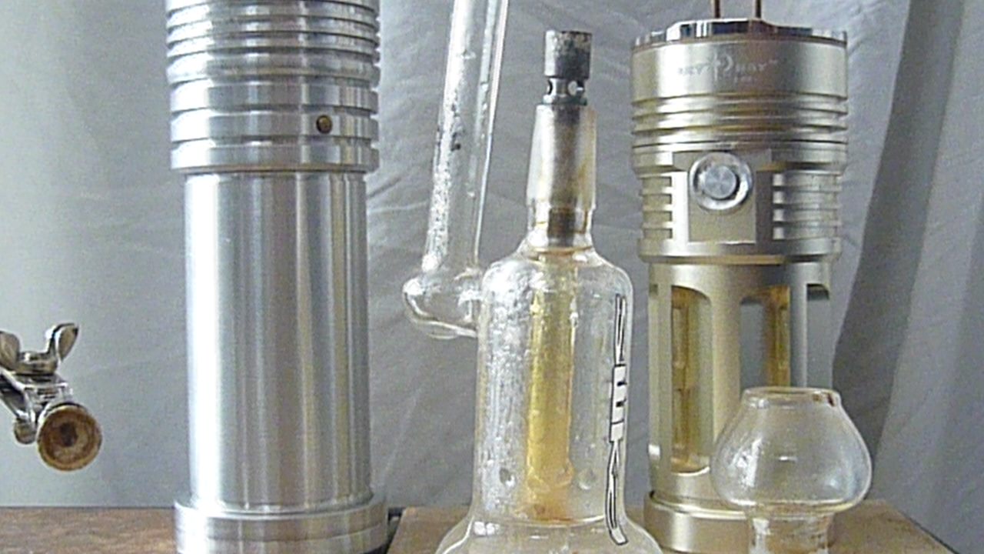
images/P1020687.JPG
