hardboiledfrog/smt-zvs-driver/images/P1020688.JPG

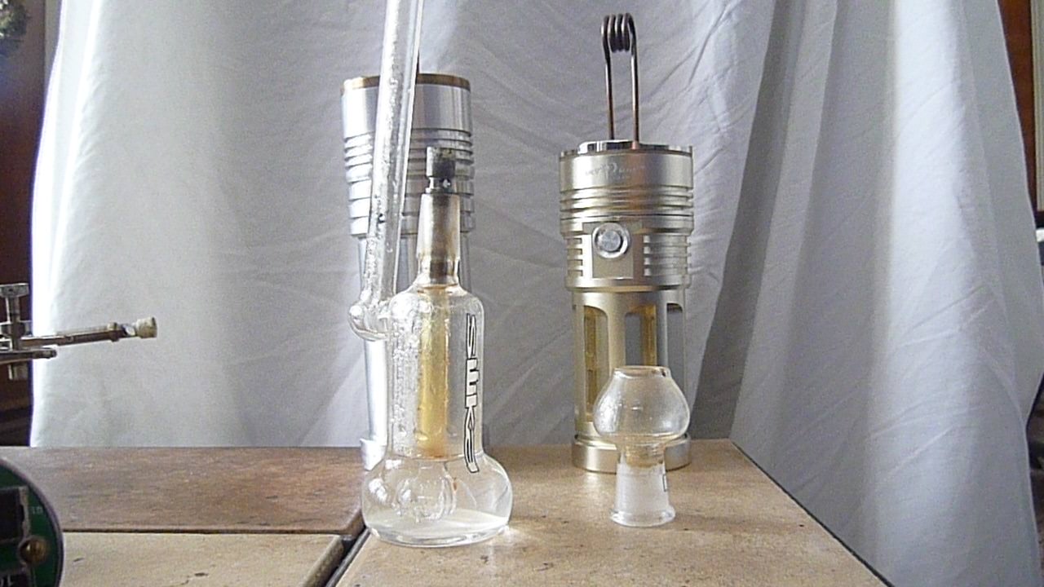
images/P1020688.JPG
