hardboiledfrog/smt-zvs-driver/images/P1020691.JPG

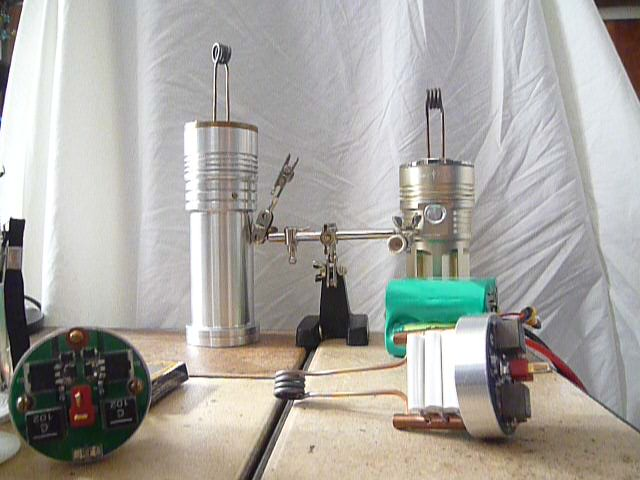
images/P1020691.JPG
