hardboiledfrog/smt-zvs-driver/images/P1020692.JPG

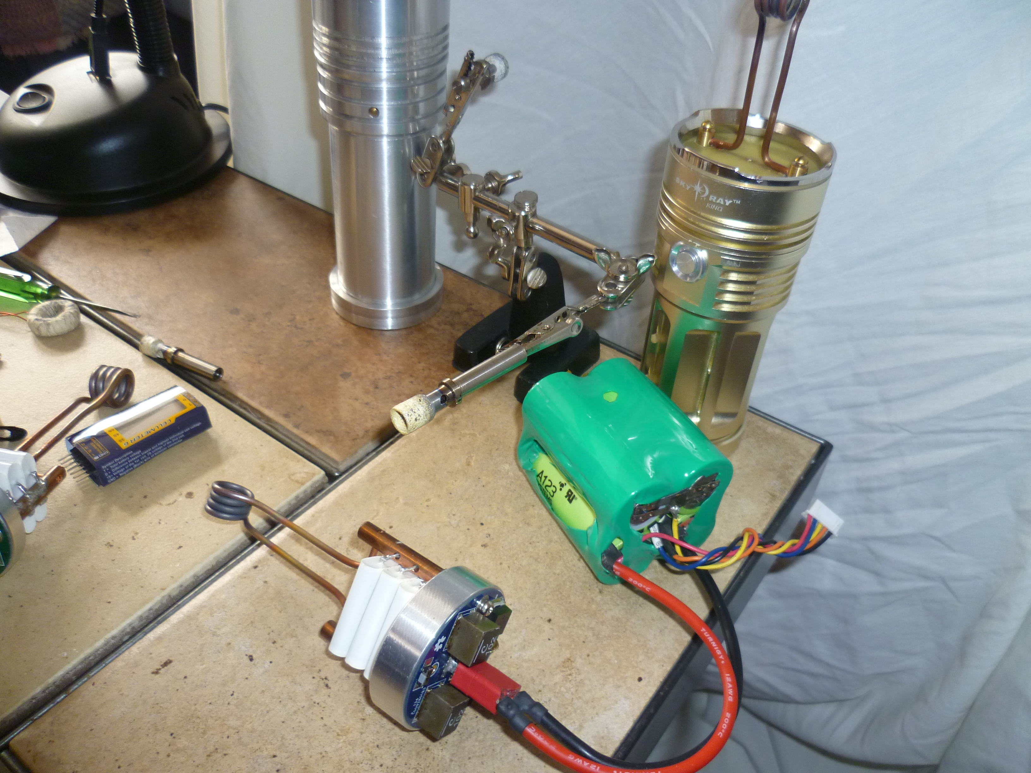
images/P1020692.JPG
