hardboiledfrog/smt-zvs-driver/images/P1020693.JPG

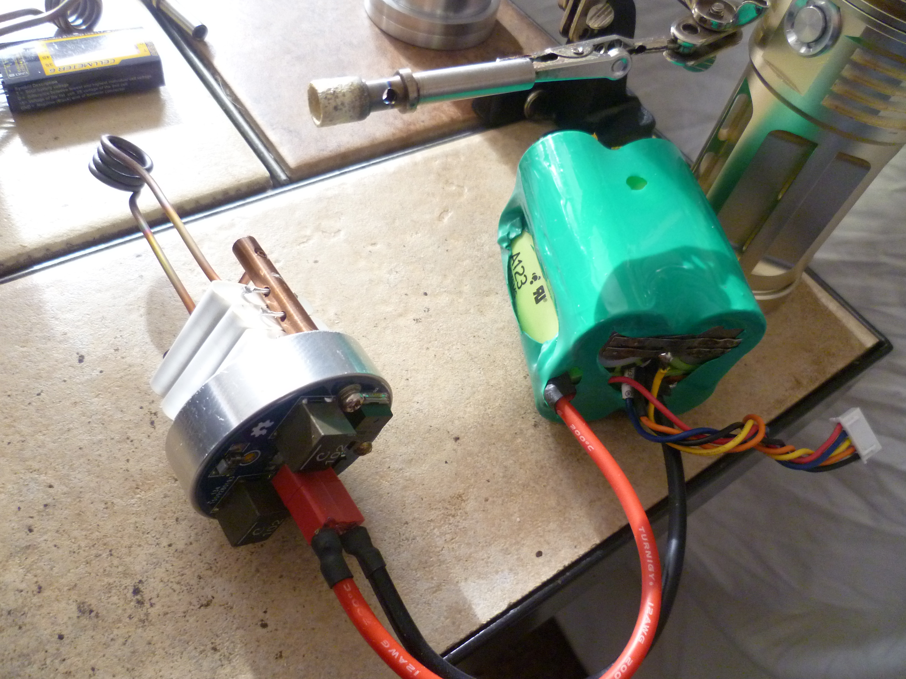
images/P1020693.JPG
