hardboiledfrog/smt-zvs-driver/images/P1020694.JPG

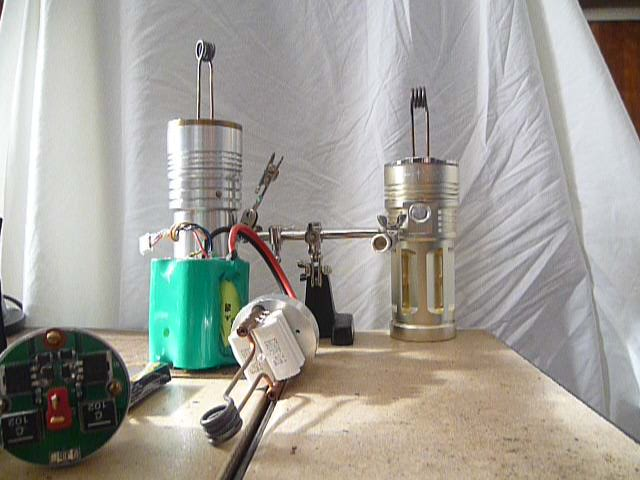
images/P1020694.JPG
