hardboiledfrog/smt-zvs-driver/images/P1020695.JPG

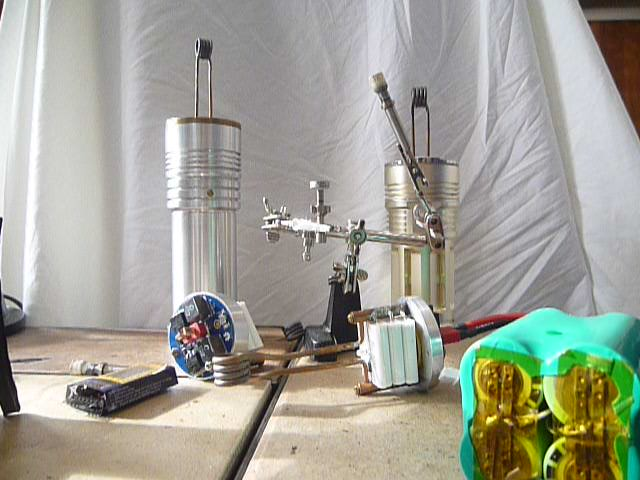
images/P1020695.JPG
