hardboiledfrog/smt-zvs-driver/images/P1020696.JPG

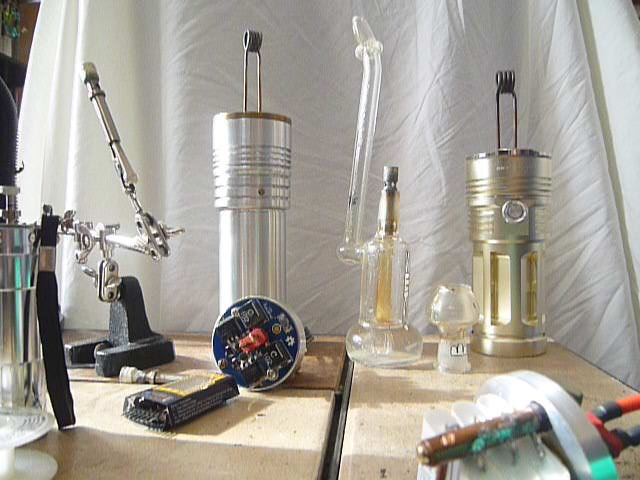
images/P1020696.JPG
