hardboiledfrog/smt-zvs-driver/images/P1020697.JPG

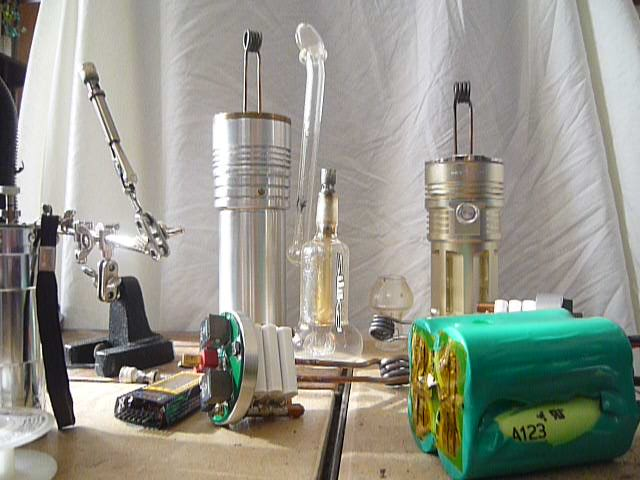
images/P1020697.JPG
