hardboiledfrog/smt-zvs-driver/images/P1020698.JPG

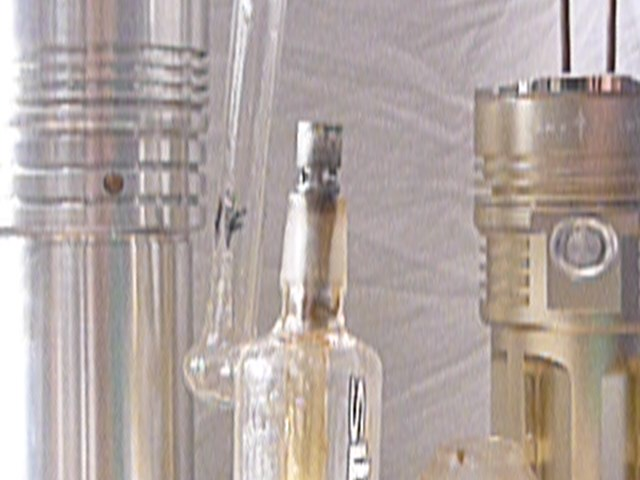
images/P1020698.JPG
