hardboiledfrog/smt-zvs-driver/images/P1020699.JPG

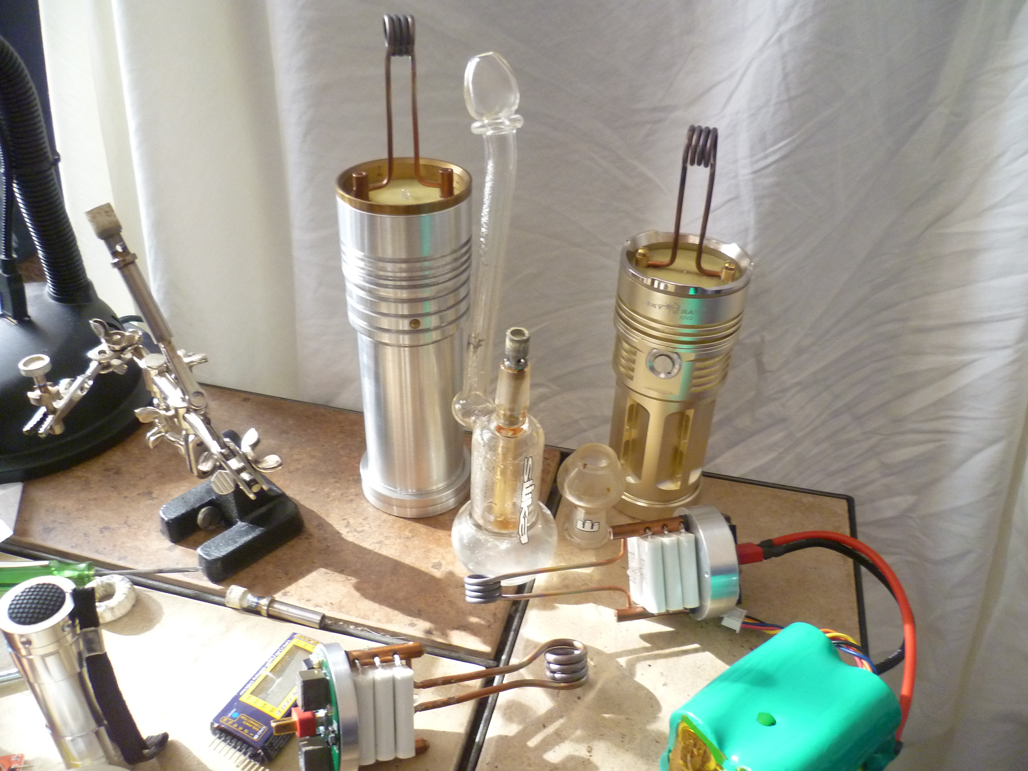
images/P1020699.JPG
