hardboiledfrog/smt-zvs-driver/images/P1020700.JPG

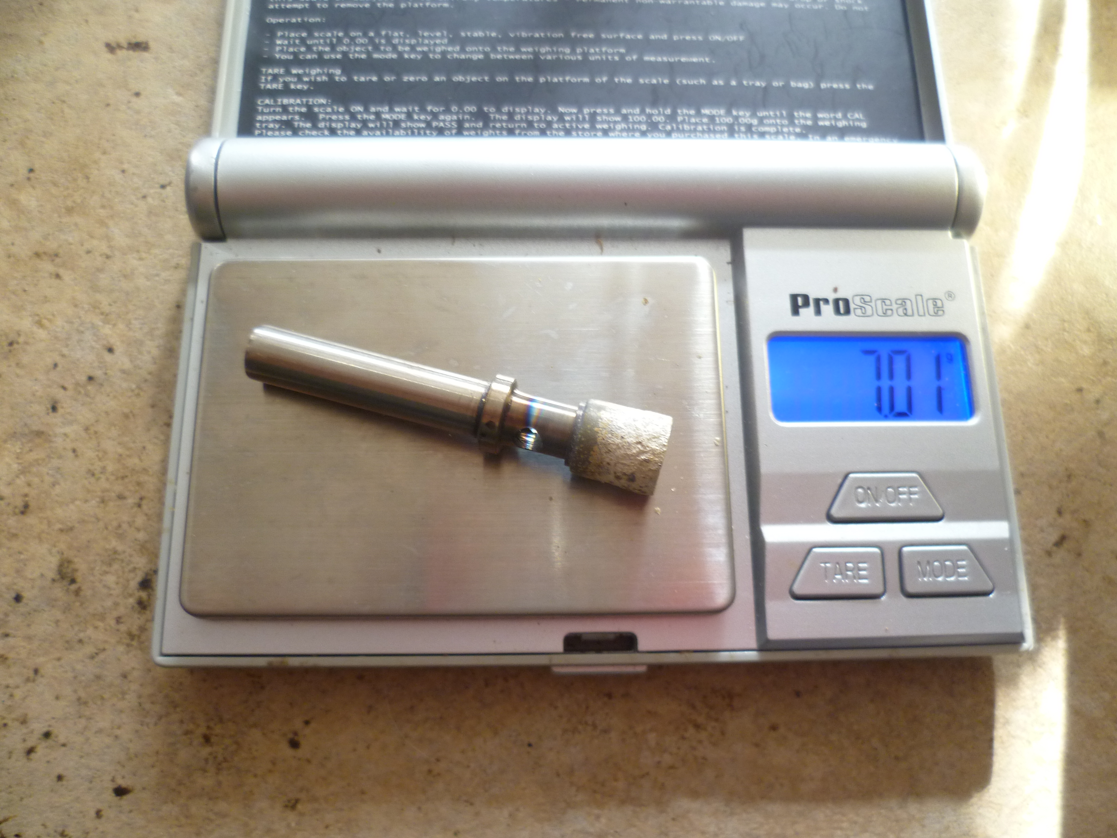
images/P1020700.JPG
