hardboiledfrog/smt-zvs-driver/images/P1020701.JPG

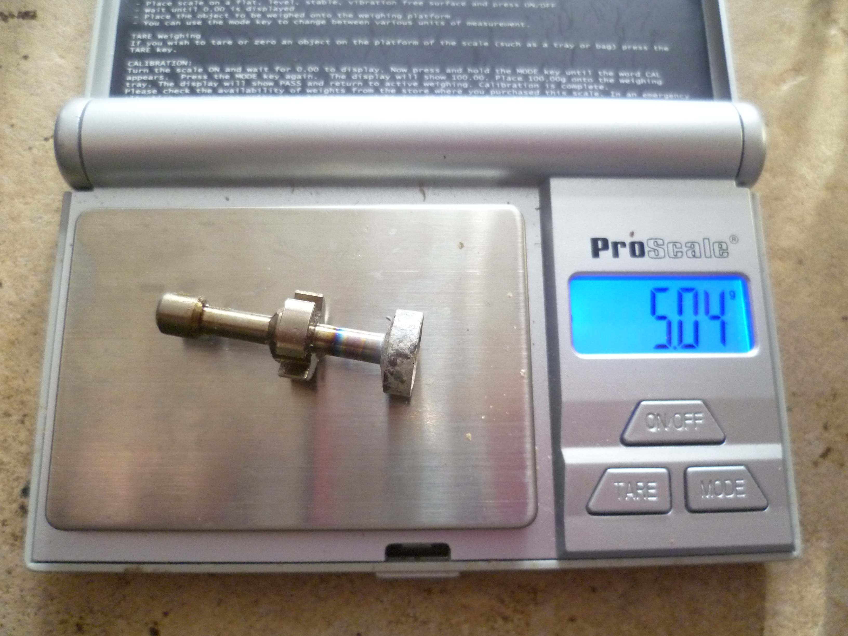
images/P1020701.JPG
