hardboiledfrog/smt-zvs-driver/images/P1020702.JPG

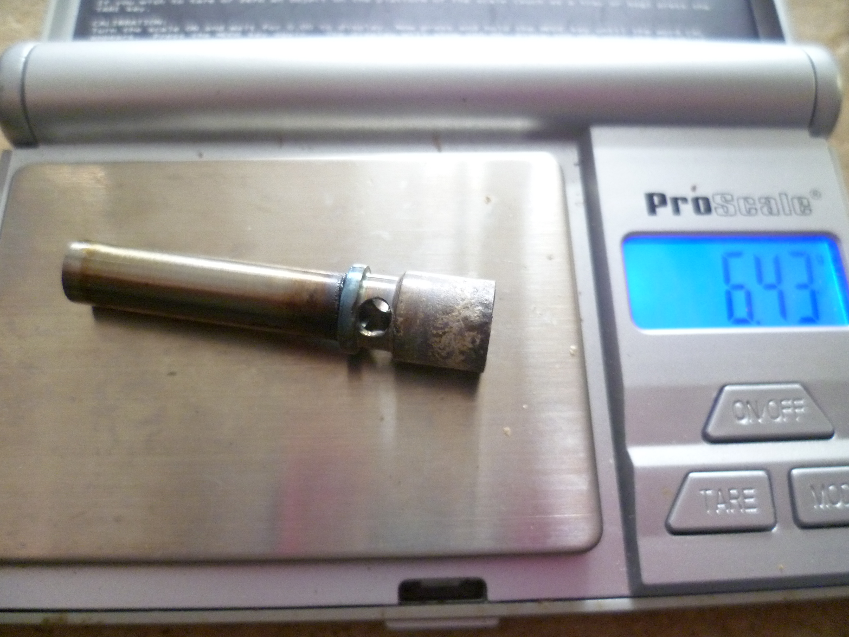
images/P1020702.JPG
