hardboiledfrog/smt-zvs-driver/images/P1020703.JPG

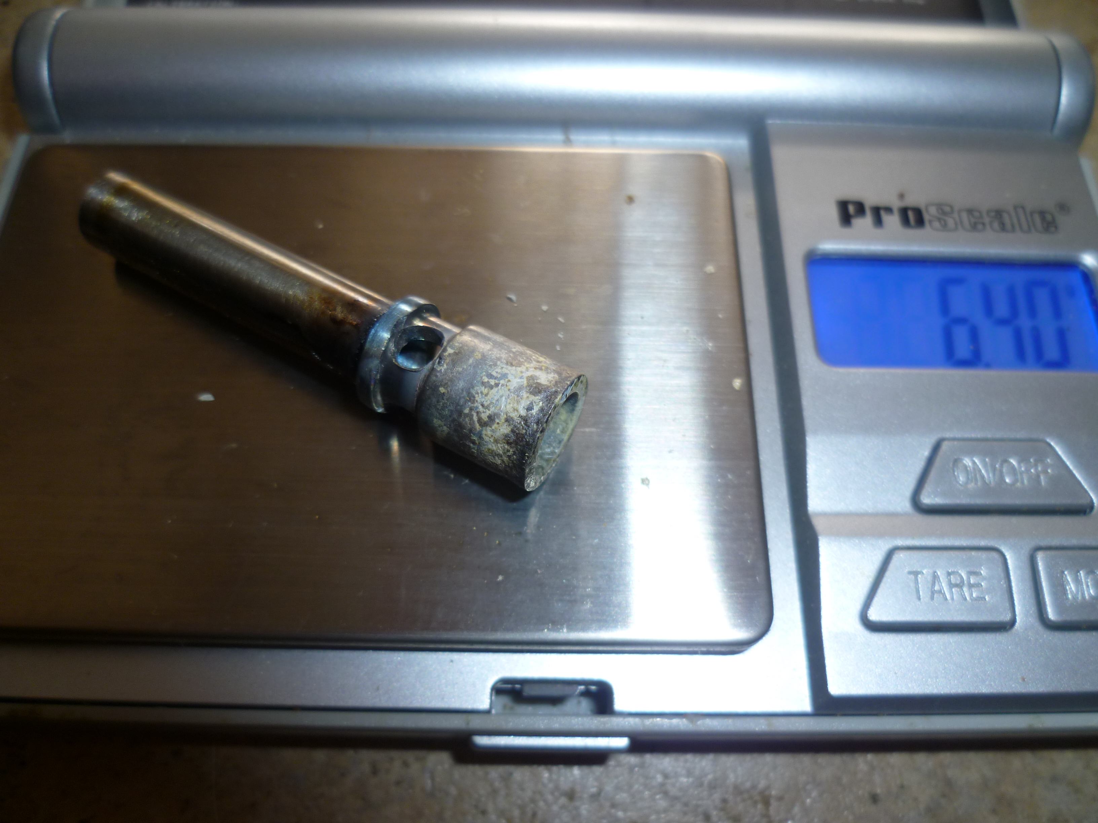
images/P1020703.JPG
