hardboiledfrog/smt-zvs-driver/images/P1020705.JPG

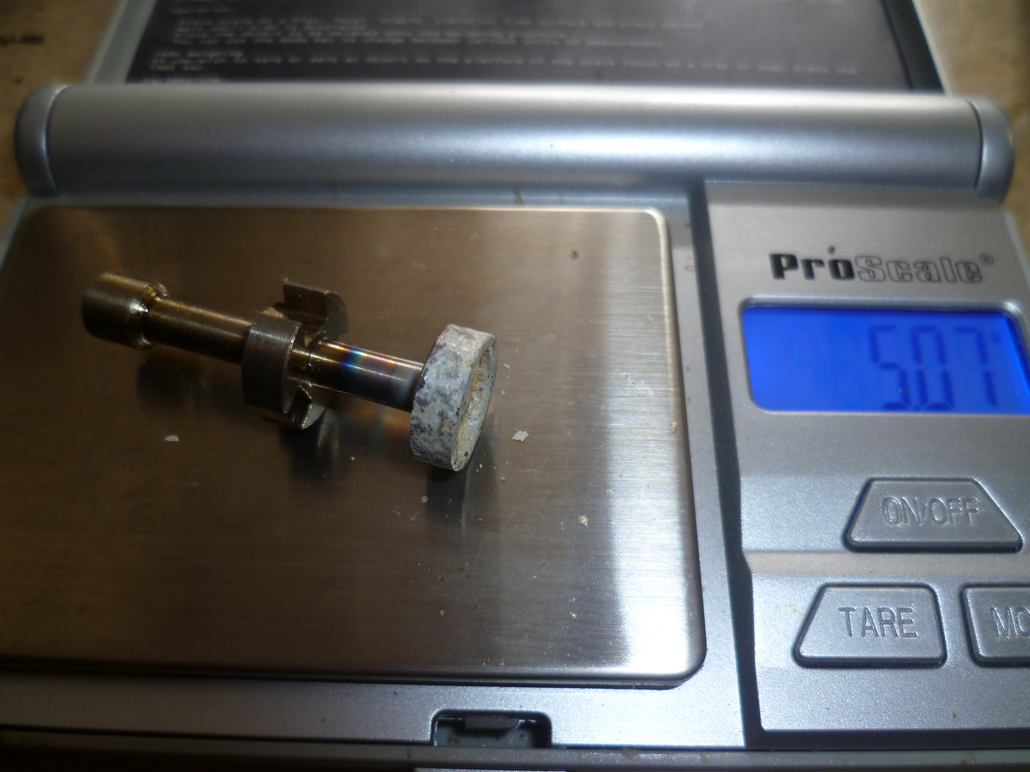
images/P1020705.JPG
