hardboiledfrog/smt-zvs-driver/images/P1020706.JPG

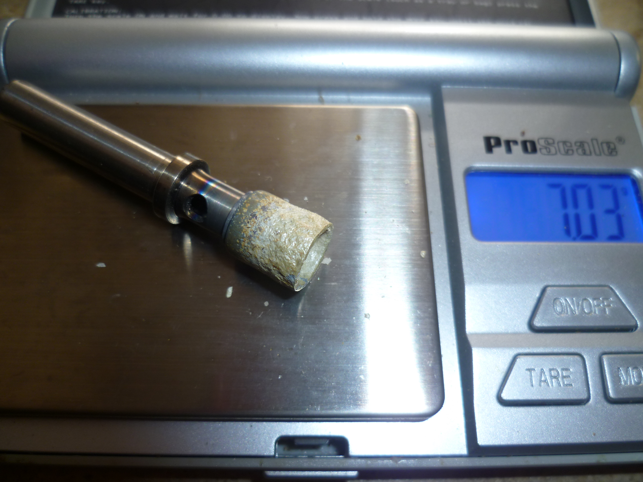
images/P1020706.JPG
