hardboiledfrog/smt-zvs-driver/images/P1020713.JPG

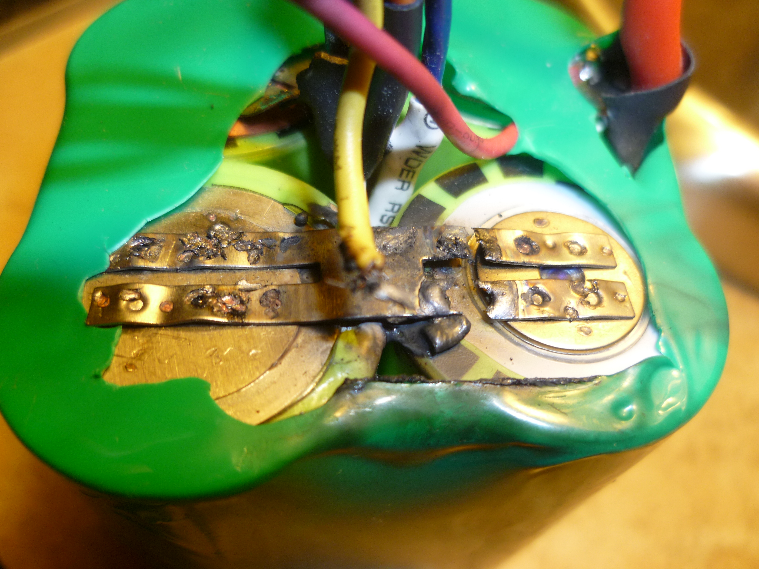
images/P1020713.JPG
