hardboiledfrog/smt-zvs-driver/images/P1020714.JPG

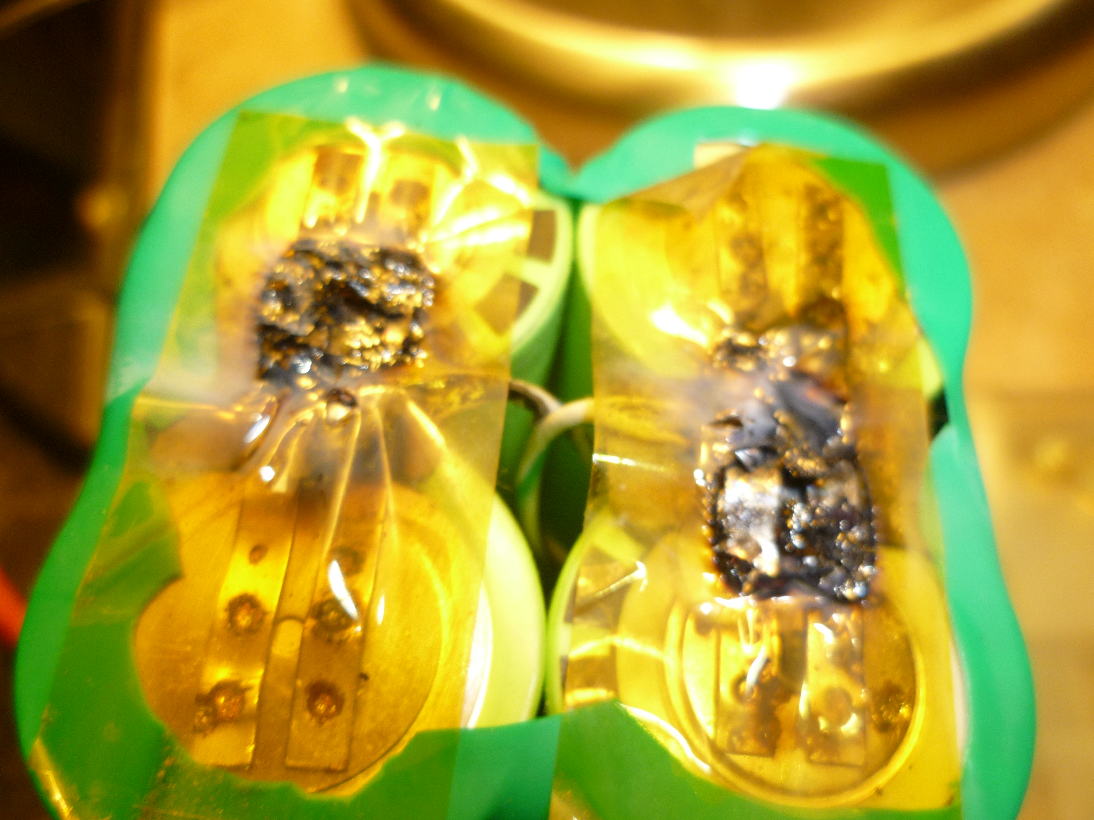
images/P1020714.JPG
