hardboiledfrog/smt-zvs-driver/images/P1020715.JPG

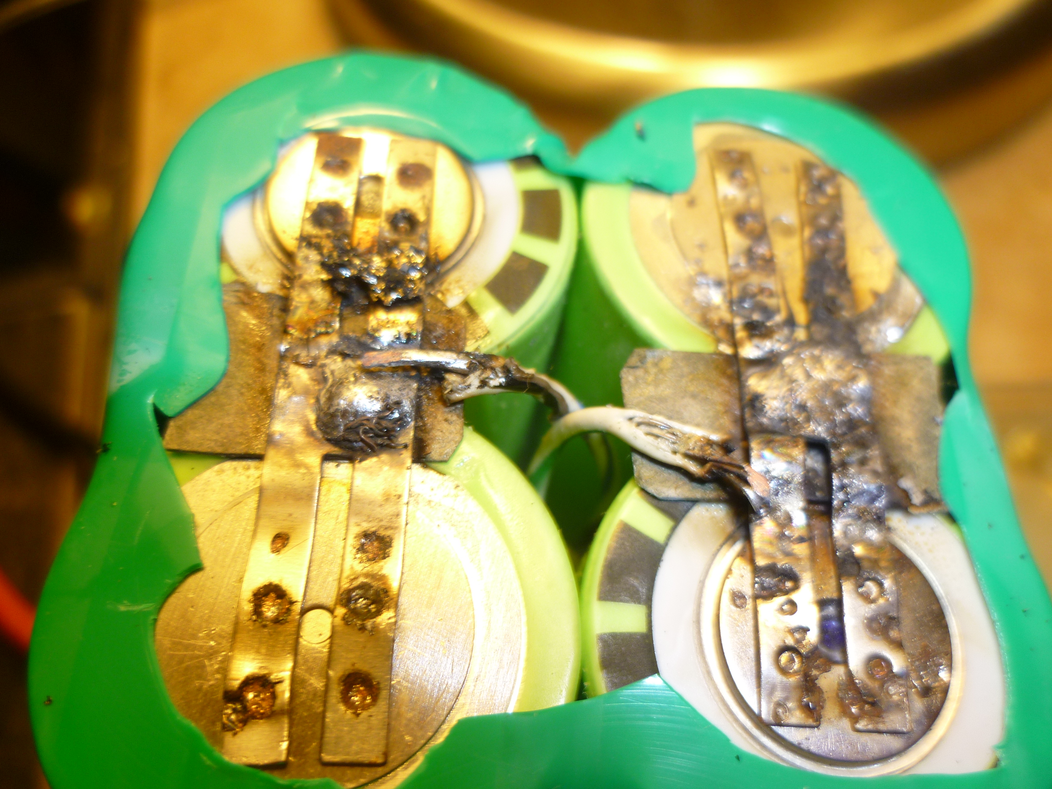
images/P1020715.JPG
