hardboiledfrog/smt-zvs-driver/images/P1020716.JPG

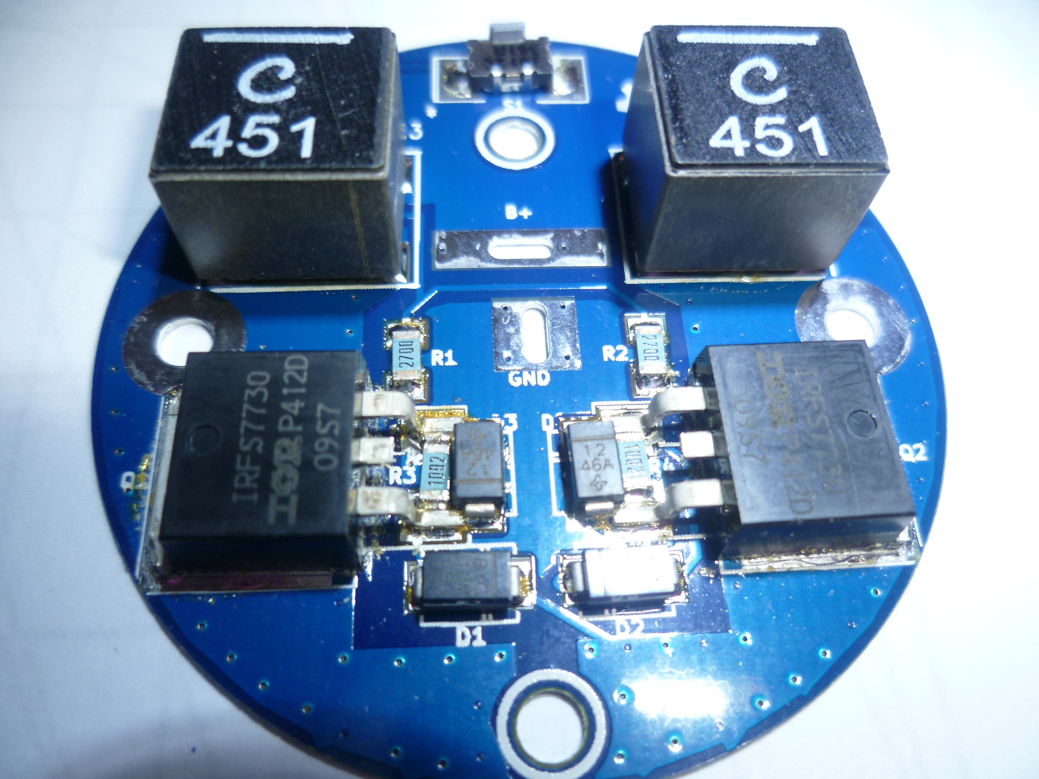
images/P1020716.JPG
