hardboiledfrog/smt-zvs-driver/images/P1020717.JPG

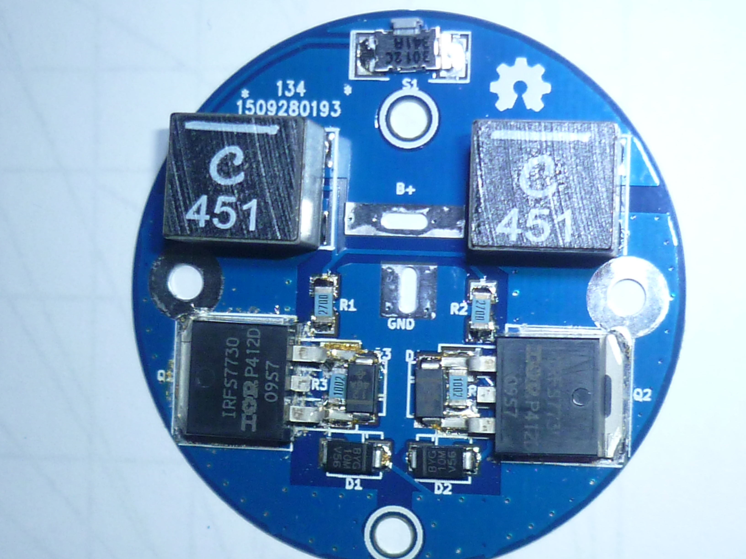
images/P1020717.JPG
