hardboiledfrog/smt-zvs-driver/images/P1020718.JPG

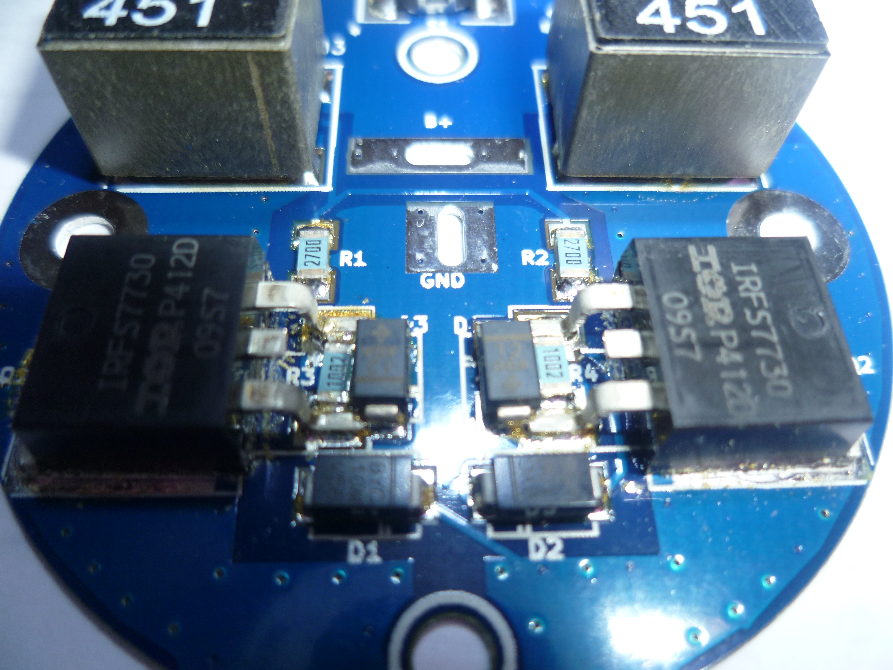
images/P1020718.JPG
