hardboiledfrog/smt-zvs-driver/images/P1020719.JPG

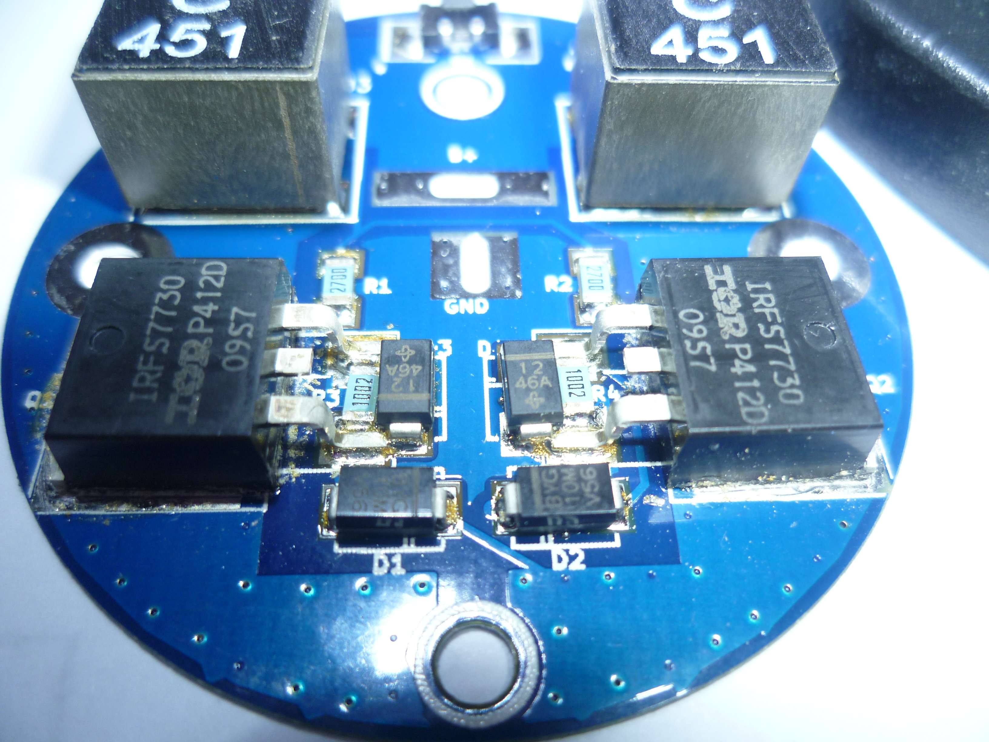
images/P1020719.JPG
