hardboiledfrog/smt-zvs-driver/images/P1020720.JPG

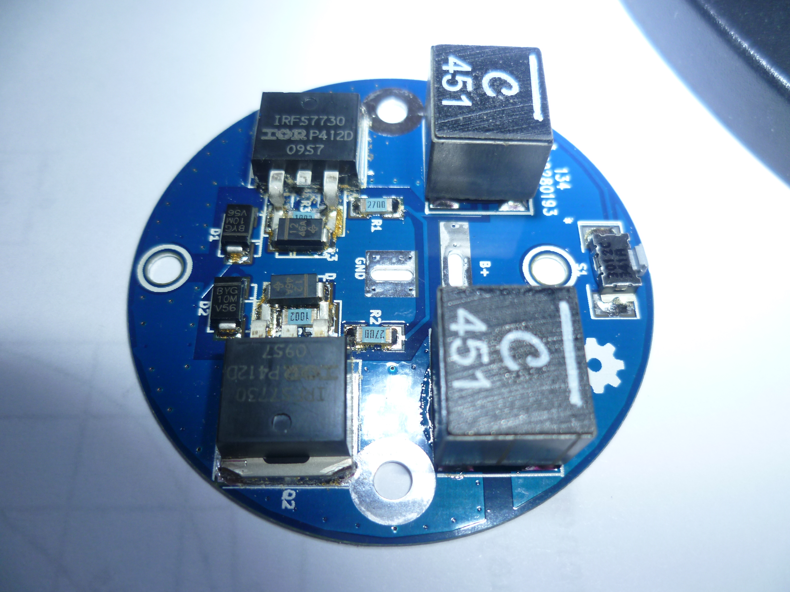
images/P1020720.JPG
