hardboiledfrog/smt-zvs-driver/images/P1020721.JPG

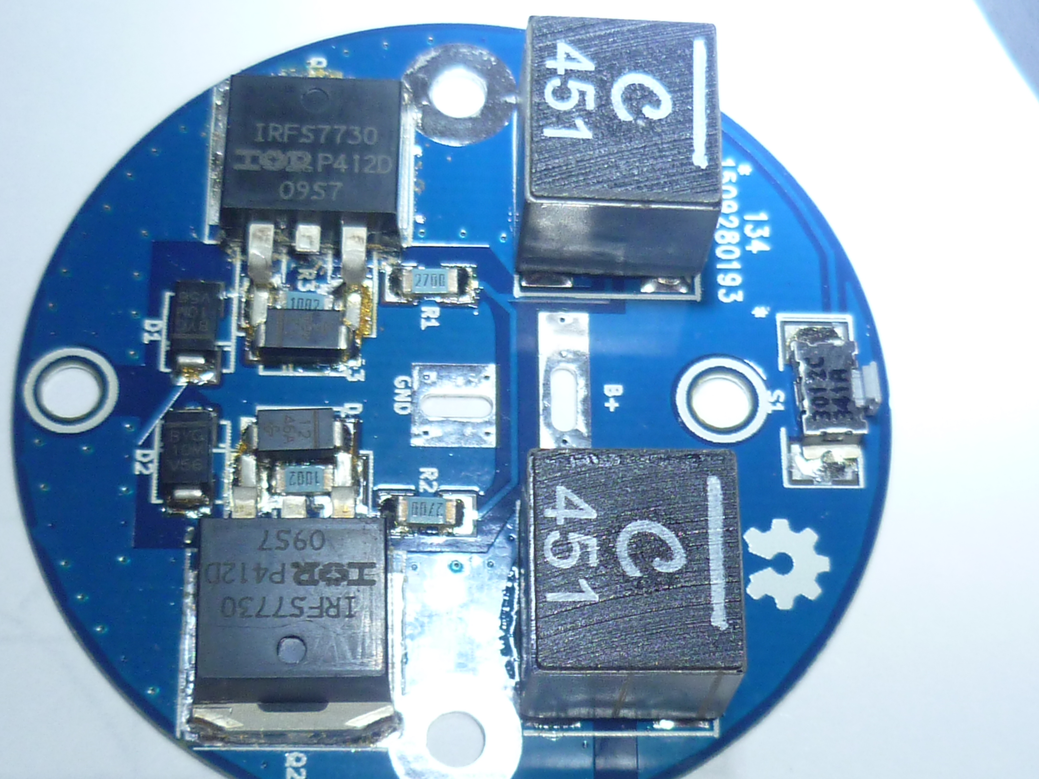
images/P1020721.JPG
