hardboiledfrog/smt-zvs-driver/images/P1020722.JPG

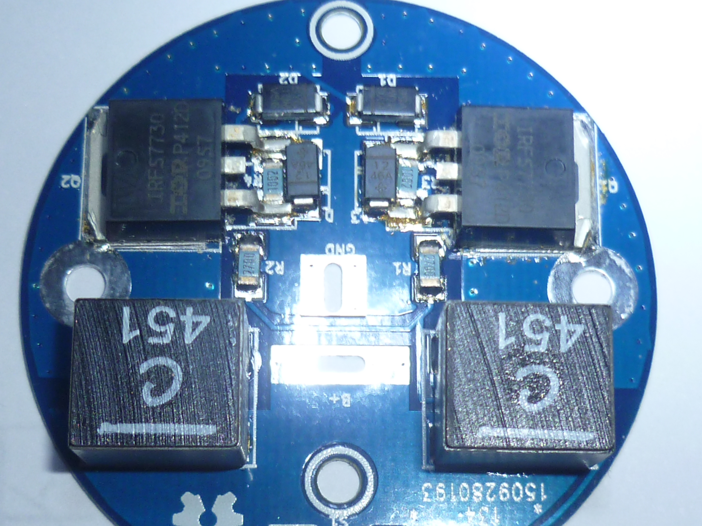
images/P1020722.JPG
