hardboiledfrog/smt-zvs-driver/images/P1020723.JPG

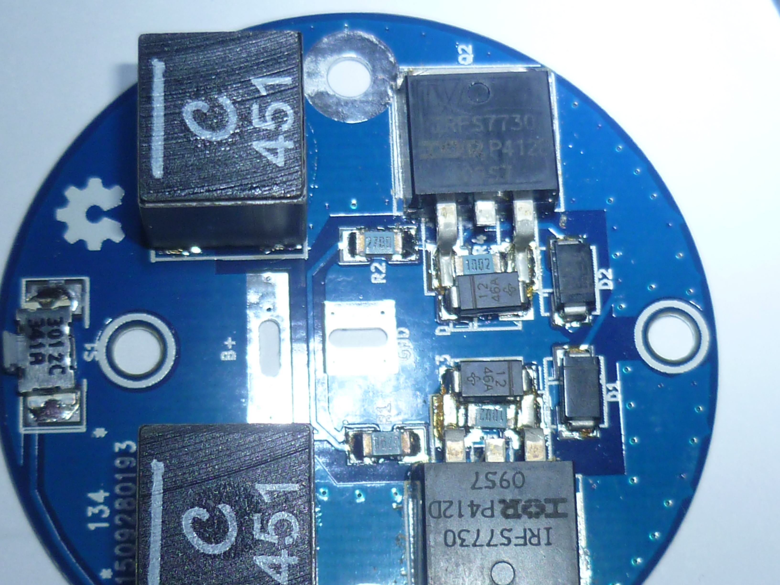
images/P1020723.JPG
