hardboiledfrog/smt-zvs-driver/images/P1020724.JPG

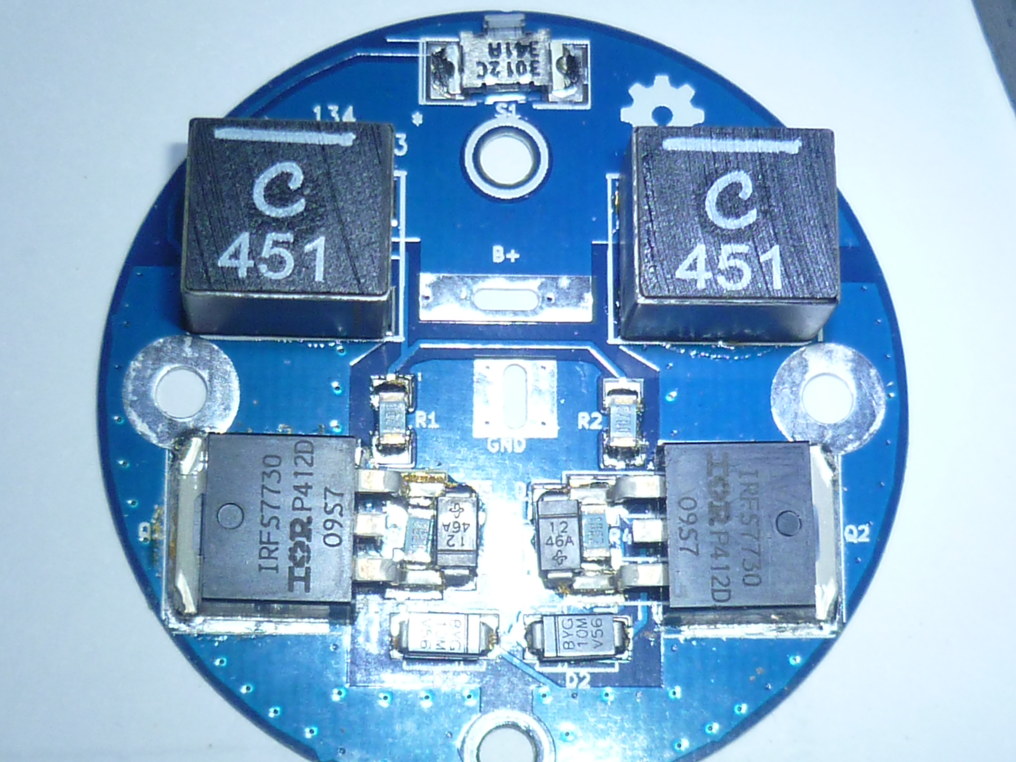
images/P1020724.JPG
