hardboiledfrog/smt-zvs-driver/images/P1020726.JPG

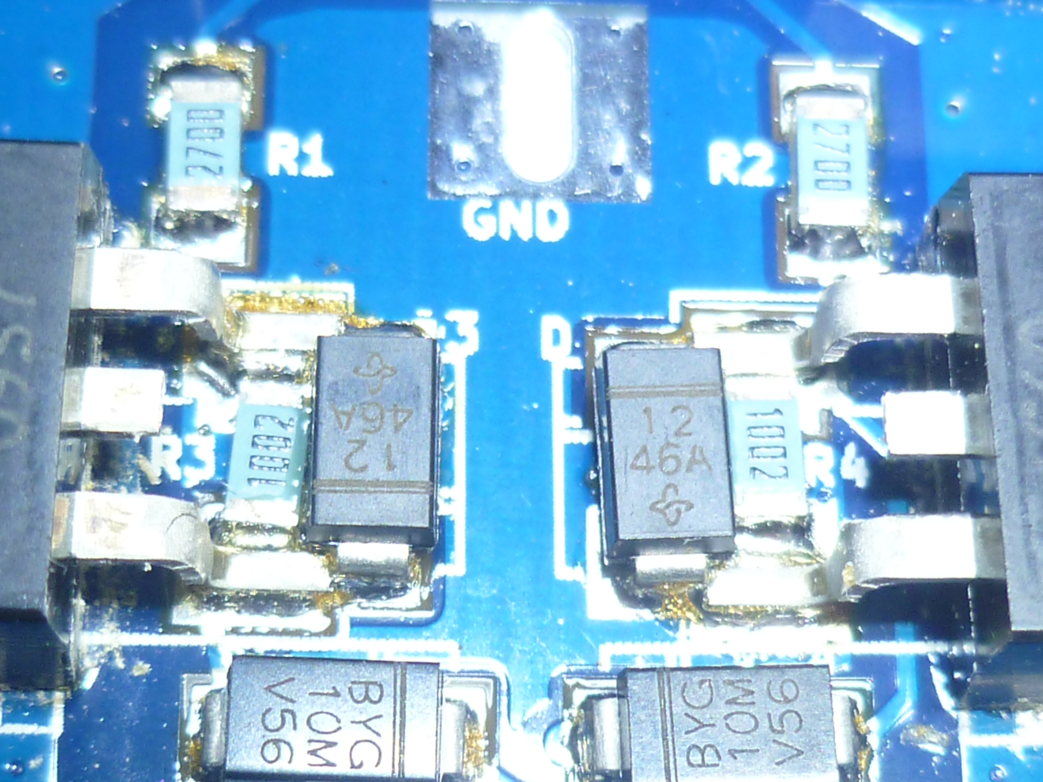
images/P1020726.JPG
