hardboiledfrog/smt-zvs-driver/images/P1020727.JPG

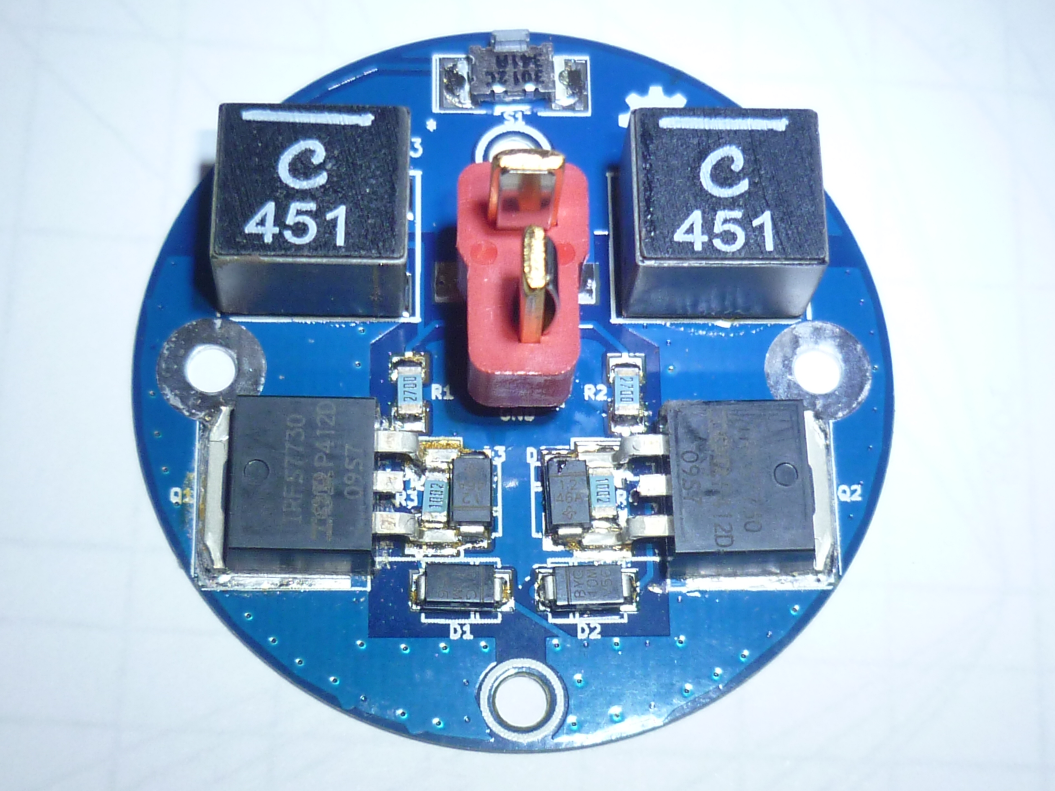
images/P1020727.JPG
