hardboiledfrog/smt-zvs-driver/images/P1020728.JPG

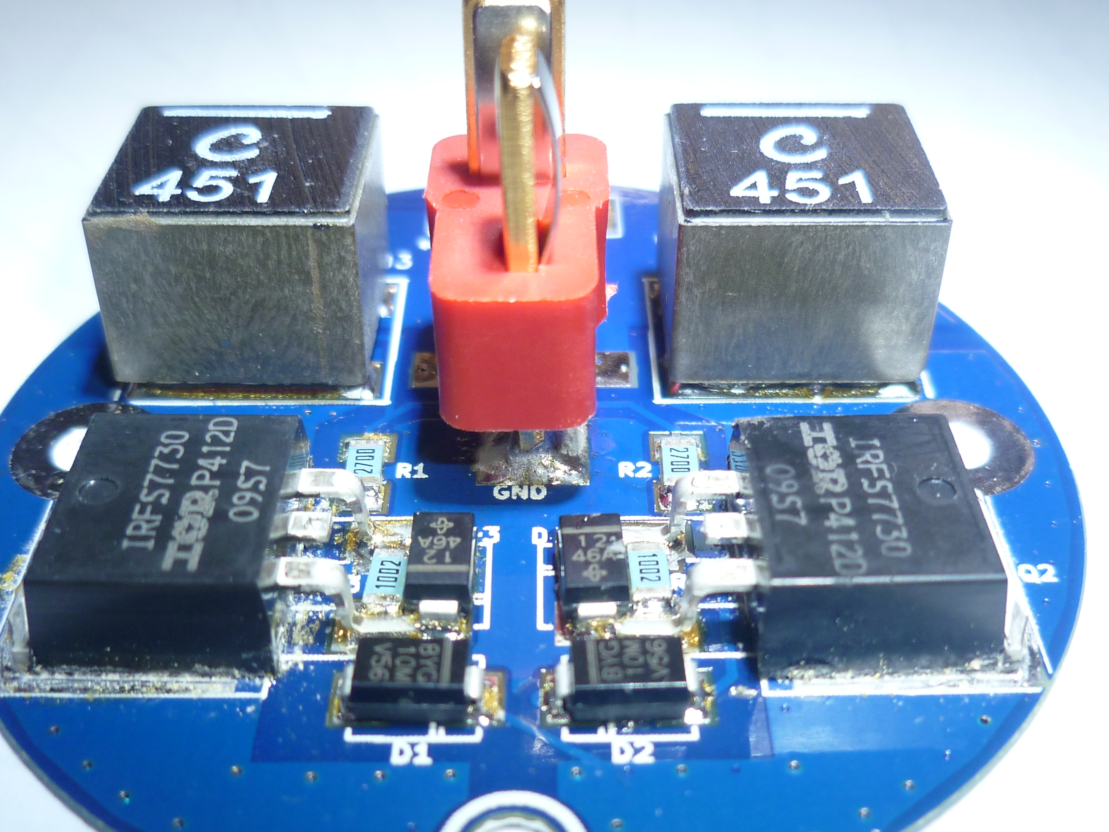
images/P1020728.JPG
