hardboiledfrog/smt-zvs-driver/images/P1020729.JPG

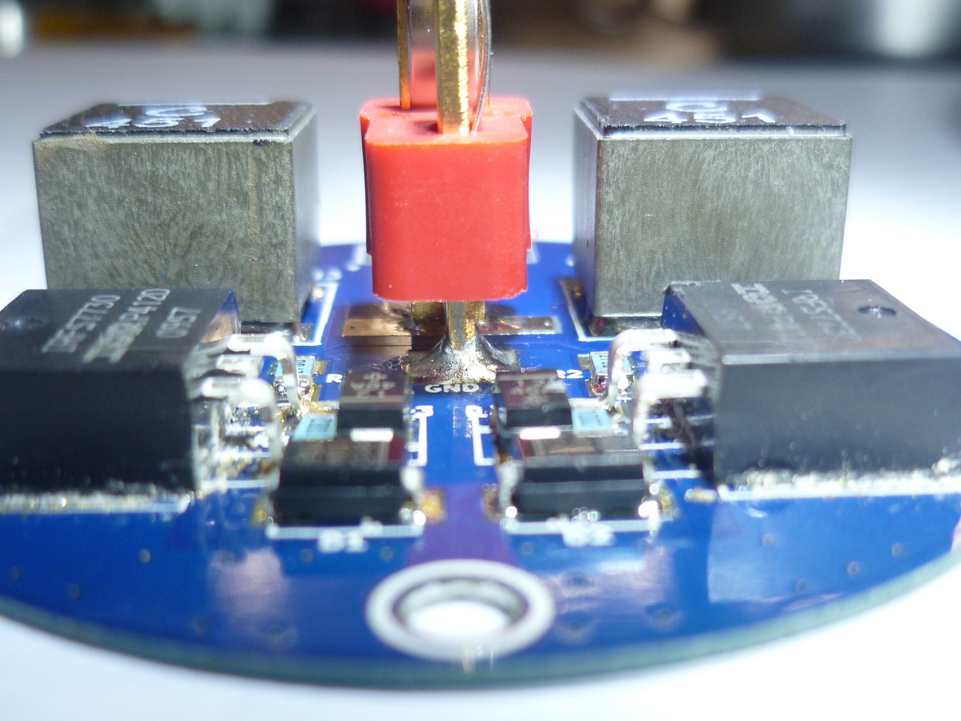
images/P1020729.JPG
