hardboiledfrog/smt-zvs-driver/images/P1020730.JPG

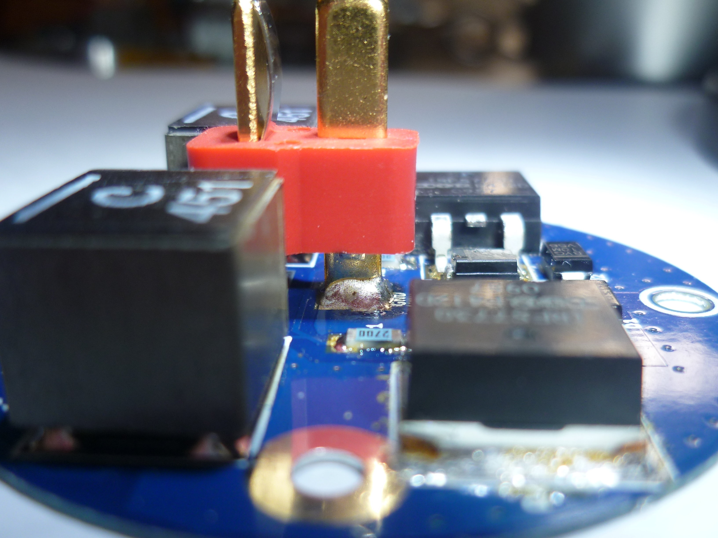
images/P1020730.JPG
