hardboiledfrog/smt-zvs-driver/images/P1020731.JPG

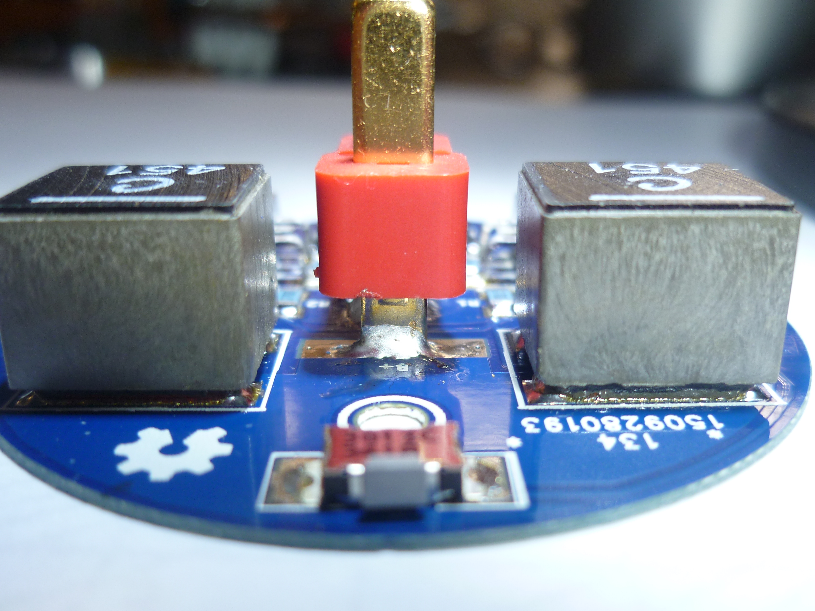
images/P1020731.JPG
