hardboiledfrog/smt-zvs-driver/images/P1020746.JPG

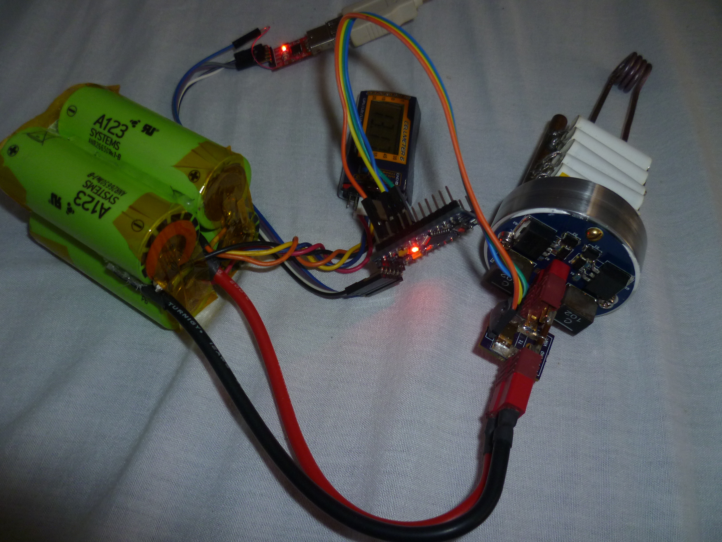
images/P1020746.JPG
