hardboiledfrog/smt-zvs-driver/images/P1020747.JPG

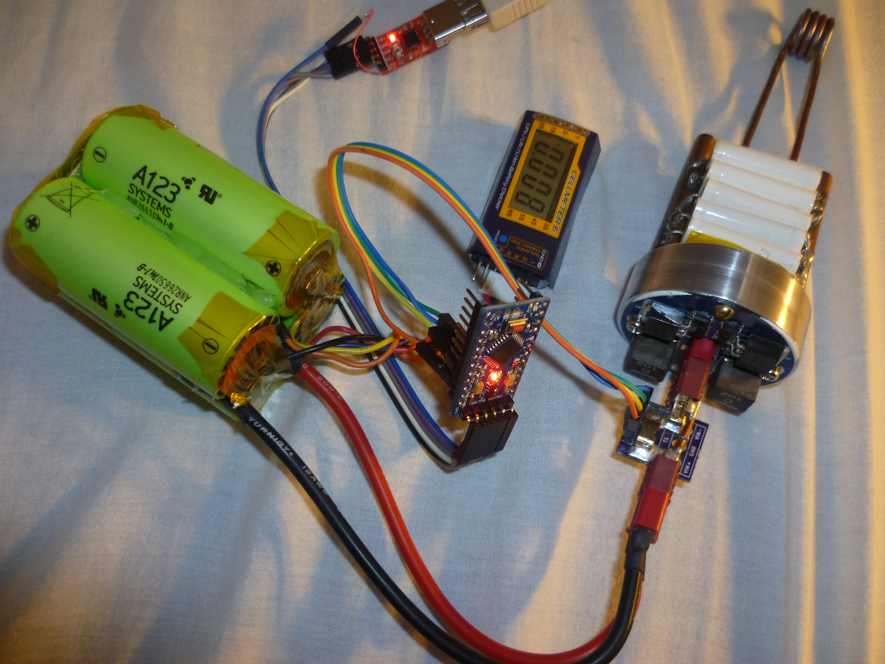
images/P1020747.JPG
