hardboiledfrog/smt-zvs-driver/images/P1020748.JPG

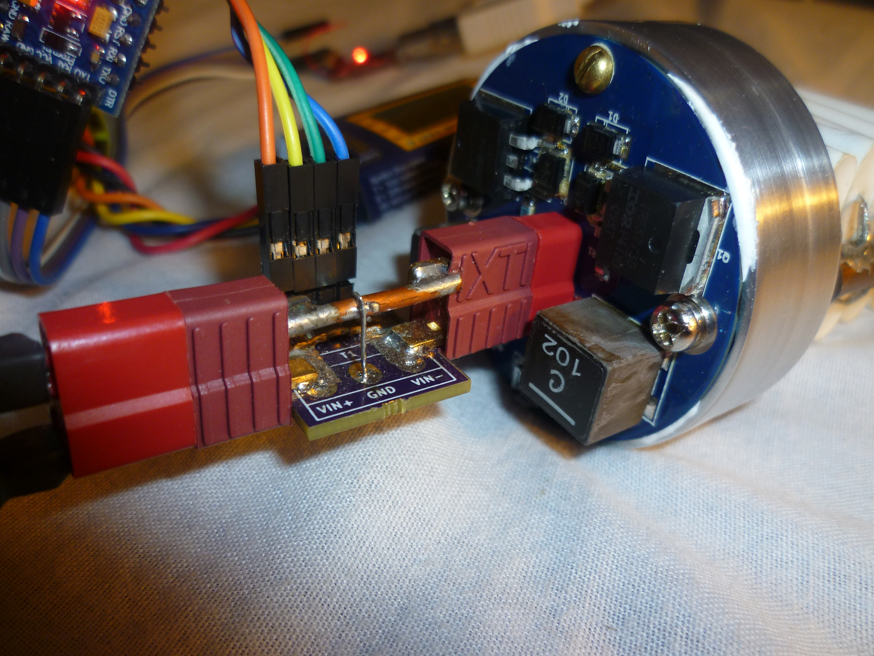
images/P1020748.JPG
