hardboiledfrog/smt-zvs-driver/images/P1020749.JPG

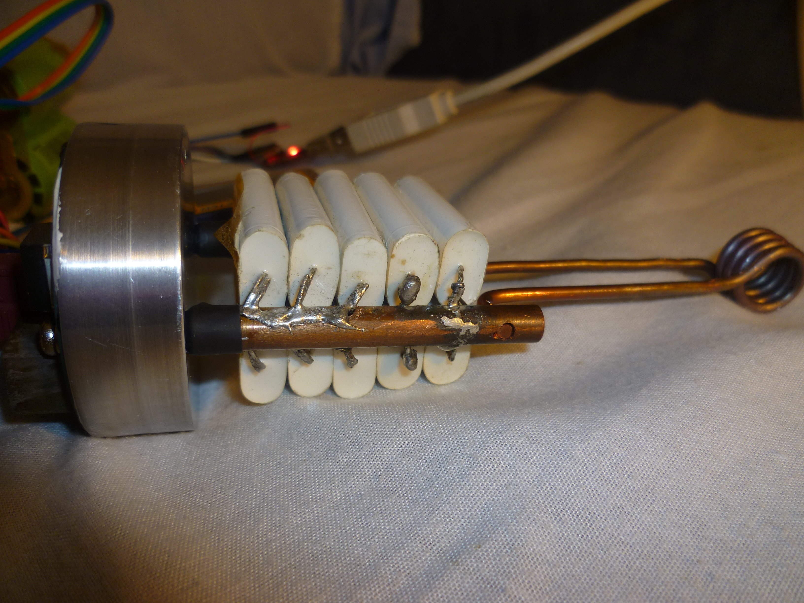
images/P1020749.JPG
