hardboiledfrog/smt-zvs-driver/images/P1020750.JPG

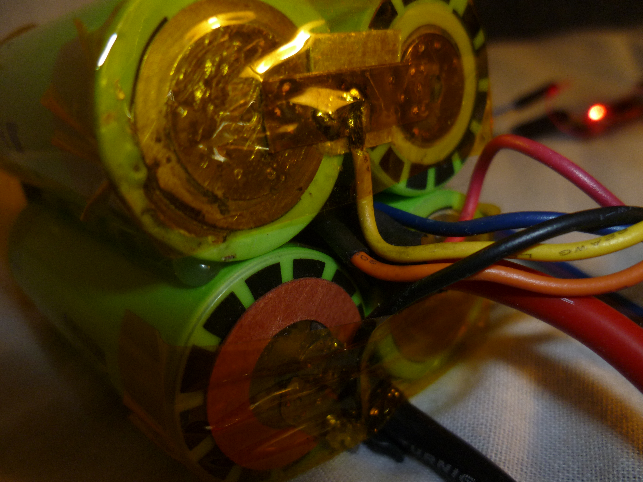
images/P1020750.JPG
