hardboiledfrog/smt-zvs-driver/images/P1020751.JPG

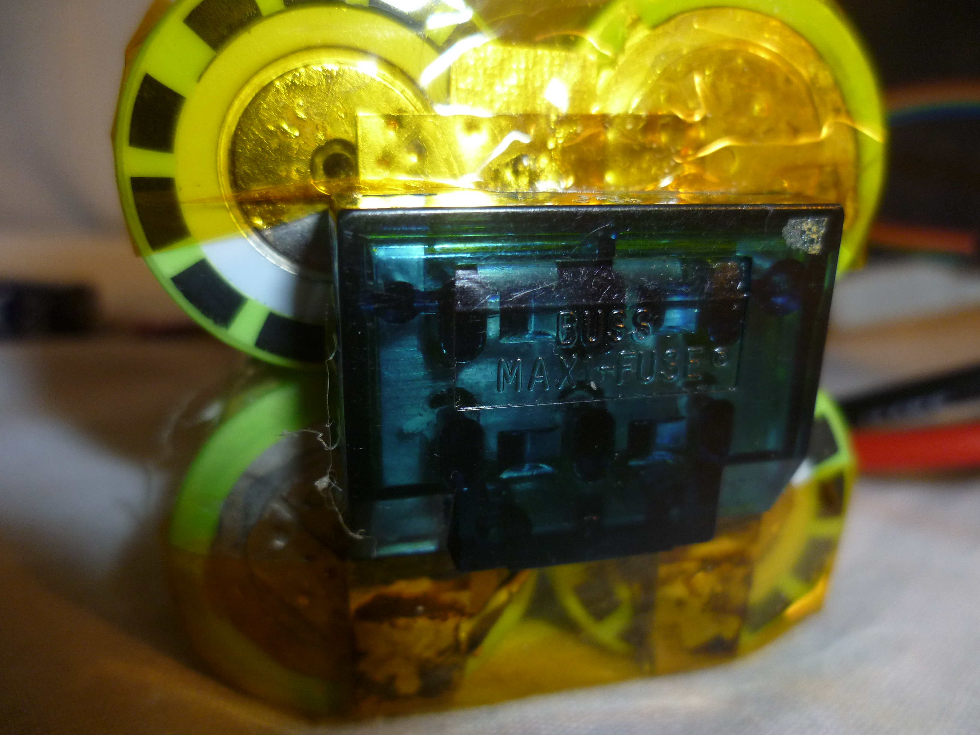
images/P1020751.JPG
