hardboiledfrog/smt-zvs-driver/images/P1020752.JPG

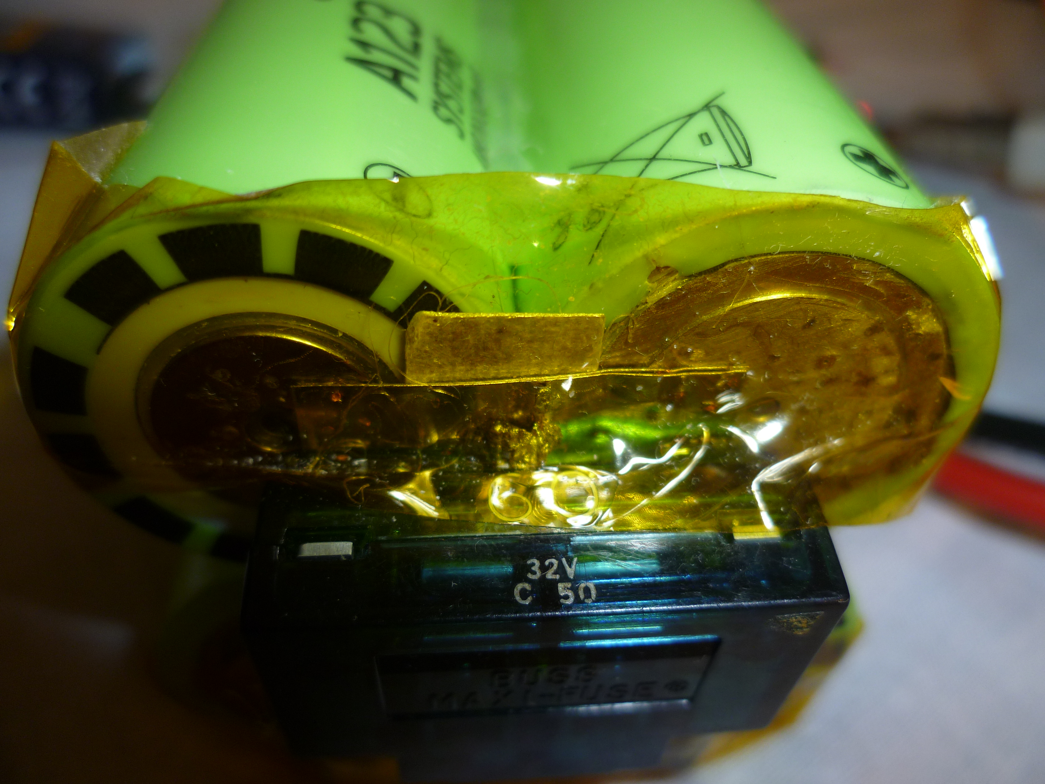
images/P1020752.JPG
