hardboiledfrog/smt-zvs-driver/images/P1020753.JPG

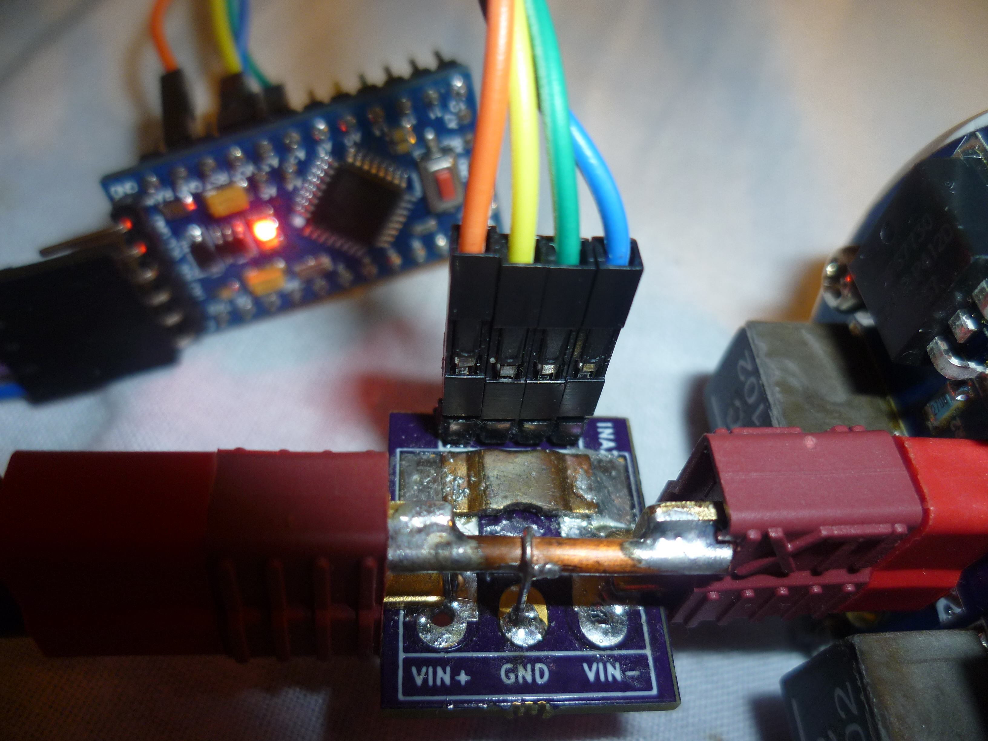
images/P1020753.JPG
