hardboiledfrog/smt-zvs-driver/images/P1020754.JPG

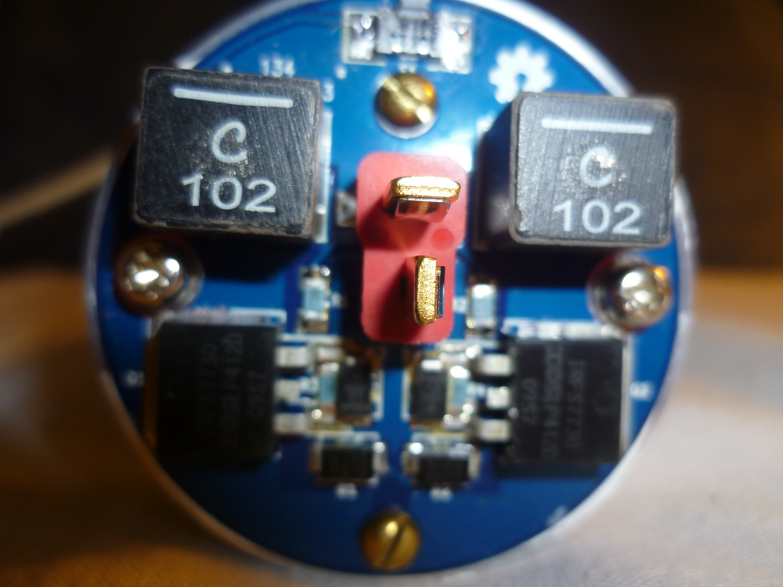
images/P1020754.JPG
