hardboiledfrog/smt-zvs-driver/images/P1020755.JPG

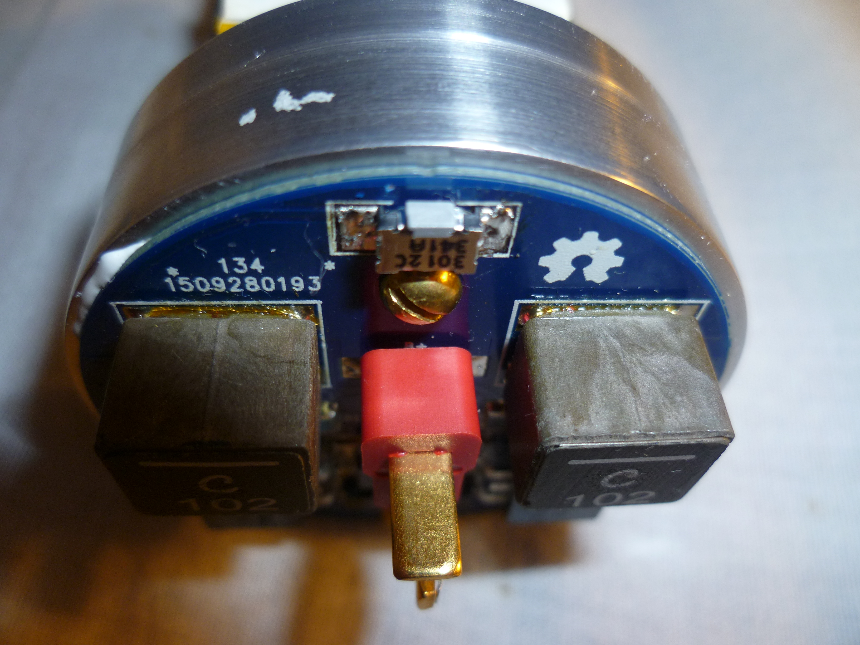
images/P1020755.JPG
