hardboiledfrog/smt-zvs-driver/images/P1020756.JPG

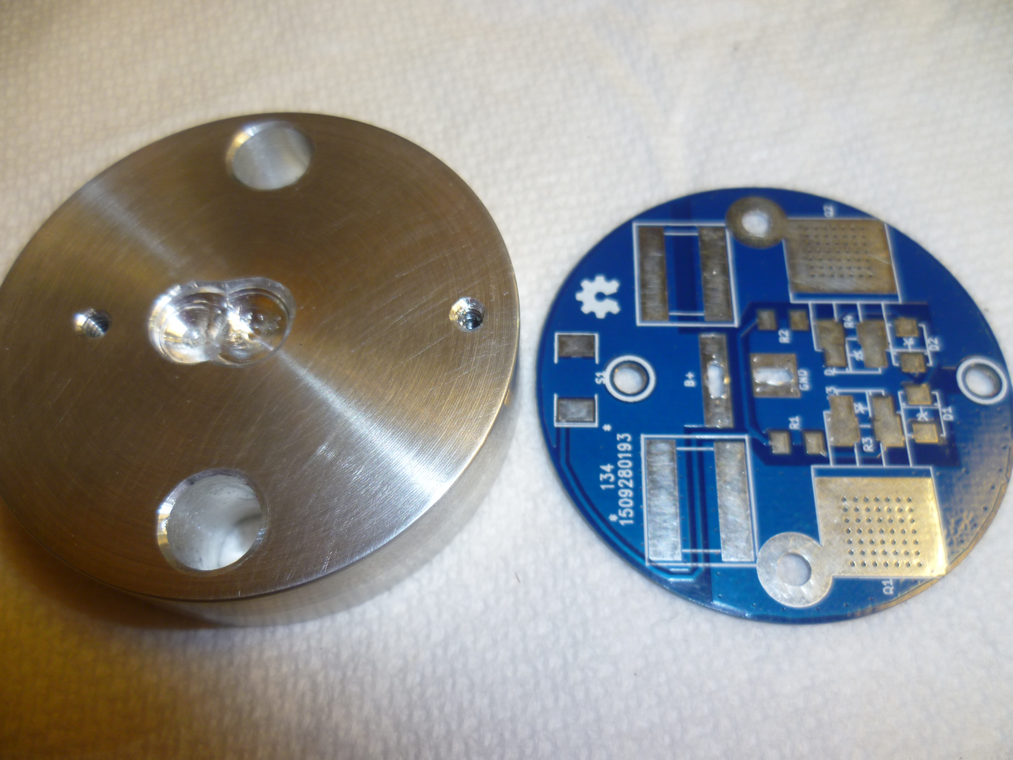
images/P1020756.JPG
