hardboiledfrog/smt-zvs-driver/images/P1020758.JPG

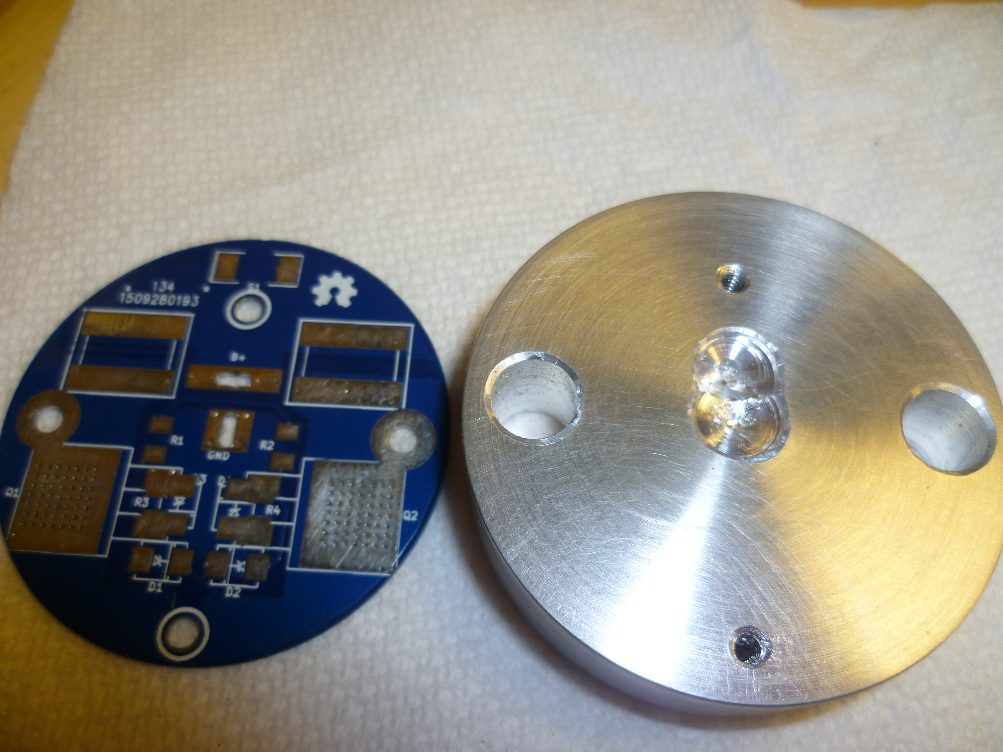
images/P1020758.JPG
