hardboiledfrog/smt-zvs-driver/images/proto/P1020017.JPG

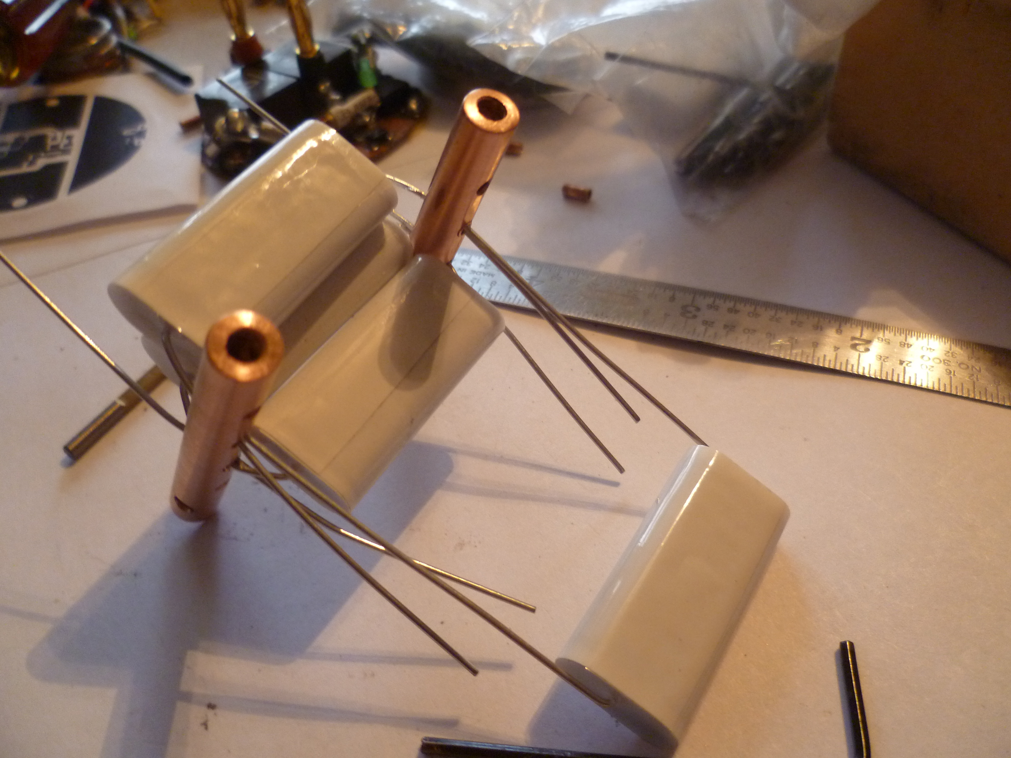
images/proto/P1020017.JPG
