hardboiledfrog/smt-zvs-driver/images/proto/P1020018.JPG

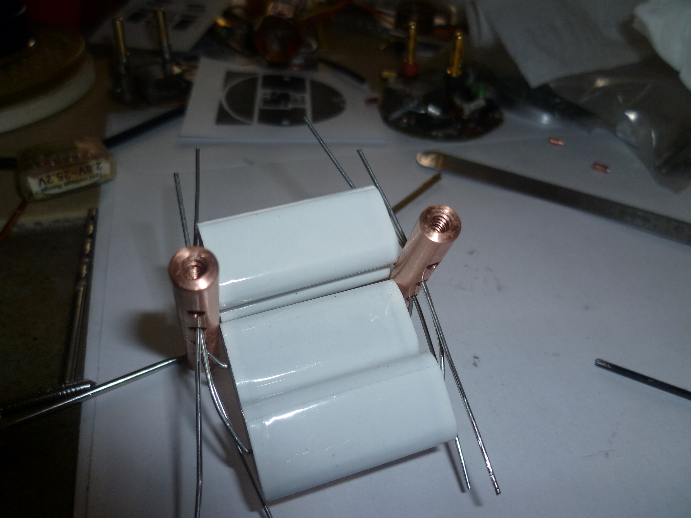
images/proto/P1020018.JPG
