hardboiledfrog/smt-zvs-driver/images/proto/P1020020.JPG

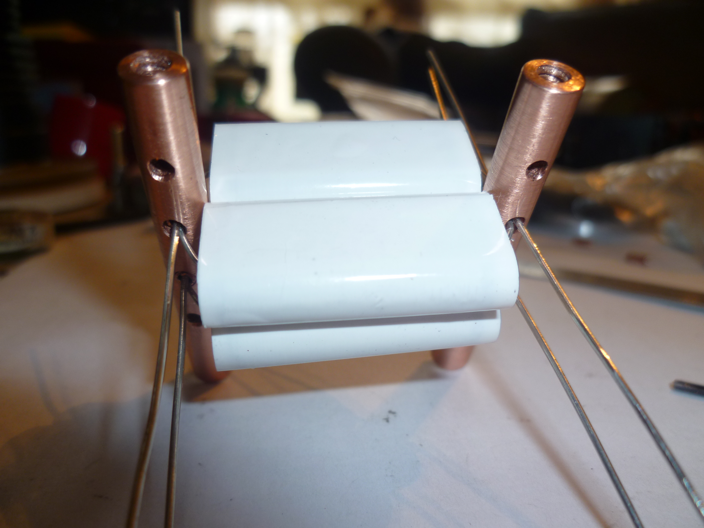
images/proto/P1020020.JPG
