hardboiledfrog/smt-zvs-driver/images/proto/P1020021.JPG

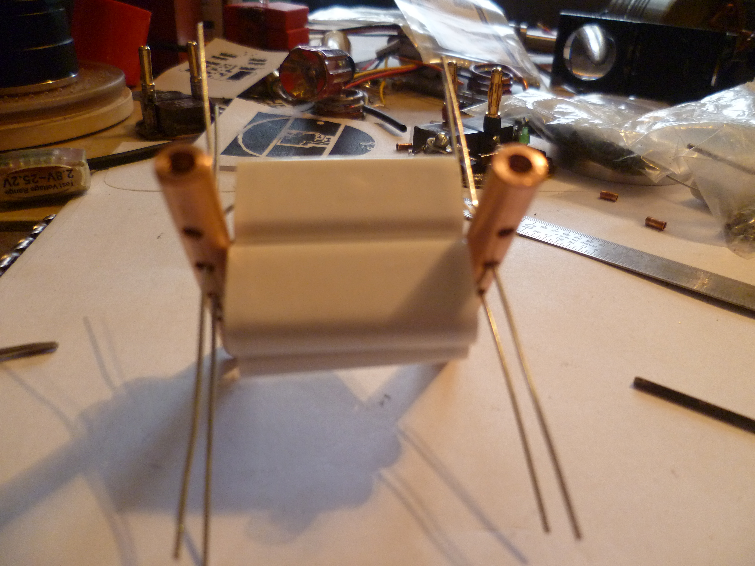
images/proto/P1020021.JPG
