hardboiledfrog/smt-zvs-driver/images/proto/P1020022.JPG

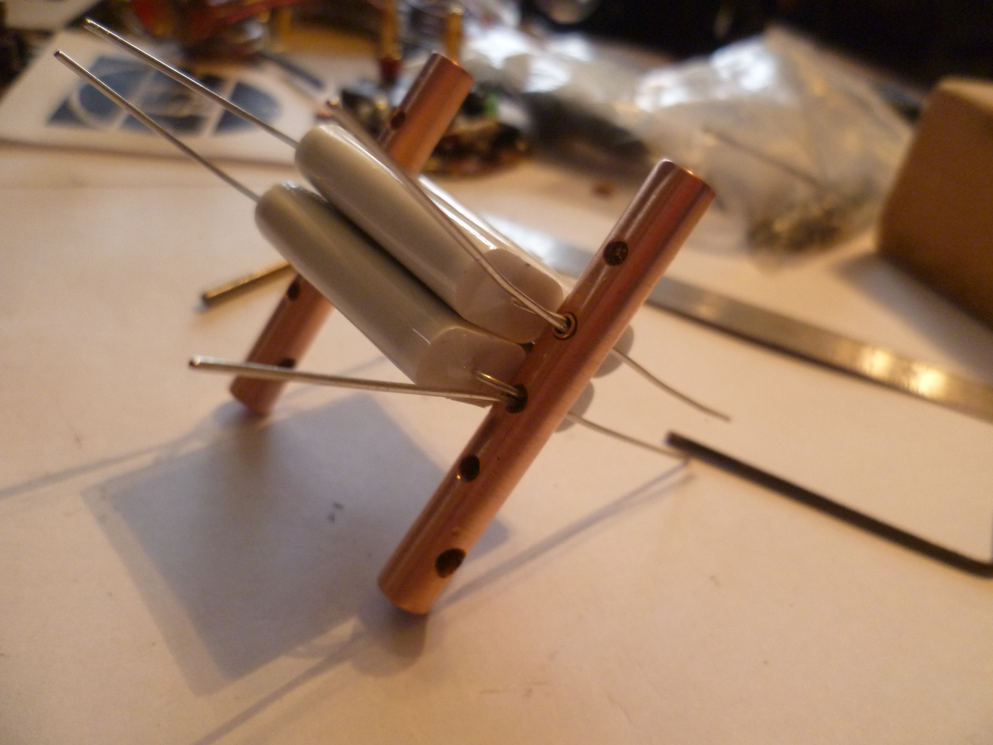
images/proto/P1020022.JPG
