hardboiledfrog/smt-zvs-driver/images/proto/P1020023.JPG

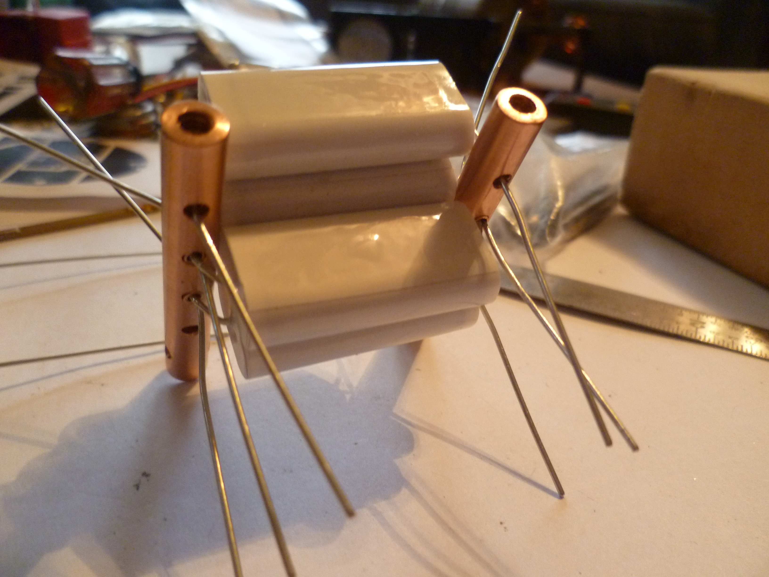
images/proto/P1020023.JPG
