hardboiledfrog/smt-zvs-driver/images/proto/P1020024.JPG

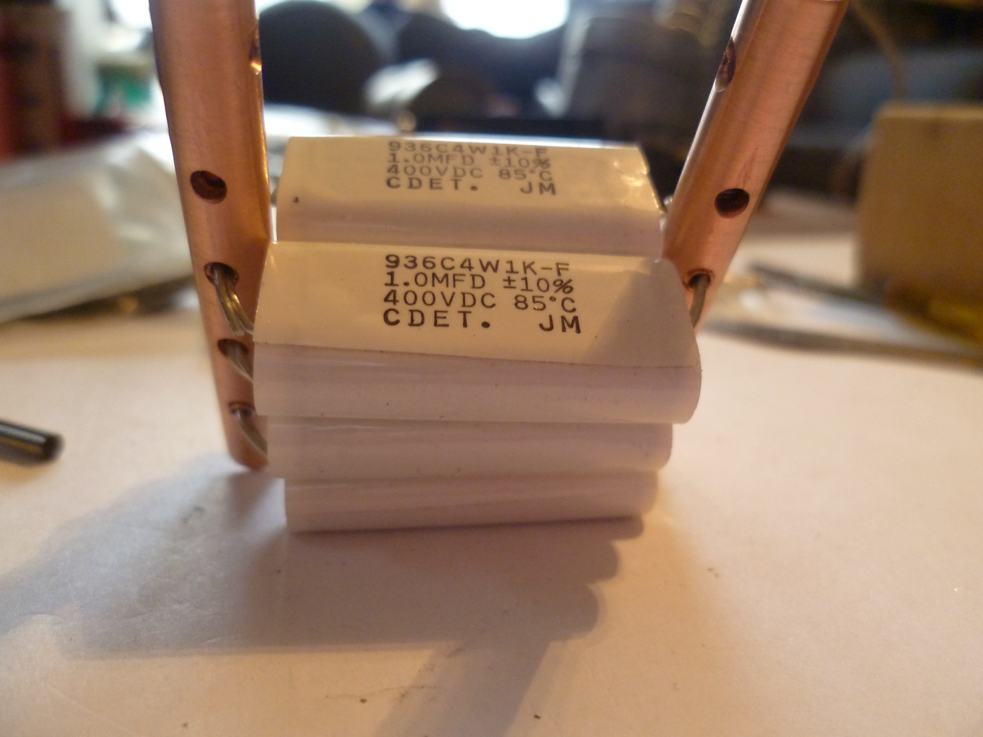
images/proto/P1020024.JPG
