hardboiledfrog/smt-zvs-driver/images/proto/P1020025.JPG

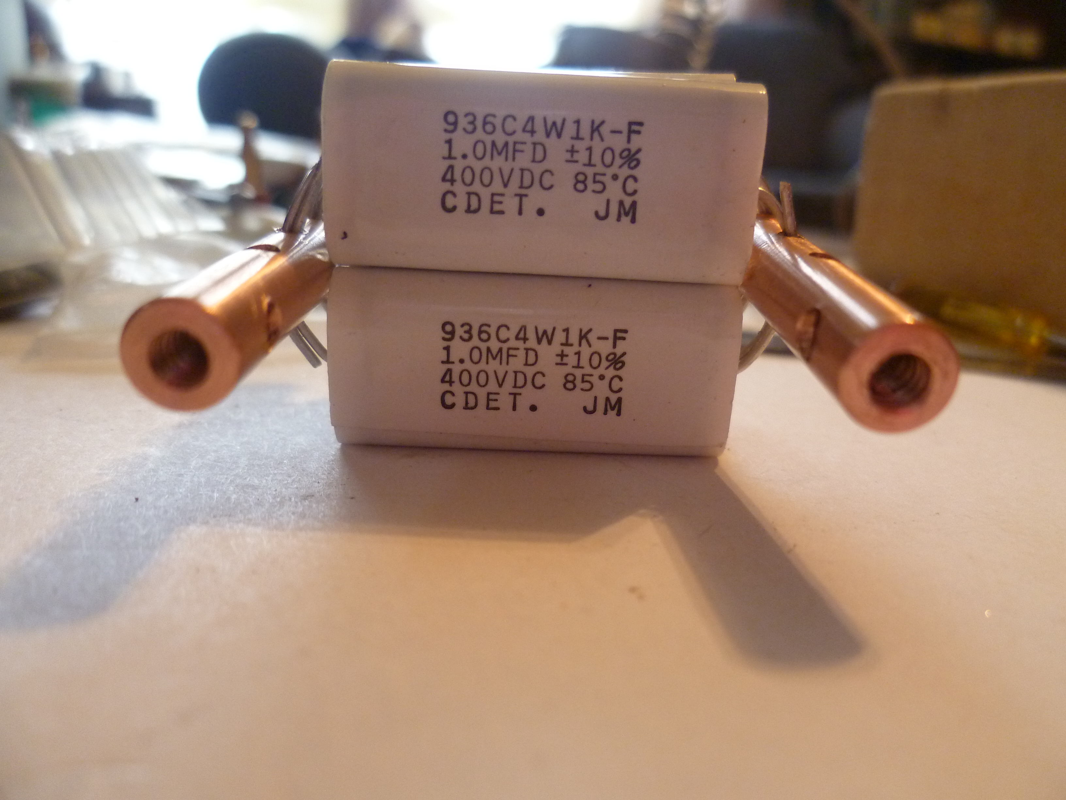
images/proto/P1020025.JPG
