hardboiledfrog/smt-zvs-driver/images/proto/P1020026.JPG

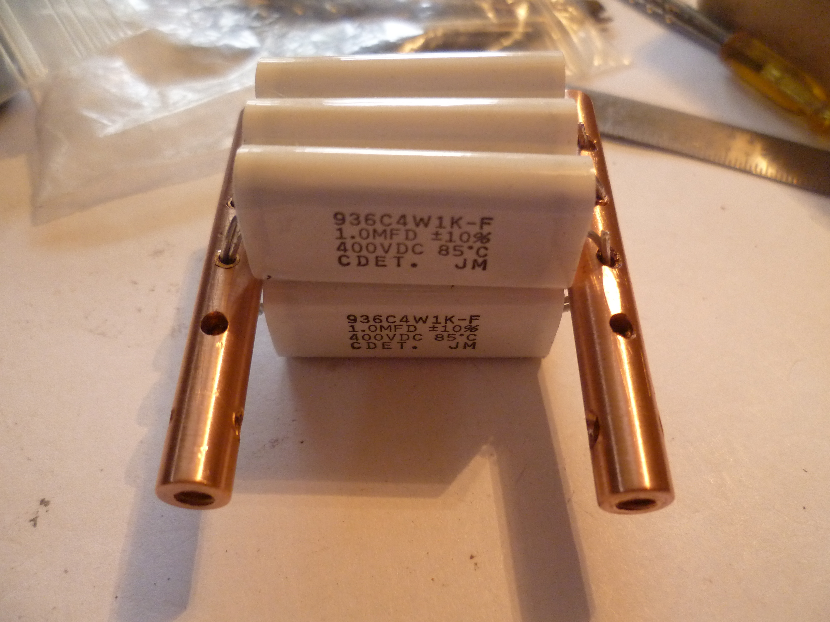
images/proto/P1020026.JPG
