hardboiledfrog/smt-zvs-driver/images/proto/P1020027.JPG

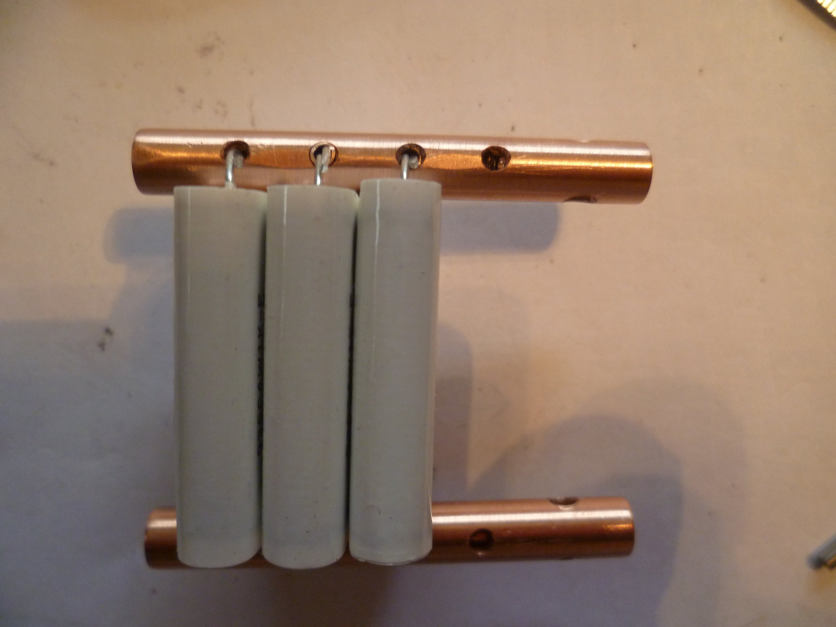
images/proto/P1020027.JPG
