hardboiledfrog/smt-zvs-driver/images/proto/P1020028.JPG

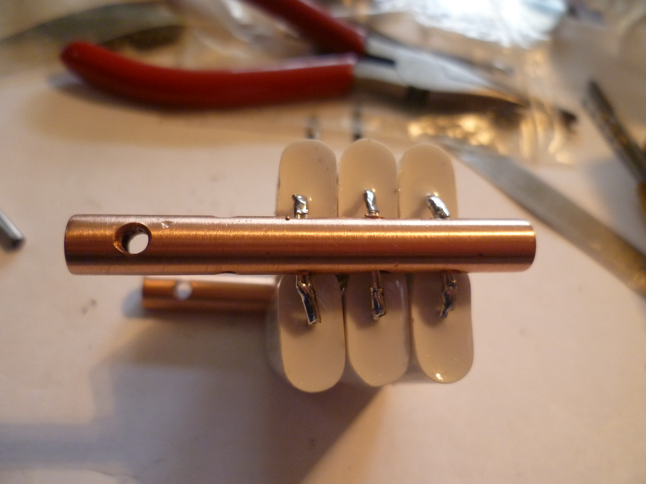
images/proto/P1020028.JPG
