hardboiledfrog/smt-zvs-driver/images/proto/P1020029.JPG

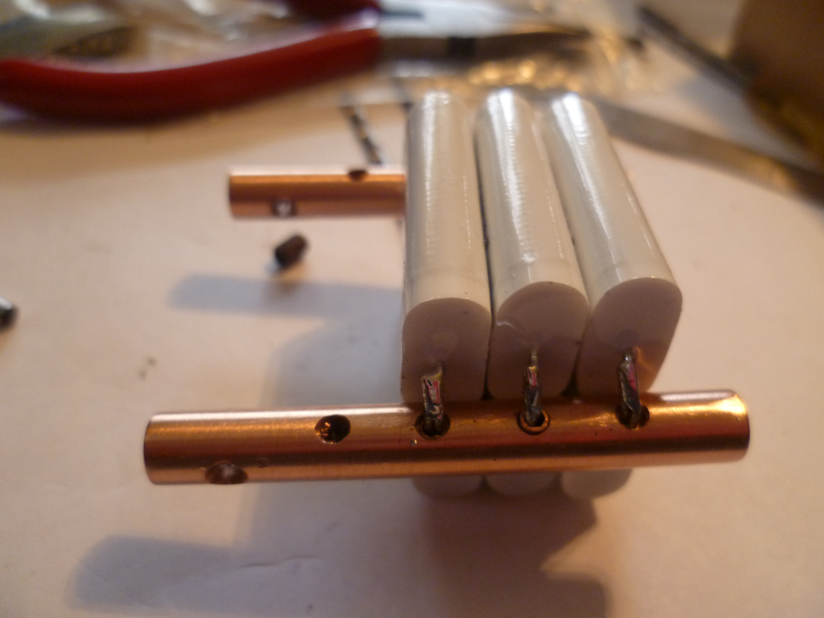
images/proto/P1020029.JPG
