hardboiledfrog/smt-zvs-driver/images/proto/P1020030.JPG

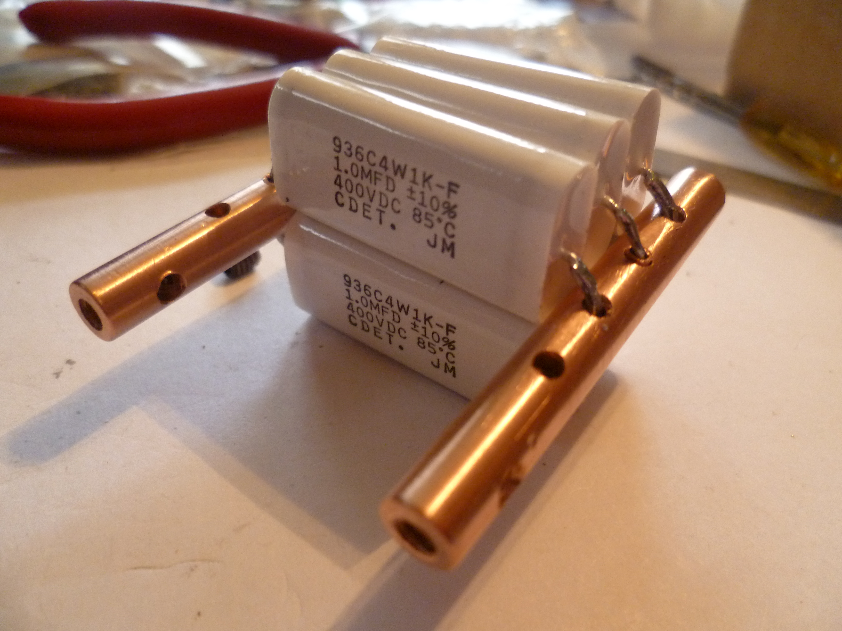
images/proto/P1020030.JPG
