hardboiledfrog/smt-zvs-driver/images/proto/P1020032.JPG

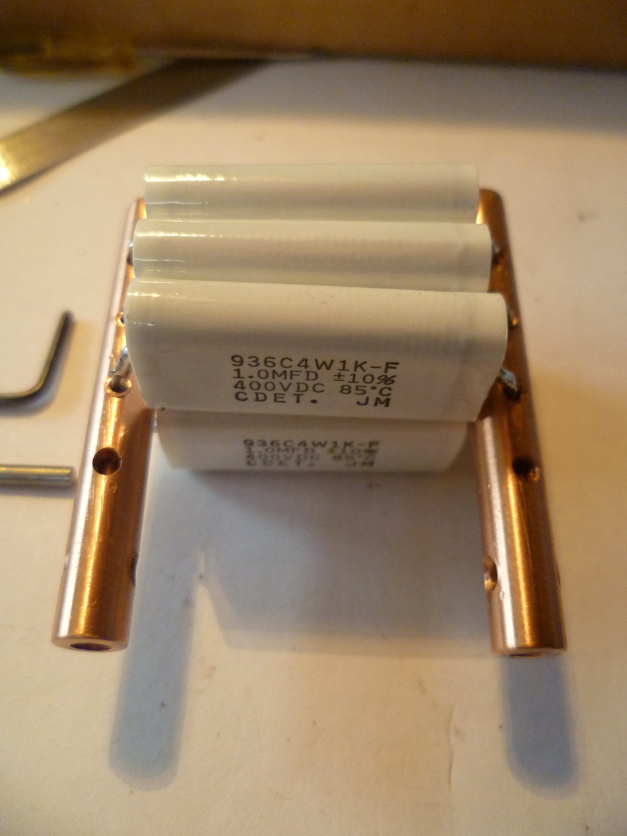
images/proto/P1020032.JPG
