hardboiledfrog/smt-zvs-driver/images/proto/P1020033.JPG

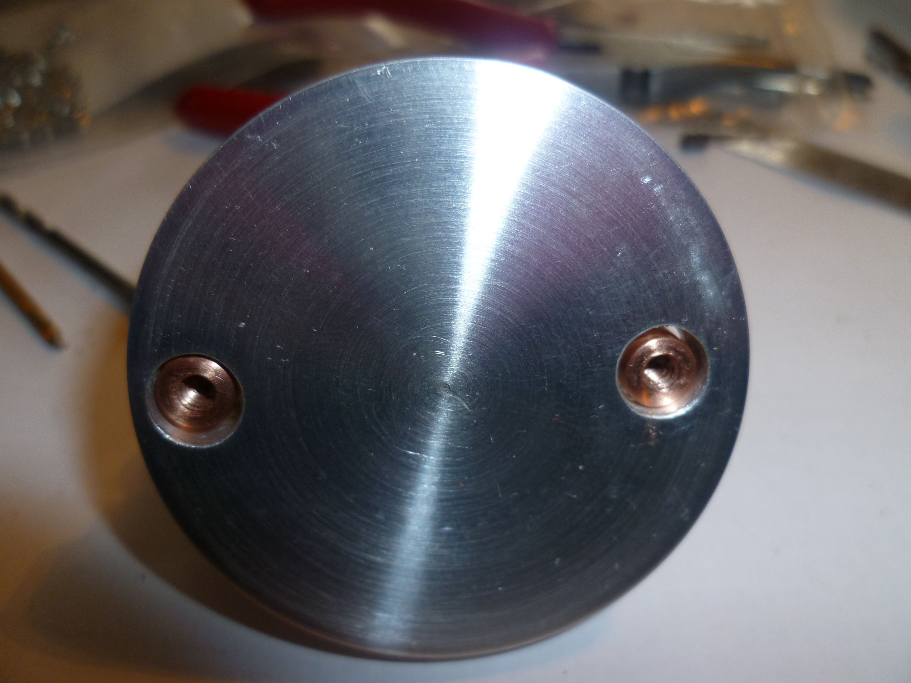
images/proto/P1020033.JPG
