hardboiledfrog/smt-zvs-driver/images/proto/P1020034.JPG

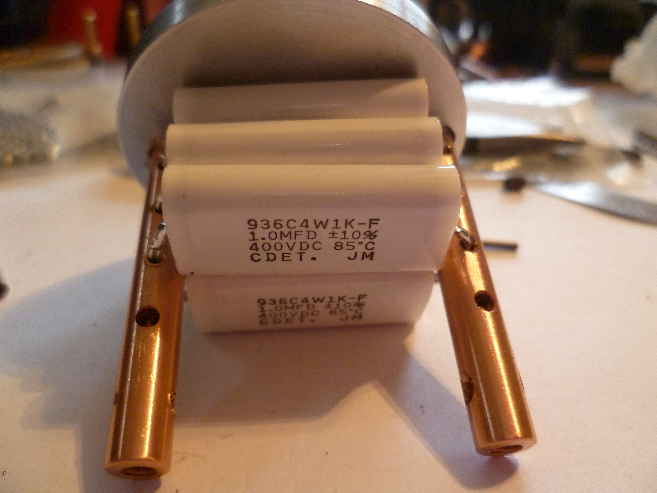
images/proto/P1020034.JPG
