hardboiledfrog/smt-zvs-driver/images/proto/P1020035.JPG

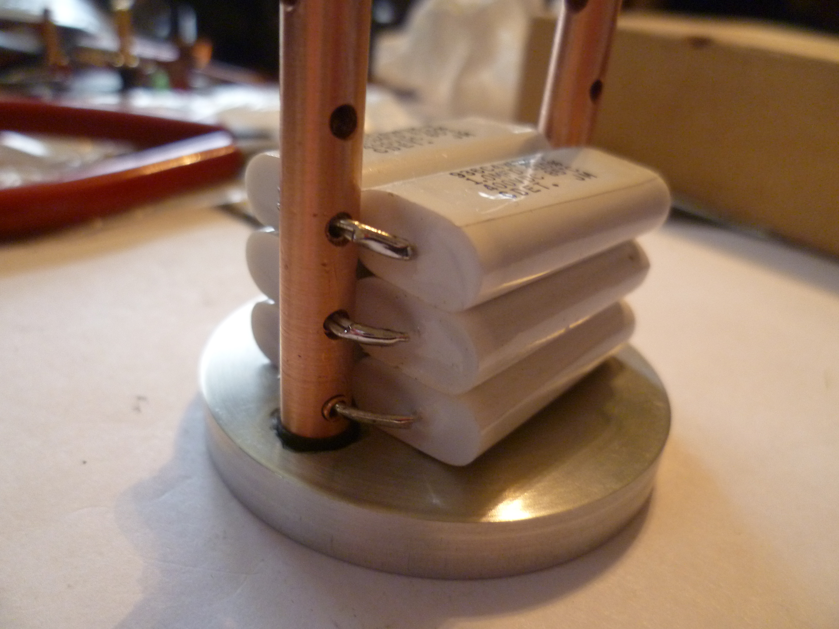
images/proto/P1020035.JPG
