hardboiledfrog/smt-zvs-driver/images/proto/P1020036.JPG

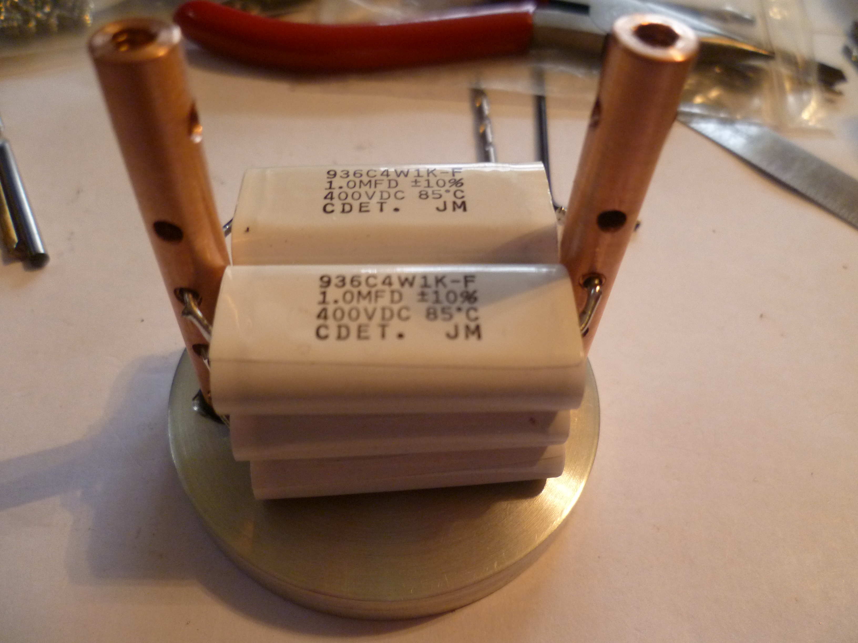
images/proto/P1020036.JPG
