hardboiledfrog/smt-zvs-driver/images/proto/P1020037.JPG

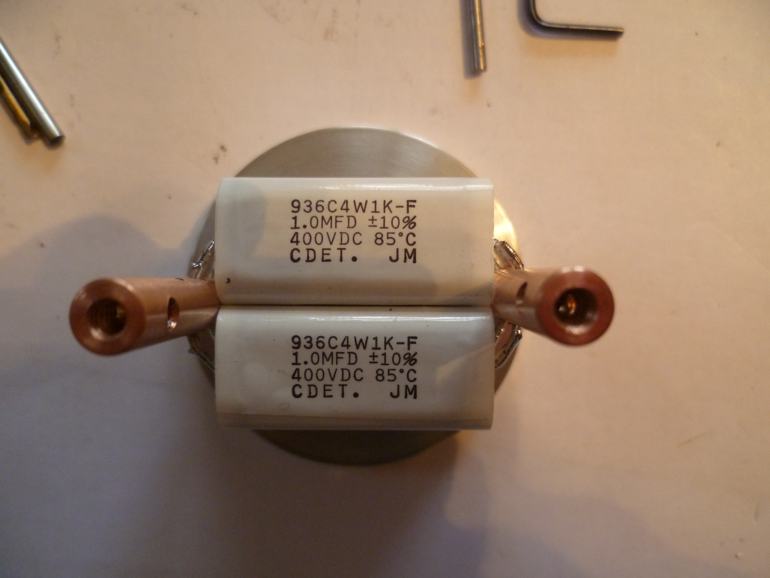
images/proto/P1020037.JPG
