hardboiledfrog/smt-zvs-driver/images/proto/P1020038.JPG

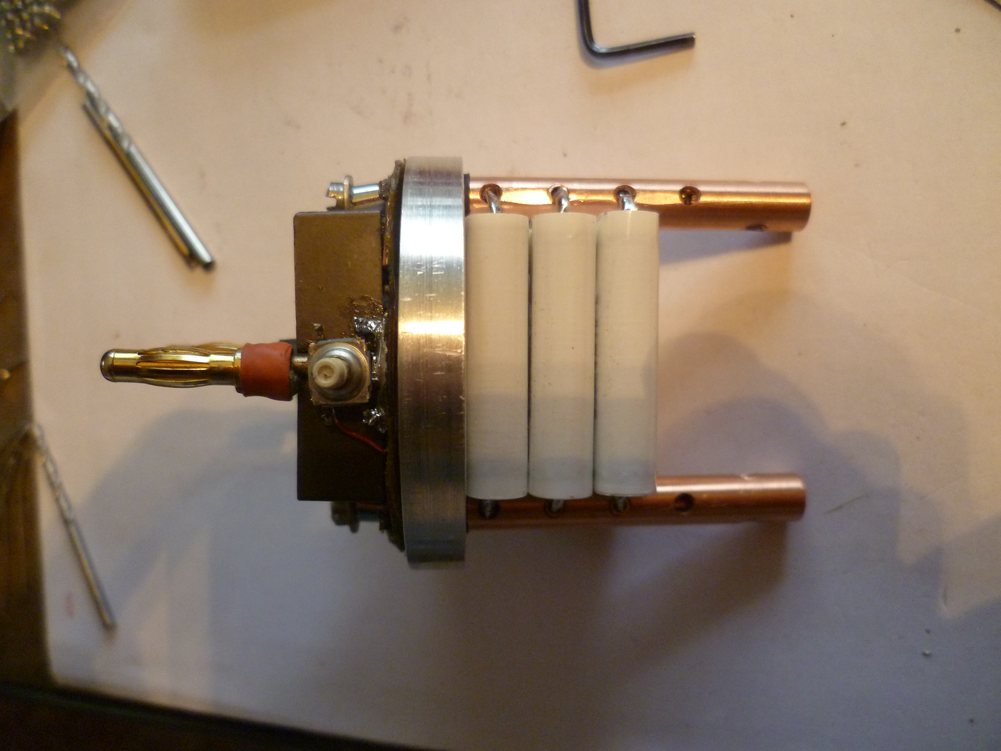
images/proto/P1020038.JPG
