hardboiledfrog/smt-zvs-driver/images/proto/P1020039.JPG

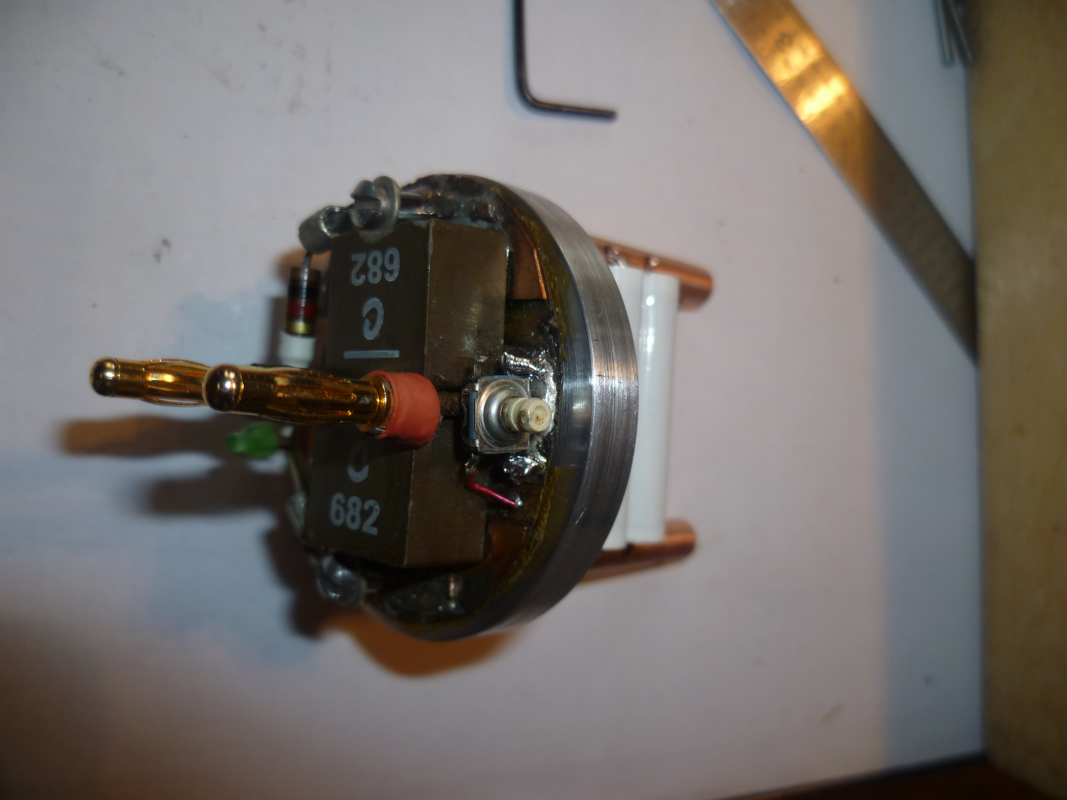
images/proto/P1020039.JPG
