hardboiledfrog/smt-zvs-driver/images/proto/P1020040.JPG

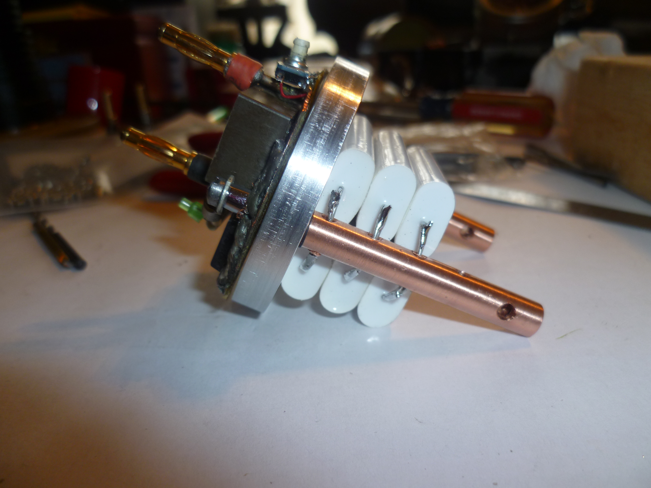
images/proto/P1020040.JPG
