hardboiledfrog/smt-zvs-driver/images/proto/P1020041.JPG

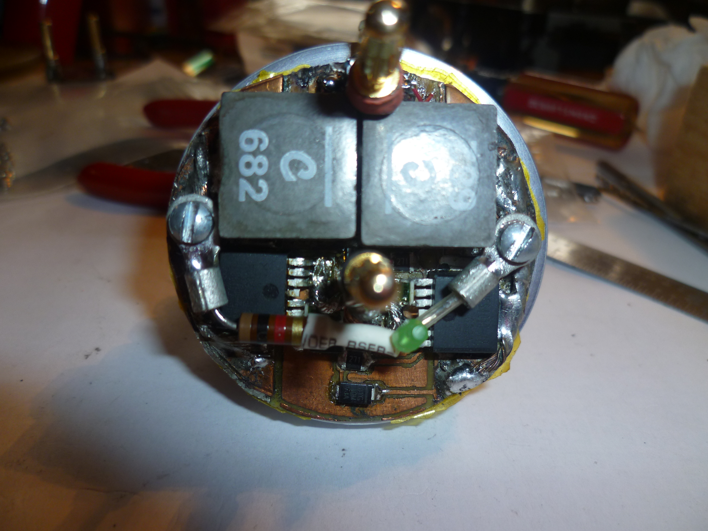
images/proto/P1020041.JPG
