hardboiledfrog/smt-zvs-driver/images/proto/P1020042.JPG

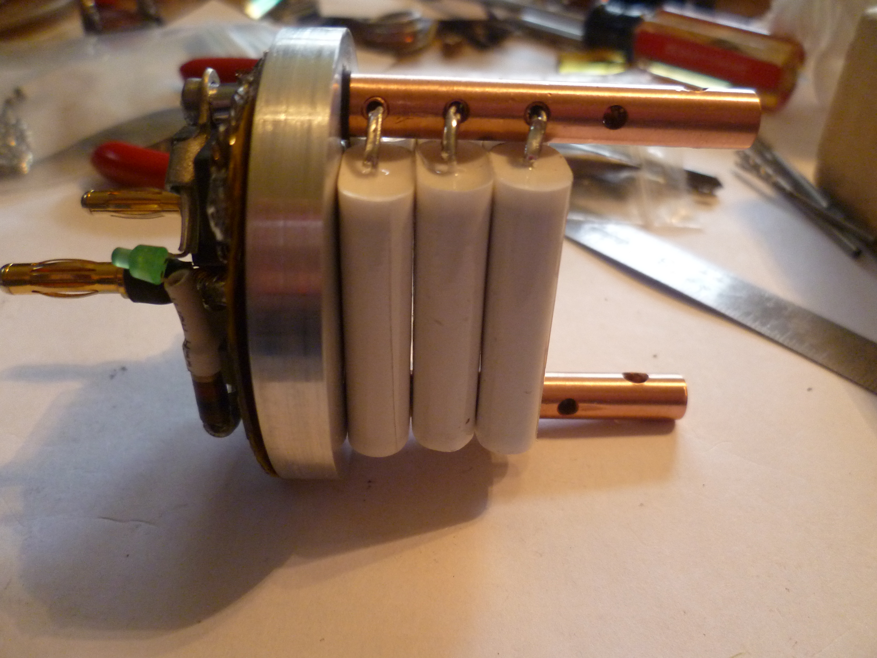
images/proto/P1020042.JPG
