hardboiledfrog/smt-zvs-driver/images/proto/P1020043.JPG

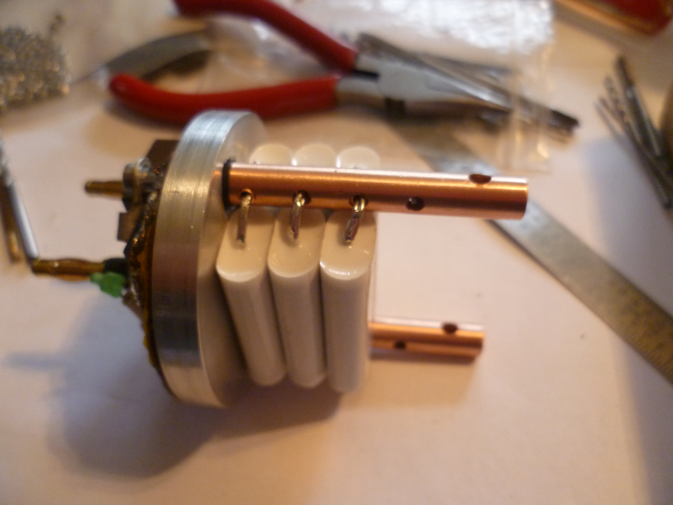
images/proto/P1020043.JPG
