hardboiledfrog/smt-zvs-driver/images/proto/P1020044.JPG

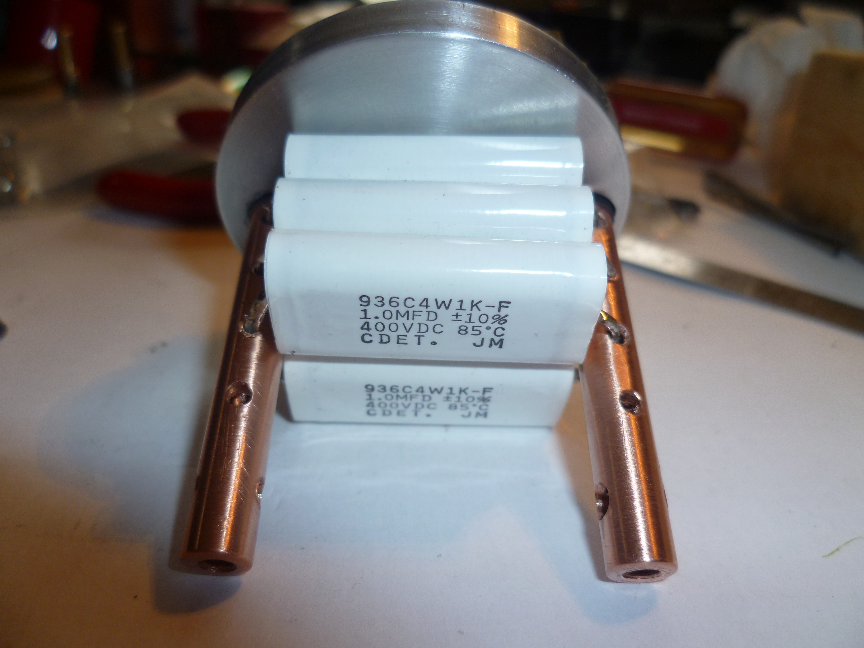
images/proto/P1020044.JPG
