hardboiledfrog/smt-zvs-driver/images/proto/P1020045.JPG

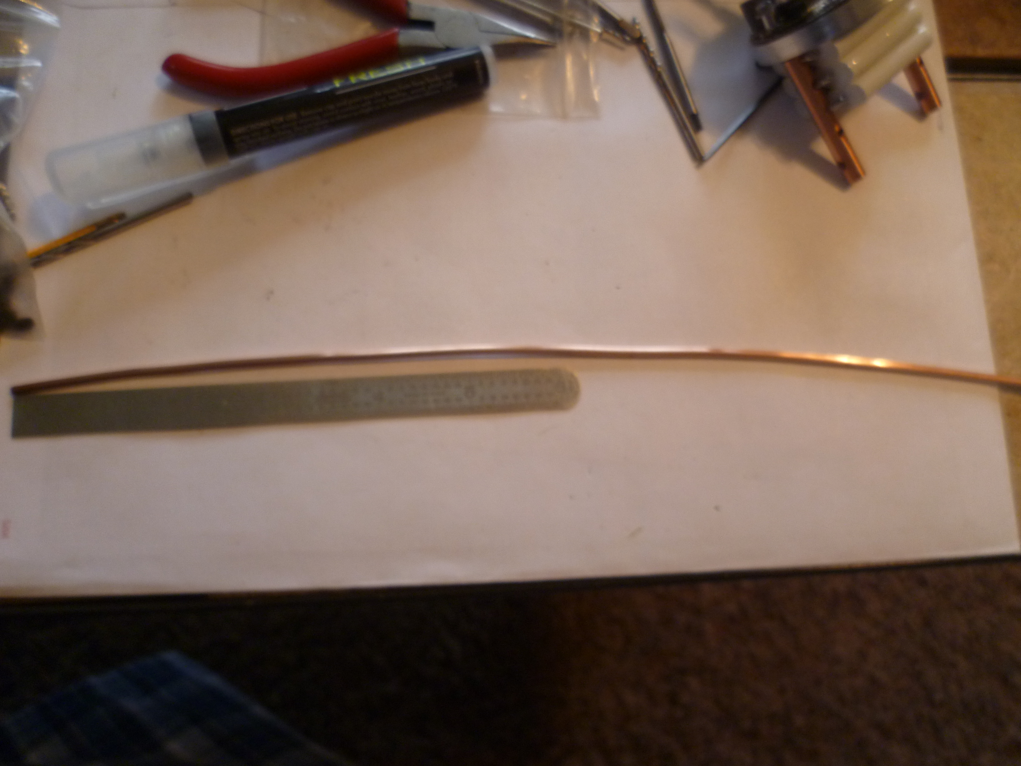
images/proto/P1020045.JPG
