hardboiledfrog/smt-zvs-driver/images/proto/P1020046.JPG

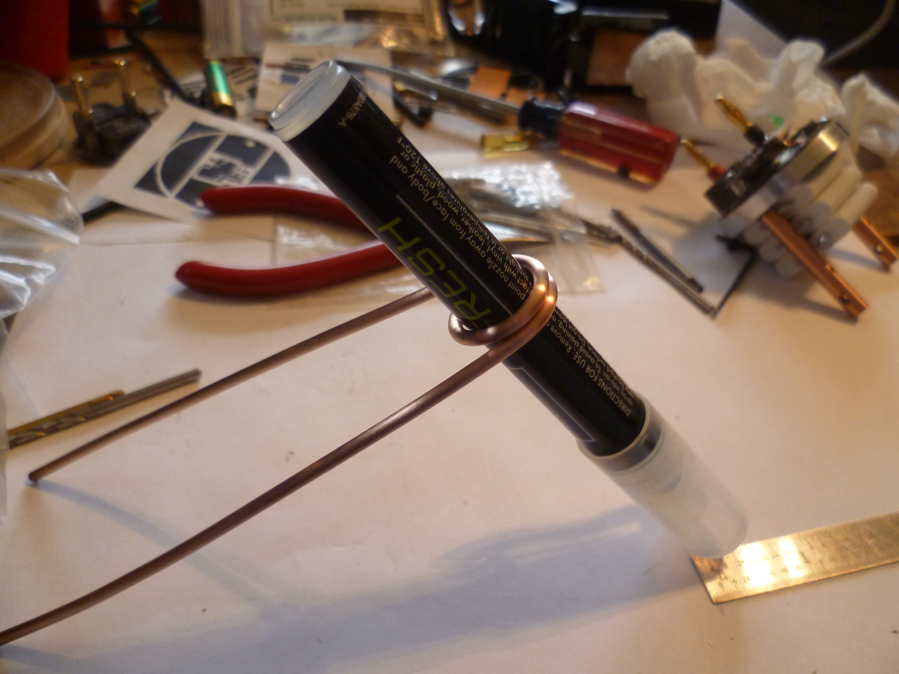
images/proto/P1020046.JPG
