hardboiledfrog/smt-zvs-driver/images/proto/P1020047.JPG

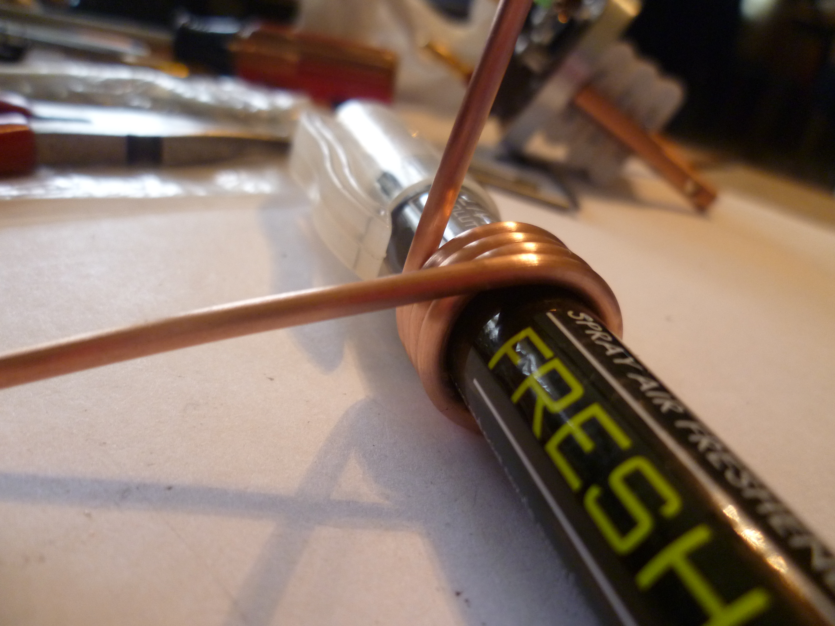
images/proto/P1020047.JPG
