hardboiledfrog/smt-zvs-driver/images/proto/P1020048.JPG

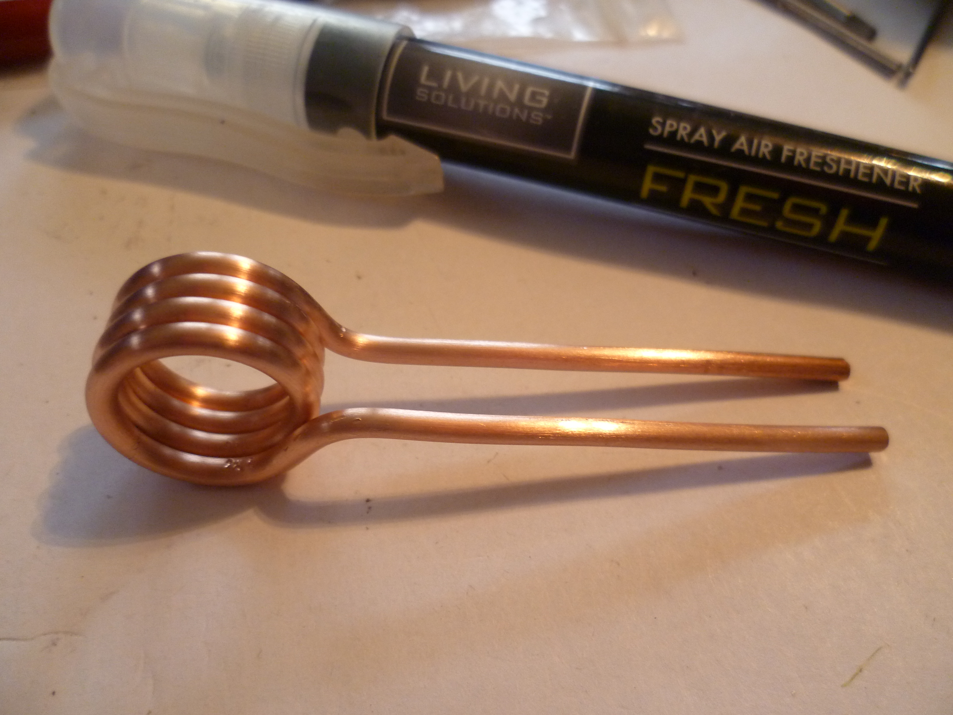
images/proto/P1020048.JPG
