hardboiledfrog/smt-zvs-driver/images/proto/P1020049.JPG

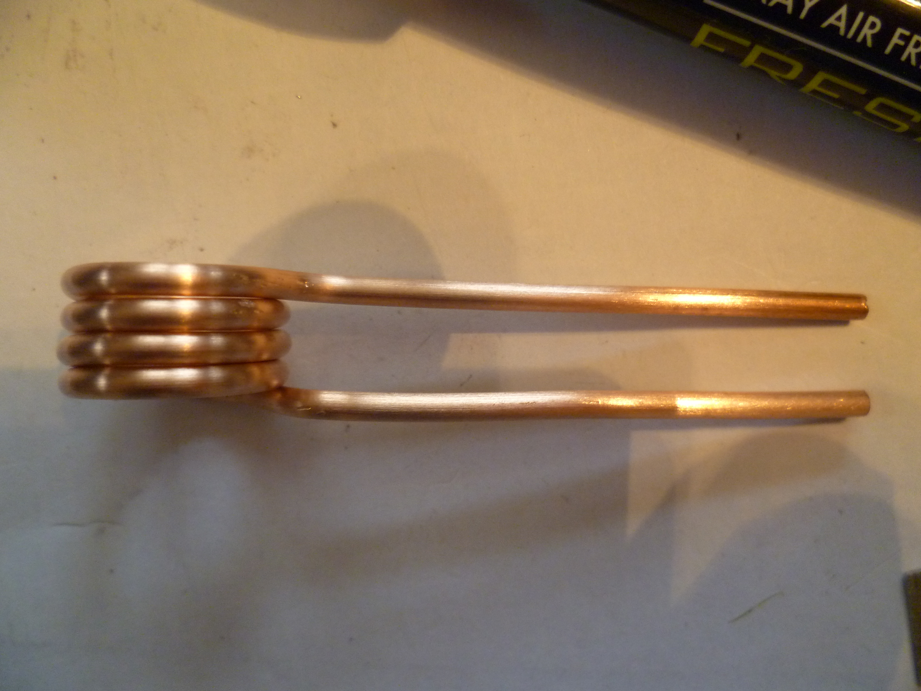
images/proto/P1020049.JPG
