hardboiledfrog/smt-zvs-driver/images/proto/P1020050.JPG

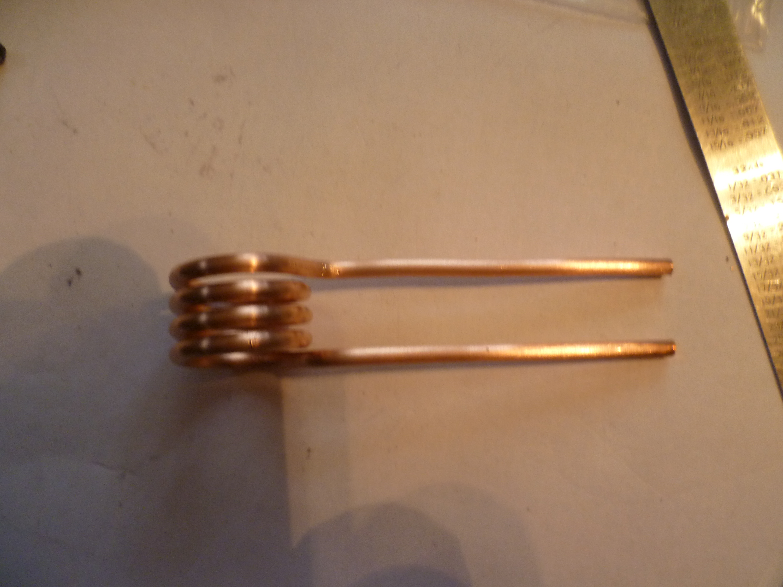
images/proto/P1020050.JPG
