hardboiledfrog/smt-zvs-driver/images/proto/P1020051.JPG

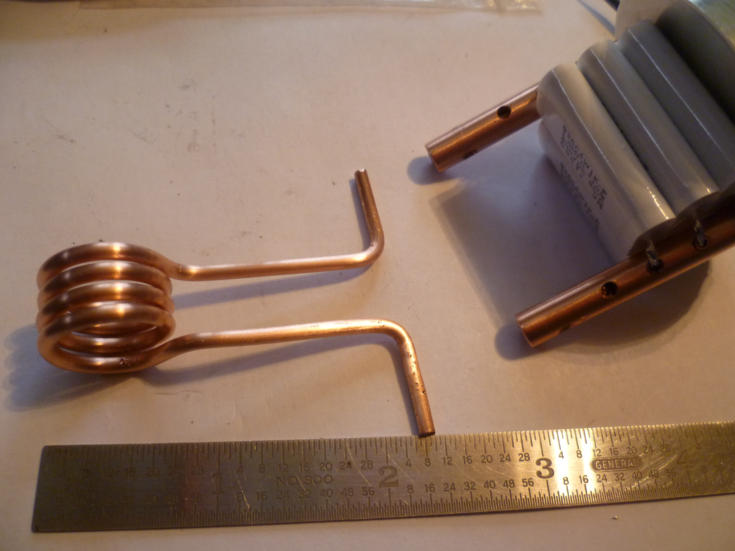
images/proto/P1020051.JPG
