hardboiledfrog/smt-zvs-driver/images/proto/P1020052.JPG

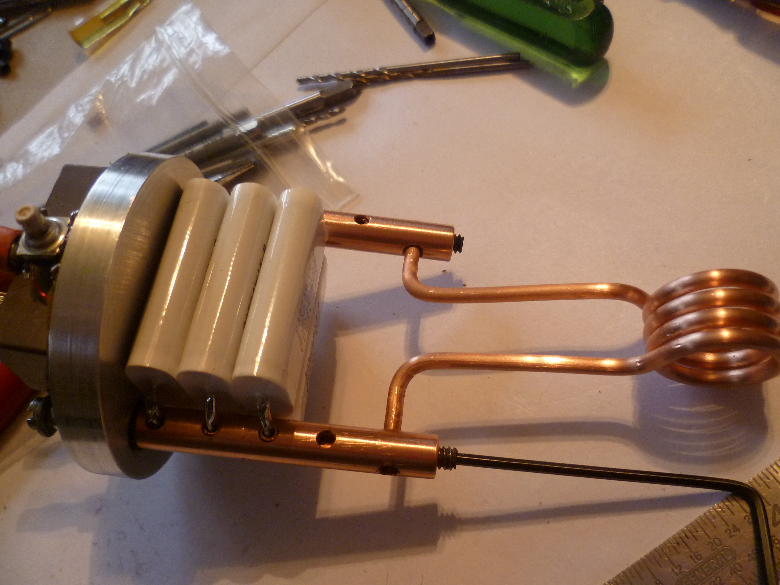
images/proto/P1020052.JPG
