hardboiledfrog/smt-zvs-driver/images/proto/P1020053.JPG

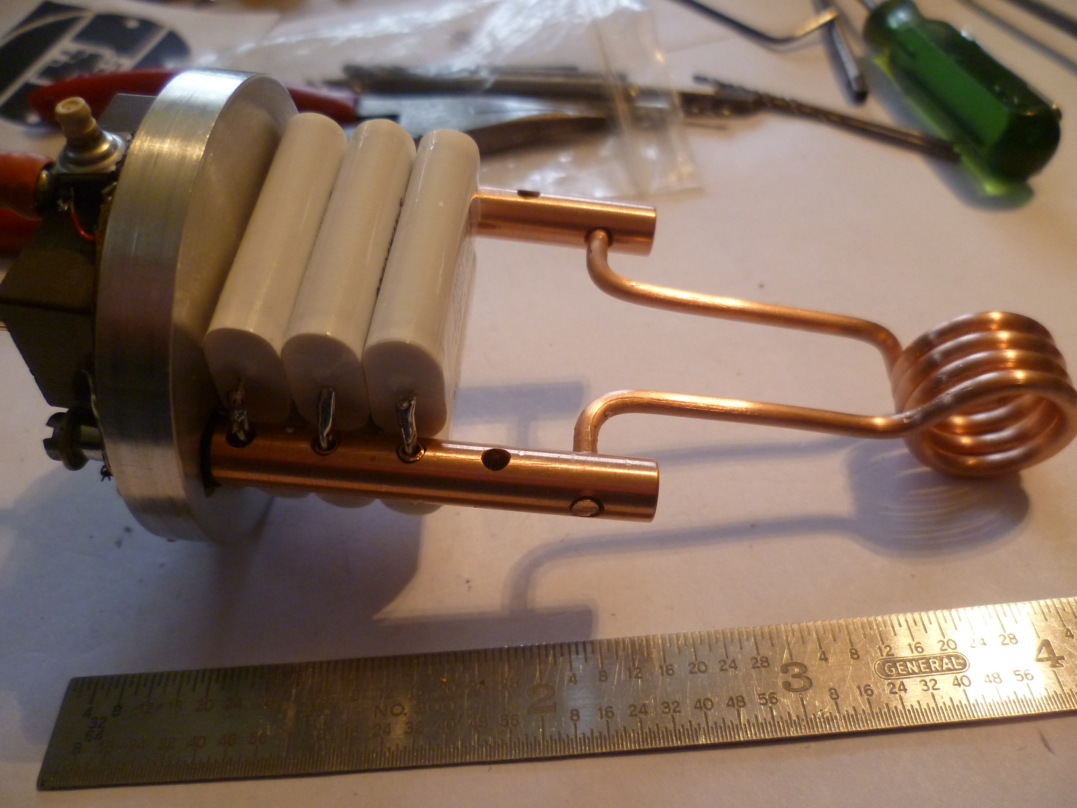
images/proto/P1020053.JPG
