hardboiledfrog/smt-zvs-driver/images/proto/P1020054.JPG

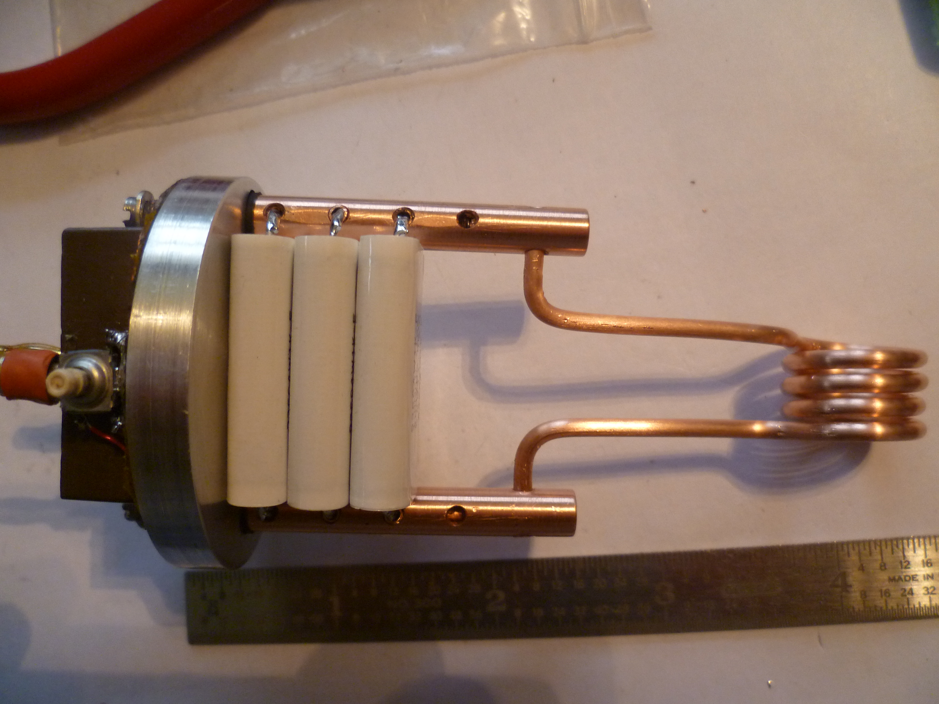
images/proto/P1020054.JPG
