hardboiledfrog/smt-zvs-driver/images/proto/P1020055.JPG

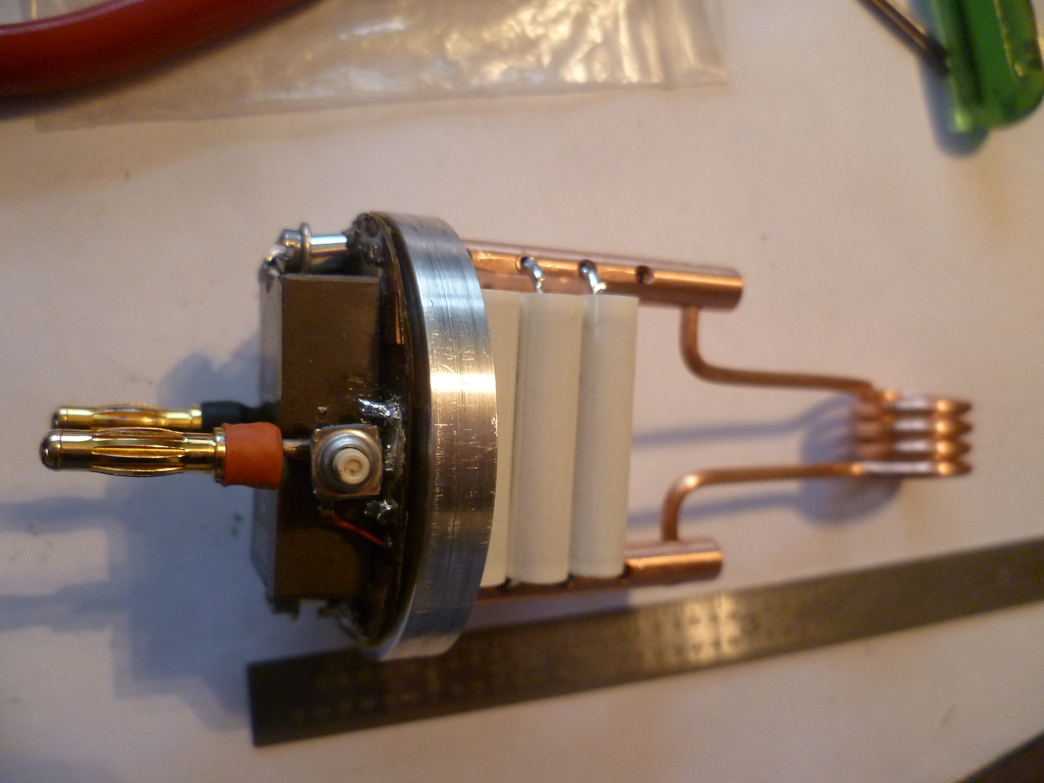
images/proto/P1020055.JPG
