hardboiledfrog/smt-zvs-driver/images/proto/P1020056.JPG

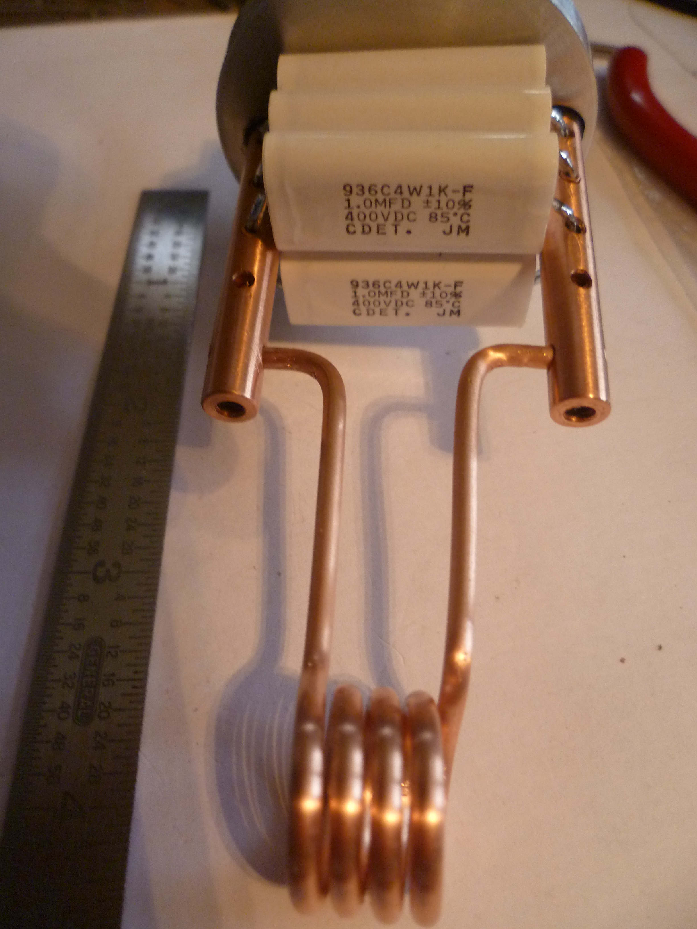
images/proto/P1020056.JPG
