hardboiledfrog/smt-zvs-driver/images/proto/P1020057.JPG

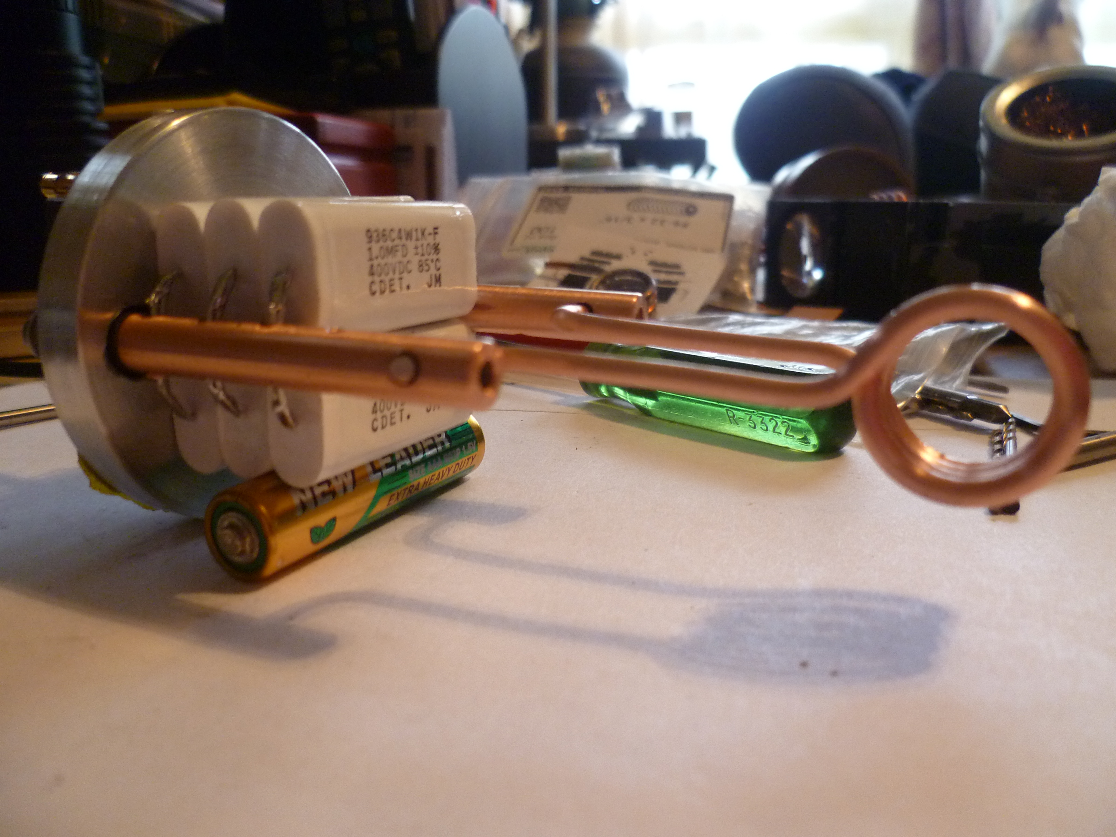
images/proto/P1020057.JPG
