hardboiledfrog/smt-zvs-driver/images/proto/P1020058.JPG

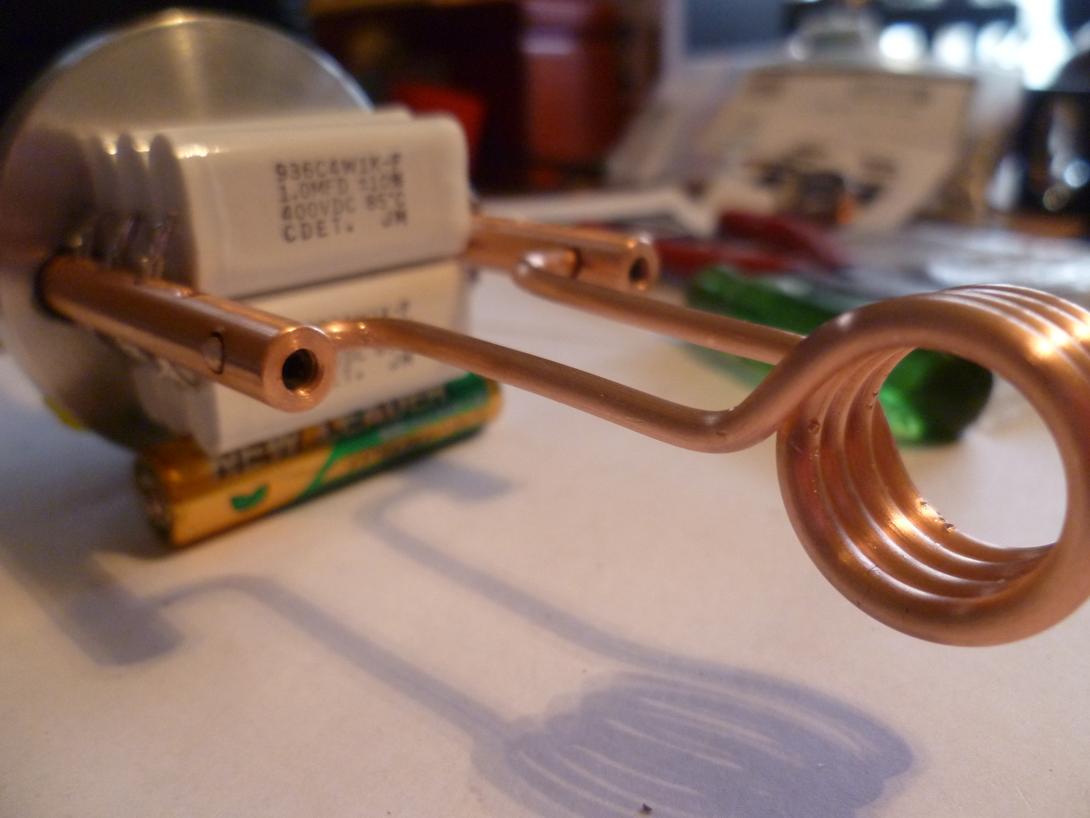
images/proto/P1020058.JPG
