hardboiledfrog/smt-zvs-driver/images/proto/P1020059.JPG

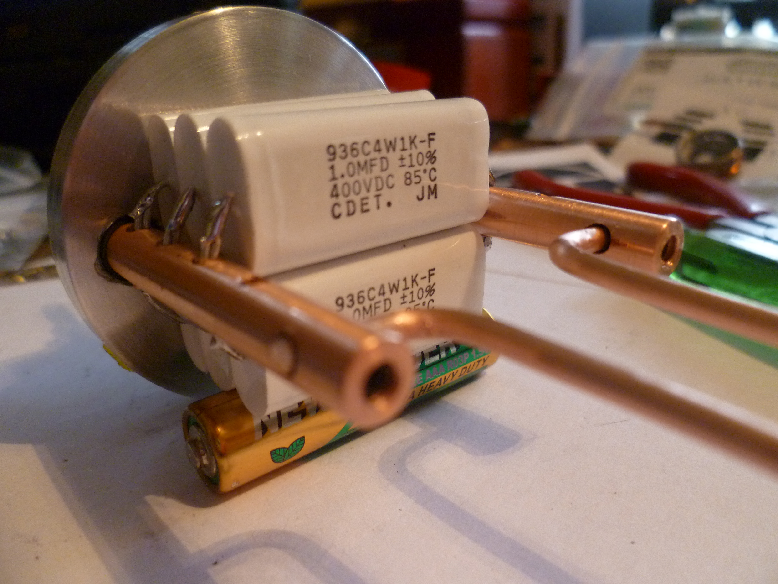
images/proto/P1020059.JPG
